rupret007/story-corner-shelf/development/simplified_shelf_concepts/artist_renderings/16b_structural_arch_peg_rails_prompt.md

# Prompt set for selected direction 16B

Generated with the built-in OpenAI image-generation tool. The user's attached concept-16 image was the edit target. A second targeted edit corrected accessory placement.

## Structural and accessory refinement

```text
Use case: precise-object-edit
Asset type: refined photorealistic interior-design concept, option 16B
Input images: Image 1 is the edit target and chosen design.
Primary request: Preserve the exact closet, camera, lighting, exactly two L-shaped shelf levels, shelf positions, thickness, matte-black PETG material, and simple uncluttered character. Change only the support geometry and cable accessories. Make every support one compact structural arched corbel: a broad vertical PETG wall spine plus a thick curved gusset connected continuously into the shelf cassette's deep underside rib. Keep each curve entirely inside its own bracket footprint; never span an arch between adjacent supports.
Cable organization: mold a slim vertical accessory rail into selected ordinary downward spines. Each rail has three keyed rectangular sockets and flush blank caps. Install only a few removable black-PETG accessories: one short rounded single-cable peg, one three-prong cable-comb peg, and one broad rounded J-hook carrying one small neat coil of black cable. Leave most sockets capped. No pegs at the inside corner or directly beside either doorway.
Style/medium: premium photorealistic architectural visualization, simple, strong-looking, practical.
Materials/textures: all visible shelf cassettes, ribs, arches, wall spines, sockets, caps and peg accessories are matte black 3D-printed PETG with subtle fine layer texture.
Constraints: visible shelf system is 100 percent PETG; arch gussets are thick connected structural ribs, not ornamental outlines; pegs are cable-management accessories only; preserve open wall space.
Avoid: wood, wood grain, plywood, steel, metal brackets, brass, visible metal fasteners, floating shelves, full arcade spans, ornate columns, extra shelves, floor supports, clothes, bins, tools, clutter, tangled cables, oversized hooks, corner pegs, text, labels, logos, watermark.
```

## Targeted placement correction

```text
Use case: precise-object-edit
Asset type: corrected photorealistic interior concept, option 16B
Input images: Image 1 is the edit target.
Primary request: Change only the cable-accessory placement. Preserve the entire room, camera, lighting, two shelves, all shelf dimensions, all structural arched corbels, black PETG material, and all other geometry exactly.
Remove the cable coil, peg, comb, accessory sockets, and accessory rails from the support immediately beside the left doorway and the support immediately beside the right doorway. Keep both doorway-adjacent supports completely smooth and empty. Keep the two supports nearest the inside L-corner completely smooth and empty as well.
Relocate the accessories to safe interior supports on the long wall: place one small neat coiled black cable on a broad rounded PETG J-hook on the second interior support from the left, place one three-prong cable-comb peg on the next interior support, and place one short single-cable peg on a middle interior support. Give only these safe interior supports three keyed sockets with unused sockets closed by flush caps. Most supports remain clean.
Constraints: change only accessory placement; no pegs, sockets, rails, or cables beside either doorway or at the inside corner; all shelf/support/accessory components remain matte black PETG; exactly one neat cable coil; no other objects.
Avoid: altering shelf structure, changing arches, adding full arcade spans, extra shelves, wood, metal, clutter, tangled cables, text, labels, logos, watermark.
```
