rupret007/story-corner-shelf/development/simplified_shelf_concepts/artist_renderings/20b_structural_arch_cable_rails_prompt.md

# Prompt for selected direction 20B

Generated with the built-in OpenAI image-generation tool. `20_black_balanced_arch_petg.png` was the edit target.

```text
Use case: precise-object-edit
Asset type: refined photorealistic interior design concept, concept 20B
Input images: Image 1 is the edit target.
Primary request: Refine only the black PETG shelving in Image 1. Preserve the closet, camera, lighting, exactly two L-shaped shelf levels, black material, shelf positions, and overall clean architectural character. Turn every shallow arch below the shelves into a clearly structural PETG arch-rib corbel: a thick curved compression rib connected continuously to a deep underside box rib, a substantial rear wall spine, and the shelf cassette above, so the load path looks integrated rather than like snap-on decoration.
Cable organization: redesign each safe non-corner downward wall spine as a slim vertical modular accessory rail molded into the PETG support. Give the rail three evenly spaced keyed sockets. Populate selected rails with removable all-PETG accessories: a short single-cable peg, a wider three-cable comb peg with three rounded separated hooks, and a broad J-hook for one neatly coiled cable bundle. Leave several sockets fitted with flush blank caps so it remains clean. Show only two small neat dark cable coils as usage examples; keep most pegs empty. All hooks have rounded tips and short upturned retainers. Do not put pegs at the inside corner or beside either doorway.
Style/medium: premium photorealistic architectural visualization; restrained, simple, genuinely useful.
Materials/textures: every shelf cassette, box rib, arch-rib corbel, wall spine, rail, socket, blank cap, and cable peg is matte black 3D-printed PETG with subtle fine layer texture.
Constraints: visible shelf system is 100 percent PETG; no wood or metal; arches must be connected structural ribs, not thin ornamental outlines; pegs are explicitly cable-management accessories, not shelf-load supports; preserve generous clear wall area and an uncluttered appearance.
Avoid: changing the room or camera, extra shelf levels, floor-to-ceiling columns, dense ornament, decorative medallions, metal fasteners, wood grain, steel brackets, unsupported floating shelves, clothes, bins, storage clutter, labels, text, logos, watermark, pegs at corner service zones, tangled cables, oversized hooks, tool storage.
```
