rupret007/story-corner-shelf/development/simplified_shelf_concepts/artist_renderings/prompts_01_05.md

# All-PETG artist-rendering prompts: options 01–05

Generated with the built-in image-generation tool. The local R6 rendering below was supplied as a **composition and room-layout reference only**, never as an edit target:

`PETG_Closet_Shelf/development/r6/assets/artist_rendering_all_petg_two_level_exact_6_plus_3.png`

These are visual concept images, not dimensioned construction drawings. The prompts request a six-bay long run and a three-bay return; final counts, part seams, wall attachment, spans, and capacity must be established by CAD and physical testing.

## 01 — Black minimalist ribbed PETG

```text
Use case: photorealistic-natural
Asset type: homeowner design-choice artist rendering, all-PETG option 01
Primary request: Generate a completely new photorealistic architectural rendering of a simple, strong-looking, tasteful closet shelf system made entirely from visibly 3D-printed PETG. Image 1 is only a reference for the small closet geometry, doorway viewpoint, corner perspective, and two-level L-shaped layout; do not copy its ornate style.
Scene/backdrop: the same kind of small empty white closet, viewed from the doorway toward the inside corner, with plain white walls and ceiling, pale neutral floor, and cropped doorway edges at both sides.
Subject: Exactly two shelf elevations and no others. Each elevation is one continuous L-shaped PETG shelf: a longer run along the back/left wall divided visually into exactly six structural bays and a shorter right-wall return divided into exactly three bays. Build each shelf as a deep matte-black PETG ribbed box-beam cassette with a smooth flat usable top, thick front fascia, and subtle horizontal print-layer texture. Under the cassette, use simple stout triangular PETG corbels at bay divisions, integrated with short vertical PETG mounting blocks against the wall. The mounting blocks visibly meet both wall and shelf and conceal the actual stud fasteners inside them, so the shelf never appears to float. Keep the system minimalist and repeatable, with broad load paths and generous radii rather than delicate detail. Add three small upward-curved cable pegs total on selected lower-level vertical mounting blocks only; the pegs are clearly secondary and unobtrusive.
Style/medium: high-end photorealistic interior product visualization, honest FDM-printed PETG construction, practical rather than sci-fi.
Composition/framing: wide landscape, eye-level architectural camera, straight verticals, closely matching Image 1's corner composition; show both complete L-shaped levels and the long/short runs clearly.
Lighting/mood: soft neutral ceiling light, realistic shadows under every corbel, calm and clean.
Color palette: white room and monochrome matte-black PETG.
Materials/textures: satin-matte black PETG, fine visible layer lines at close inspection, molded-looking but unmistakably 3D printed, consistent plastic sheen; no material substitutions.
Constraints: ALL shelf boards, cassettes, ribs, fascia, corbels, mounting blocks, vertical supports, and cable pegs are PETG; exactly two L-shaped shelf levels; six bays on the long run and three on the short return when visible; physically connected support paths; empty shelves; no floor posts; no visible fasteners or metal.
Avoid: any wood, wood grain, plywood, lumber, steel, metal, brass, chrome, aluminum, metal brackets, stone, glass, impossible floating structure, arches, columns reaching the floor, excessive ornament, extra shelf levels, cabinets, bins, baskets, wire shelving, clothes rods, rails, stored items, people, text, labels, logos, and watermarks.
```

## 02 — Black Art Deco PETG

```text
Use case: photorealistic-natural
Asset type: homeowner design-choice artist rendering, all-PETG option 02
Primary request: Generate a completely new photorealistic architectural rendering of a buildable closet shelf system made entirely from visibly 3D-printed black PETG, using restrained Art Deco geometry. Image 1 is only a reference for the small closet, doorway camera, corner composition, and two-level L-shaped plan; do not copy its ornate architecture.
Scene/backdrop: a small empty white closet viewed from the doorway toward the inside corner, plain white walls and ceiling, pale neutral floor, cropped door jambs at both sides.
Subject: Exactly two shelf elevations. Each elevation is one continuous L-shaped all-PETG shelf: a long back/left-wall run organized into exactly six equal structural bays and a shorter right-wall return organized into exactly three bays. Use deep black PETG torsion-box shelf cassettes with flat usable tops and a modest three-step front fascia. Support them with repeated stout triangular PETG corbels integrated into vertically fluted wall-mounting blocks; each block has only three shallow vertical flutes and a simple stepped foot, giving a clean 1930s Art Deco rhythm without filigree. Concealed fasteners sit inside the printed mounting blocks, with no visible hardware. Make the PETG supports broad, thick, and clearly connected to shelf underside and wall. No cable pegs in this option.
Style/medium: photorealistic high-end residential interior product rendering, restrained geometric Art Deco, honest FDM-plastic construction.
Composition/framing: wide landscape architectural view, eye-level, straight verticals, closely matching Image 1's useful corner framing; both complete shelf levels and both returns visible.
Lighting/mood: soft neutral ceiling light with controlled shadows that reveal the step and flute geometry, polished but believable.
Color palette: bright white closet and satin black PETG only.
Materials/textures: consistent satin-black PETG with fine horizontal layer lines, subtle plastic sheen, printed seams at repeatable module joints, no imitation of wood or metal.
Constraints: every shelf board/cassette, fascia, rib, corbel, wall block, vertical support, and decorative detail is PETG; exactly two L-shaped levels; six long-run bays and three return bays when visible; strong-looking connected load paths; empty room; no floor posts; no exposed fasteners.
Avoid: wood, wood grain, plywood, lumber, steel, metal, brass, gold, chrome, aluminum, metal brackets, stone, glass, floating shelves, pointed Gothic arches, ornate columns, excessive ornament, fan/sunburst motifs, extra shelf levels, cabinets, bins, baskets, rails, rods, hooks, pegs, wires, stored items, people, text, labels, logos, and watermarks.
```

## 03 — Black restrained neo-Gothic PETG

```text
Use case: photorealistic-natural
Asset type: homeowner design-choice artist rendering, all-PETG option 03
Primary request: Generate a completely new photorealistic architectural rendering of a simple, strong-looking closet shelf system made entirely from visibly 3D-printed black PETG, with a restrained neo-Gothic structural motif. Image 1 is only a reference for the small closet geometry, doorway viewpoint, corner perspective, and two L-shaped shelf elevations; radically simplify its ornament.
Scene/backdrop: a small empty white closet viewed from its doorway toward the inside corner, plain white walls and ceiling, pale floor, narrow doorway edges visible on both sides.
Subject: Exactly two shelf elevations, no more. Each is one continuous L-shaped PETG shelf with a long back/left-wall run organized into exactly six equal structural bays and a short right-wall return organized into exactly three bays. Use thick black PETG hollow box-cassette shelves with smooth flat usable tops and a plain narrow fascia. Below each shelf, repeated stout PETG wall trusses define a single shallow pointed arch per bay: two broad diagonal ribs rise from compact vertical wall-mount blocks to the shelf underside and meet in a restrained pointed apex. Keep ribs chunky and engineering-led, with generous radii and no tiny decoration. Concealed stud fasteners are fully hidden inside the PETG wall blocks, leaving no visible metal. Make every support visibly contact wall and underside, with a credible uninterrupted load path. No cable pegs in this option.
Style/medium: high-end photorealistic residential interior product visualization; modern neo-Gothic restraint, not fantasy architecture; honest FDM-printed plastic.
Composition/framing: wide landscape architectural view, eye-level camera, straight verticals, closely matching Image 1's corner composition; show both complete L-shaped levels and both runs.
Lighting/mood: soft neutral ceiling light; gentle realistic shadows clarify the pointed trusses; calm and uncluttered.
Color palette: white closet and monochrome satin-black PETG.
Materials/textures: consistent PETG plastic sheen, visible fine layer texture and modular print seams, no imitation wood or metal.
Constraints: all shelf cassettes, fascia, ribs, trusses, corbels, wall blocks, and vertical supports are PETG; exactly two L-shaped levels; six long-run bays plus three return bays when visible; empty room; connected and strong-looking; no floor posts; no exposed hardware.
Avoid: wood, wood grain, plywood, lumber, steel, metal, brass, gold, chrome, aluminum, metal brackets, stone, glass, floating shelves, elaborate arches, tracery, finials, columns, capitals, dentils, ornamental overload, extra shelf levels, cabinets, bins, baskets, rails, clothes rods, hooks, cable pegs, cables, stored items, people, text, labels, logos, and watermarks.
```

## 04 — Warm-ivory mid-century PETG

```text
Use case: photorealistic-natural
Asset type: homeowner design-choice artist rendering, all-PETG option 04
Primary request: Generate a completely new photorealistic architectural rendering of a simple, strong-looking closet shelf system made entirely from visibly 3D-printed warm-ivory PETG, with restrained mid-century rounded geometry. Image 1 is only a reference for the small closet, doorway camera, inside-corner composition, and two L-shaped shelf elevations; do not copy its ornate black architecture.
Scene/backdrop: a small empty white closet viewed from the doorway toward the inside corner, plain white walls and ceiling, pale neutral floor, door jambs cropped at both sides.
Subject: Exactly two shelf elevations. Each elevation is one continuous L-shaped all-PETG shelf: a long run on the back/left wall arranged into exactly six equal structural bays and a shorter right-wall return arranged into exactly three bays. Construct each from modular warm-ivory PETG hollow shelf cassettes with smooth flat usable tops, a softly rounded bullnose-like PETG front fascia, and internal printed ribs. Below, use broad rounded triangular PETG web corbels integrated with capsule-ended vertical PETG wall-mount blocks, all at realistic bay divisions. Keep the forms thick, simple, repeatable, and friendly—subtle 1950s product-design softness, not decorative furniture. Concealed fasteners are fully hidden inside the printed wall blocks; no hardware is visible. Add exactly three modest molded PETG cable pegs on selected lower-level wall blocks, each a short rounded upward hook; keep all other supports peg-free.
Style/medium: high-end photorealistic residential interior product visualization, soft mid-century modern geometry, honest FDM PETG construction.
Composition/framing: wide landscape architectural view at eye level with straight verticals, closely matching Image 1's corner framing; show both complete L-shaped levels, long run, and short return.
Lighting/mood: warm-neutral ceiling illumination with gentle shadows, bright and welcoming, realistic rather than stylized.
Color palette: clean white room, solid warm ivory PETG with a slight cream tone.
Materials/textures: uniform satin PETG plastic, fine print-layer texture and clean module seams; the shelf surface is plastic, never timber.
Constraints: all shelf cassettes, fascia, ribs, corbels, wall blocks, vertical supports, and pegs are PETG; exactly two L-shaped levels; six long-run bays and three return bays when visible; empty shelves; visible connected load paths; no floor posts; no exposed hardware.
Avoid: any wood or wood grain, plywood, lumber, steel, metal, brass, chrome, aluminum, metal brackets, stone, glass, ceramic, floating spans, skinny delicate brackets, ornate arches, columns, excessive ornament, extra shelf levels, cabinets, bins, baskets, wire shelving, clothes rods, rails, dangling cables, stored objects, people, text, labels, logos, and watermarks.
```

## 05 — Graphite industrial hex-rib PETG

```text
Use case: photorealistic-natural
Asset type: homeowner design-choice artist rendering, all-PETG option 05
Primary request: Generate a completely new photorealistic architectural rendering of a simple, strong-looking closet shelf system made entirely from visibly 3D-printed graphite PETG, using a clean industrial box-beam and hex-rib language. Image 1 is only a reference for the small closet dimensions, doorway viewpoint, corner composition, and two L-shaped shelf elevations; do not copy its ornate styling.
Scene/backdrop: small empty white closet viewed from the doorway toward the inside corner, plain white walls and ceiling, pale neutral floor, cropped doorway edges on both sides.
Subject: Exactly two shelf elevations. Each elevation is one continuous L-shaped all-PETG shelf with a long back/left-wall run organized into exactly six equal structural bays and a short right-wall return organized into exactly three bays. Construct each shelf as a deep graphite PETG hollow box-beam cassette with a flat usable top and thick squared front fascia. Expose a restrained band of large hexagonal PETG rib cells only along the underside edge of each cassette, showing efficient printed structure without making the shelf transparent. At each bay division, use broad trapezoidal triangular PETG wall corbels with one large hexagonal relief recess, integrated into compact vertical PETG mounting blocks. Concealed wall fasteners are fully enclosed inside those printed blocks; no hardware is visible. Use thick walls, generous radii, modular seams, and unmistakable wall-to-shelf support paths. No cable pegs in this option.
Style/medium: high-end photorealistic residential interior product visualization, practical modern industrial design, clean and non-sci-fi, honest FDM-printed PETG.
Composition/framing: wide landscape architectural view at eye level, straight verticals, closely matching Image 1's useful corner perspective; show both complete L-shaped levels and their returns.
Lighting/mood: soft neutral ceiling illumination, slightly crisp shadows revealing the box beams and ribs, realistic and uncluttered.
Color palette: white room with dark graphite-gray PETG, slightly lighter than pure black.
Materials/textures: uniform satin graphite PETG, fine layer lines, clean printed module seams, subtle plastic highlights; no imitation wood or metal.
Constraints: every shelf cassette, fascia, rib, corbel, wall block, vertical support, and detail is PETG; exactly two L-shaped shelf levels; six bays on the long run and three on the return when visible; empty room; clearly connected, strong-looking supports; no floor posts; no exposed fasteners.
Avoid: wood, wood grain, plywood, lumber, steel, metal, brass, chrome, aluminum, metal brackets, stone, glass, floating shelves, delicate lattice, too many tiny honeycomb cells, sci-fi styling, ornate arches or columns, excessive decoration, extra shelf levels, cabinets, bins, baskets, wire shelves, clothes rods, rails, hooks, cable pegs, cables, stored objects, people, text, labels, logos, and watermarks.
```

## Output integrity

All five outputs are 1402 × 1122 RGB PNG files.

| Option | SHA-256 |
|---|---|
| 01 | `de3290150ccf452ccfb7a92a355a951145b68a479858203dd4aff9b2434f6baa` |
| 02 | `096d438ebaca7fce1ca392134fc2b79f3b26f1ee5fe743c686d0c37734d52820` |
| 03 | `af0a7cd655bbc1c4f5e5372070d07635cc91f2d2ef08f0457324ce3e53284ea7` |
| 04 | `49f438642b49dfc43f2479005391840f2a148941027841da71490a4509df7230` |
| 05 | `f2b01746c13d5d59c1ebb1ebba1d18e984cb3cb254cd7d053d04ff8c1e557896` |

## Visual QA

- All five show exactly two shelf elevations in the same small corner-closet composition.
- Every visible shelf cassette, fascia, rib, corbel, truss, mounting block, and peg reads as one consistent PETG material family; no wood grain or visible metal hardware appears.
- All shelves are empty, with no people, storage props, text, logos, or watermarks.
- Supports visibly connect the wall-mounting blocks to the shelf undersides; none rely on an unexplained floating span.
- Options 01 and 04 include a few unobtrusive cable pegs; options 02, 03, and 05 intentionally omit them.
- These renderings communicate visual direction. Apparent module spacing/count can drift in generative imagery, so exact six-plus-three topology must be enforced in CAD rather than inferred from pixels.
