rupret007/story-corner-shelf/development/simplified_shelf_concepts/artist_renderings/prompts_06_10.md

# Image-generation prompts: concepts 06–10

Generation method: built-in ImageGen, one generation call per final asset.

The previously viewed R6 rendering was used only as a room/composition reference. It was not edited or supplied as an edit target.

## 06 — Bone-white organic PETG

Output: `06_bone_white_organic_petg.png`

```text
Use case: photorealistic-natural
Asset type: homeowner closet shelving concept rendering, option 06
Primary request: Create a highly photorealistic artist rendering of an elegant, strong-looking, entirely 3D-printed PETG closet shelving system. Use the same compact white closet and corner-camera composition as the previously viewed reference: doorway edges at left and right, a long back-wall run turning onto a shorter right-wall return.
Subject/layout: exactly TWO L-shaped horizontal shelf levels total, one upper and one lower. At each level, the long back-wall run is organized into exactly SIX equal structural bays and the short right-wall return into exactly THREE structural bays. Each shelf surface is a believable modular PETG cassette with underside ribs; repeated vertical PETG mounting blocks and deep PETG corbels clearly carry the load into concealed wall fasteners. The shelves must not look like unsupported floating slabs.
Design theme: monochrome warm bone-white PETG with simple organic softened arches beneath each cassette, gently radiused edges and calm proportions. Reduce ornament: one clean arch opening per bay, a continuous modest fascia, sturdy broad corbel roots. Everything visible—shelf cassettes, ribs, fascia, arches, corbels, rails, covers and vertical supports—is printed PETG.
Style/medium: photorealistic architectural product visualization that resembles a real finished FDM print installation, not concept sketch or fantasy architecture.
Composition/framing: wide corner view showing both L-shaped levels and enough of the right return to understand the 6-bay plus 3-bay rhythm; shelves empty.
Lighting/mood: bright soft ceiling illumination, refined and uncluttered.
Color/material: satin bone-white PETG throughout, subtle realistic FDM layer lines on close edges, consistent plastic sheen, clean seams between printable modules.
Constraints: exactly two shelf levels; all structural and decorative visible components must unmistakably read as 3D-printed PETG; credible repeated supports and load path; clean empty closet.
Avoid: wood, wood grain, plywood, timber, steel, brass, aluminum, any metal-looking bracket, stone shelves, unsupported floating shelves, people, clothes, boxes, bins, stored items, rods, drawers, cabinets, extra shelf levels, extra rails, columns reaching to floor, gothic ornament, heavy clutter, text, labels, logos, watermark.
```

## 07 — Charcoal Japanese-minimal PETG

Output: `07_charcoal_japanese_minimal_petg.png`

```text
Use case: photorealistic-natural
Asset type: homeowner closet shelving concept rendering, option 07 replacement
Primary request: Create a highly photorealistic artist rendering of a refined, strong-looking, entirely 3D-printed PETG storage-shelf system in a compact white closet. Use a wide corner camera with doorway edges at both sides, a long back wall, and a shorter right-wall return.
Subject/layout: exactly TWO L-shaped horizontal shelf levels total, one upper and one lower. Each level must have a broad, continuous, solid-depth horizontal PETG storage deck about 12 inches deep—clearly usable for boxes and ordinary storage, although the shelves remain empty. Build each deck from six visibly joined PETG cassette modules along the long back-wall run and three PETG cassette modules along the short right-wall return. Show clean cassette seams on the front fascia and subtle structural ribs only on the underside. Support each shelf from below with repeated deep, simple rectangular or gently haunched charcoal-PETG corbels and matching printed wall mounting blocks at every cassette boundary. Concealed wall fasteners may be inside these printed blocks. The load path must be obvious.
Design theme: Japanese-minimal monochrome charcoal PETG—quiet rectilinear forms, restrained bevels, softly eased corners, disciplined spacing, and no applied ornament. Add only two or three small simple upward cable pegs integrated into selected lower corbel mounting blocks, made from the same charcoal PETG.
Critical geometry: the upper shelf and lower shelf are completely separate. No vertical frame, post, ladder, rail, or panel may bridge the open wall space between the two shelf levels. All supports terminate below the shelf they support. No rail runs across the front or below either shelf.
Style/medium: photorealistic architectural product rendering of a practical real FDM-print installation, not concept sketch or fantasy structure.
Composition/framing: eye-level wide corner view showing two clearly horizontal, solid storage surfaces, the long run, and the three-cassette right return; shelves and floor empty.
Lighting/mood: soft neutral ceiling light, calm and uncluttered.
Color/material: satin charcoal-gray PETG only, subtle FDM layer lines, clean modular seams, consistent nonmetallic plastic highlights.
Constraints: every visible deck cassette, underside rib, fascia, corbel, wall block, peg, connector and cover is 3D-printed PETG; exactly two usable shelf levels; credible repeated support; no other visible material.
Avoid: open ladder frames, vertical posts connecting the two levels, extra horizontal rails, shallow ledges, wood, wood grain, plywood, steel, brass, aluminum, metal brackets, metallic sheen, stone, unsupported floating slabs, people, clothes, boxes, bins, stored items, rods, cabinets, drawers, extra shelf levels, floor-standing columns, arches, fussy ornament, clutter, text, logos, labels, watermark.
```

## 08 — Black/ivory modular-grid PETG

Output: `08_black_ivory_modular_grid_petg.png`

```text
Use case: photorealistic-natural
Asset type: homeowner closet shelving concept rendering, option 08
Primary request: Create a highly photorealistic artist rendering of a strong, modular, entirely 3D-printed PETG closet shelving system in a compact white closet. Keep the established corner-camera room composition: long back wall and shorter right-wall return, doorway trim at the frame edges.
Subject/layout: exactly TWO L-shaped horizontal shelf levels total, one upper and one lower. On EACH level, clearly organize the long back-wall shelf into exactly SIX equal cassette bays and the short right-wall return into exactly THREE equal cassette bays. Each bay is a printable rectangular shelf cassette with a visible square-cell underside rib grid, joined edge-to-edge. Repeated deep rectangular PETG corbels and PETG wall mounting blocks below every cassette boundary make the load path visually credible; concealed fasteners may be inside those printed blocks. The shelves must not float.
Design theme: crisp two-tone modular system. Ivory PETG forms the shelf deck cassettes and narrow front fascia; matte black PETG forms the square-grid underside ribs, wall mounting blocks, and simple rectangular corbels. Use a disciplined square geometry, even rhythm and flush printable seams, with no decorative columns or arches.
Style/medium: photorealistic architectural product visualization of a real FDM printed installation; sophisticated but practical and repeatable.
Composition/framing: wide eye-level corner view showing both L-shaped levels and their 6-plus-3 modular bay pattern; empty shelves; uncluttered floor.
Lighting/mood: bright neutral ceiling lighting, clean graphic contrast, soft realistic shadows.
Materials/textures: only satin ivory PETG and matte black PETG, subtle FDM layer lines and believable molded-plastic-like highlights, no metallic reflections.
Constraints: every visible shelf cassette, square rib, fascia, corbel, wall block, connector and cover is 3D-printed PETG; exactly two horizontal shelf levels; credible dense support; no unsupported spans.
Avoid: wood, wood grain, plywood, timber, steel, brass, aluminum, metal brackets, metallic sheen, stone, unsupported floating shelves, people, stored items, boxes, bins, clothes, plants, hanging rods, cabinets, drawers, extra shelf levels, extra horizontal rails, floor-standing columns, arches, ornate details, clutter, text, labels, logos, watermark.
```

## 09 — Black retro-futurist PETG

Output: `09_black_retro_futurist_petg.png`

```text
Use case: photorealistic-natural
Asset type: homeowner closet shelving concept rendering, option 09
Primary request: Create a highly photorealistic artist rendering of a strong-looking, entirely 3D-printed PETG closet shelving system with restrained retro-futurist character. Use the same compact white closet and wide corner-camera composition: long back-wall shelf run turning onto a shorter right-wall return, door trim near both frame edges.
Subject/layout: exactly TWO L-shaped horizontal shelf levels total, one upper and one lower. On EACH level, the long back-wall run has exactly SIX repeated structural bays and the short right-wall return has exactly THREE repeated bays. Modular ribbed PETG shelf cassettes sit on broad wall-mounted PETG corbels at every bay boundary. The corbels are deep, thick, and clearly anchored through rounded PETG mounting pods that conceal the wall fasteners, making the support strategy obvious rather than floating.
Design theme: monochrome black PETG with late-1960s/retro-futurist rounded geometry—smooth capsule-ended fascia modules, broad soft triangular corbels with oval lightening openings, matte ribbed undersides, and glossy outer edge caps. Keep the silhouette clean and practical, not spaceship scenery. Integrate a few small rounded cable pegs into selected support pods, printed in matching black PETG.
Style/medium: photorealistic architectural product visualization of a real premium FDM printed installation, believable printable module seams and proportions.
Composition/framing: wide eye-level corner view showing both L-shaped shelf levels, the full 6-bay long rhythm, and 3-bay right return; shelves and floor empty.
Lighting/mood: bright soft ceiling light with controlled highlights that distinguish satin, matte, and glossy black PETG surfaces.
Color/material: black PETG only, alternating satin fascia, matte ribs, and a few gloss edge caps; subtle FDM layer texture; absolutely no metallic reflection.
Constraints: every visible cassette, rib, fascia, corbel, mounting pod, connector, peg and cover is 3D-printed PETG; exactly two levels; credible repeated load supports.
Avoid: wood, wood grain, plywood, steel, brass, aluminum, metal brackets, chrome, metallic sheen, stone, unsupported floating shelves, people, stored items, boxes, bins, clothes, rods, cabinets, drawers, extra shelf levels, extra rails, floor-standing columns, ornate gothic details, clutter, text, labels, logos, watermark.
```

## 10 — Forest-green parametric PETG

Output: `10_forest_green_parametric_petg.png`

```text
Use case: photorealistic-natural
Asset type: homeowner closet shelving concept rendering, option 10
Primary request: Create a highly photorealistic artist rendering of an elegant, strong-looking, entirely 3D-printed PETG closet shelving system with a restrained parametric structural design. Use the established compact white closet and wide corner view: long back wall turning onto a shorter right-wall return, doorway trim at the outer edges.
Subject/layout: exactly TWO L-shaped horizontal shelf levels total, one upper and one lower. On EACH level, the long back-wall shelf has exactly SIX equal structural bays and the short right-wall return has exactly THREE equal structural bays. Modular PETG shelf cassettes have thick faceted underside ribs. At every bay boundary a broad branching PETG corbel grows from a deep faceted PETG wall mounting block into two support arms under adjacent cassettes; concealed wall fasteners sit inside those printed blocks. The repeated load path must look sturdy and explicit, never like floating shelves.
Design theme: monochrome deep forest-green PETG with controlled parametric faceting—low-poly branching Y-ribs, chamfered cassette fronts, geometric triangular webs, and clean repeatable module seams. Strong architectural rhythm without ornate historic decoration. Add two or three discreet upward cable pegs molded into selected lower wall blocks, matching the same green PETG.
Style/medium: photorealistic architectural product visualization of a real FDM printed installation, realistic scale and manufacturable surfaces.
Composition/framing: wide eye-level corner perspective showing both L-shaped levels and as much of the exact six-bay plus three-bay arrangement as possible; empty shelves and floor.
Lighting/mood: soft bright ceiling light with subtle directional highlights revealing the facets, refined and uncluttered.
Color/material: satin deep forest-green PETG only, subtle FDM layer lines, crisp printed chamfers, no metallic or wood-like reflections.
Constraints: every visible cassette, rib, web, fascia, corbel, mounting block, connector, peg and cover is 3D-printed PETG; exactly two levels; credible dense repeated support.
Avoid: wood, wood grain, plywood, timber, steel, brass, aluminum, any metal bracket or metallic sheen, stone, unsupported floating shelves, people, stored items, boxes, bins, clothes, rods, drawers, cabinets, extra shelf levels, extra rails, floor-standing columns, gothic arches, excessive organic sculpture, clutter, text, labels, logos, watermark.
```

## Visual QA

- All five images show exactly two L-shaped shelf levels in an empty white closet.
- No wood, wood grain, brass, steel, aluminum, or other visibly non-PETG structural material remains in these five assets.
- Every concept shows repeated wall-mounted printed supports instead of unsupported floating slabs.
- Concepts 07, 09, and 10 include small integrated printed cable pegs.
- Bay counts are encoded explicitly in every prompt. Perspective and edge cropping make a few end bays partially visible; these images remain artist renderings rather than dimensional placement drawings.
