rupret007/story-corner-shelf/development/simplified_shelf_concepts/artist_renderings/prompts_11_15.md

# All-PETG artist rendering prompts — options 11–15

Generation mode: built-in ImageGen, one call per asset.

Reference image for room, camera, and two-level L-shaped topology:

`PETG_Closet_Shelf/development/r6/assets/artist_rendering_all_petg_two_level_exact_6_plus_3.png`

These are visual design studies, not engineering drawings or load certifications. Every option intentionally depicts an all-PETG visible shelf system; hidden attachment methods are represented only conceptually.

## 11 — Black restrained classical arcade PETG

```text
Use case: precise-object-edit
Asset type: photorealistic residential closet shelving concept, option 11
Input image: Image 1 is the edit target and geometry reference.
Primary request: simplify and redesign only the shelving system as a restrained classical arcade made entirely from black PETG. Preserve the compact white closet, exact camera position, ceiling, doors, walls, floor, lighting, inside corner, and exactly two L-shaped shelf levels from Image 1.
Exact layout invariant: exactly TWO shelf levels total. On EACH level, preserve one continuous L-shaped run with exactly SIX evenly spaced structural bays across the long left/back wall and exactly THREE bays on the shorter right-wall return. Make the nine-bay rhythm countable and identical on both levels. Shelves stay completely empty.
All-PETG construction: every visible shelf cassette, top skin, deep underside rib, wall block, corbel, pier/column, fascia, connector cover, cable peg, and trim piece is FDM-printed black PETG. Absolutely no wood, wood grain, plywood, steel, aluminum, brass, metal brackets, or exposed hardware. Use convincing satin black PETG with subtle layer lines and molded-looking edges. Hidden anchors may exist only concealed inside thick printed wall blocks.
Design: strong-looking modular shelf cassettes with a shallow restrained arcade under the fascia. Use square simplified piers, broad triangular printed PETG corbels, thick wall blocks, and clearly connected underside ribs so the load path from shelf to wall reads as credible rather than floating. Classical proportion without ornate carving. Add only two or three small integrated cable pegs at natural outer pier positions; keep them secondary and empty.
Style/medium: high-end photorealistic architectural product visualization, physically plausible FDM PETG, clean installation.
Composition/lighting: retain the reference wide corner perspective and realistic neutral ceiling lighting; both long run and return fully visible; straight verticals, realistic contact shadows.
Constraints: only two shelf levels; 6+3 bays on each level; 100% black PETG visible construction; empty shelves; practical, sturdy, restrained.
Avoid: people, stored objects, bins, rods, hanging rails, wires, labels, text, logos, watermark, extra shelf levels, mixed materials, wood texture, any metal, exposed screws, implausible cantilevers, excessive ornament, and freestanding floor supports.
```

## 12 — Cream contemporary scalloped PETG

```text
Use case: precise-object-edit
Asset type: photorealistic residential closet shelving concept, option 12
Input image: Image 1 is the edit target and geometry reference.
Primary request: redesign only the shelving system as a clean contemporary radius-corner system made entirely from warm cream PETG. Preserve Image 1's compact white closet, camera position, ceiling, doors, walls, floor, lighting, inside corner, and exactly two L-shaped shelf levels.
Exact layout invariant: exactly TWO shelf levels total. On EACH level, preserve one continuous L-shaped run with exactly SIX clearly countable structural bays across the long left/back wall and exactly THREE bays on the shorter right-wall return. Repeat the same 6+3 rhythm on upper and lower levels. Shelves completely empty.
All-PETG construction: every visible shelf cassette, top skin, rounded fascia, underside rib, wall block, radius corbel, short pier, connector cover, cable peg, and trim part is FDM-printed warm ivory/cream PETG. Absolutely no wood or wood grain, no steel, aluminum, brass, or other metal, and no exposed hardware. Hidden attachments exist only inside substantial printed wall blocks.
Design: contemporary, friendly and uncluttered. Use thick modular cream shelf cassettes with generous rounded front corners, softly scalloped fascia segments aligned to each bay, broad printed PETG radius corbels with crescent-shaped negative space, and short rectangular wall piers. Expose enough ribs and wall blocks that the system looks genuinely supported, not floating. Subtle FDM layer texture, matte-satin cream finish. Include at most two small integrated cable pegs at useful end-pier locations; empty and visually secondary.
Style/medium: premium photorealistic architectural product rendering, credible FDM PETG construction.
Composition/lighting: same wide inside-corner view as Image 1, neutral warm ceiling illumination, realistic contact shadows and straight verticals, both runs plainly visible.
Constraints: exactly two shelf levels; exactly 6+3 bays per level; 100% cream PETG visible system; strong-looking and practical; empty shelves.
Avoid: people, objects, bins, rods, rails, dangling wires, text, labels, logos, watermark, extra levels, floating shelves, mixed colors or materials, wood texture, any metal, exposed screws, thin implausible cantilevers, classical ornament, columns extending far below, and over-decoration.
```

## 13 — Graphite brutalist PETG

```text
Use case: precise-object-edit
Asset type: photorealistic residential closet shelving concept, option 13
Input image: Image 1 is the edit target and geometry reference.
Primary request: redesign only the shelving system as a bold but simple brutalist modular system made entirely from graphite-gray PETG. Preserve Image 1's compact white closet, exact camera angle, ceiling, doors, walls, floor, lighting, inside corner, and two L-shaped shelf levels.
Exact layout invariant: exactly TWO shelf levels total. On EACH level, retain one continuous L-shaped shelf with exactly SIX clearly countable bays along the long left/back wall and exactly THREE bays on the shorter right return. The bay rhythm repeats between levels. Shelves completely empty.
All-PETG construction: every visible shelf cassette, box beam, underside grid rib, wall block, rectangular corbel, fascia, connector cover, peg, and trim cap is FDM-printed graphite PETG. Absolutely no wood, wood grain, steel, aluminum, brass, metal brackets, or exposed hardware. Anchors are concealed inside deep printed wall mounting blocks.
Design: strong, chunky, geometric brutalism without decoration. Build each run from thick hollow box-rib shelf cassettes with broad flat graphite fascia. Under each bay show one deep rectangular wall block joined to a short trapezoidal box corbel and a visible cross-rib under the shelf, so the load path looks robust and credible. Large chamfers on exposed edges, disciplined repeating modules, matte graphite with subtle PETG layer bands. Keep vertical supports short and functional rather than ornamental. Add one or two very small empty integrated cable pegs only at outer side blocks.
Style/medium: photorealistic architectural product visualization, realistic FDM texture, physically convincing joints and contact shadows.
Composition/lighting: preserve the same wide corner view, neutral ceiling light, straight verticals, both long and return runs plainly visible.
Constraints: exactly two levels; exactly 6+3 bays on each; 100% graphite PETG visible structure; empty shelves; visibly supported and strong.
Avoid: people, stored objects, bins, rods, rails, wires, labels, text, logos, watermark, third shelf, mixed materials or colors, wood texture, any metal, exposed screws, floating shelf appearance, thin cantilevers, arches, classical columns, ornate trim, and floor supports.
```

## 14 — White aerofoil truss PETG

```text
Use case: precise-object-edit
Asset type: photorealistic residential closet shelving concept, option 14
Input image: Image 1 is the edit target and geometry reference.
Primary request: redesign only the shelving system as a lightweight-looking but credible aerofoil-and-rib truss system made entirely from white PETG. Preserve Image 1's compact white closet, camera position, ceiling, doorways, walls, floor, lighting, inside corner, and exactly two L-shaped shelf levels.
Exact layout invariant: exactly TWO shelf levels total. On EACH level, preserve one continuous L-shaped run with exactly SIX countable structural bays along the long left/back wall and exactly THREE bays along the shorter right-wall return, the same on upper and lower levels. Both shelves empty.
All-PETG construction: every visible shelf cassette, top skin, aerodynamic fascia shell, underside rib, diagonal truss, wall mounting block, corbel, connector cover, small peg, and trim cap is FDM-printed matte white PETG. Absolutely no wood, wood grain, steel, aluminum, brass, metal brackets, cables, or exposed hardware. Conceal anchors inside printed white wall blocks.
Design: clean engineered lightweight aesthetic inspired by an aircraft wing. Use slim but substantial hollow shelf cassettes with a gently rounded aerofoil front fascia. Beneath each bay show a repeatable white PETG triangular truss: a short wall block, one graceful diagonal strut, and two or three closely spaced transverse ribs under the shelf. Use small radiused lightening openings only within thick ribs, never long unsupported spans. The repeated trusses must make the load path obvious and structurally credible rather than floating. Subtle FDM layer lines and seam joints. Add at most two tiny integrated cable pegs to outer wall blocks, empty.
Style/medium: photorealistic architectural product visualization; crisp, minimal, technically elegant.
Composition/lighting: same wide inside-corner framing, soft neutral light and realistic contact shadows that distinguish white PETG from white wall; both runs visible; straight verticals.
Constraints: exactly two L shelf levels; exactly 6+3 structural bays each; 100% white PETG visible system; empty; sturdy-looking despite lighter visual weight.
Avoid: people, stored items, bins, rods, rails, wires, labels, text, logos, watermark, extra shelf surfaces, mixed materials, wood texture, any metal, exposed screws, floating shelf illusion, implausible thin members, ornate arches or columns, and floor supports.
```

## 15 — Black practical snap-trim PETG

```text
Use case: precise-object-edit
Asset type: photorealistic residential closet shelving concept, option 15 and the most practical option in the set
Input image: Image 1 is the edit target and geometry reference.
Primary request: redesign only the shelving system as simple straight modular shelves made entirely from black PETG, with small repeatable snap-on arch/corbel covers for a little character. Preserve Image 1's compact white closet, exact camera position, ceiling, doors, walls, floor, lighting, inside corner, and exactly two L-shaped shelf levels.
Exact layout invariant: exactly TWO shelf levels total. On EACH level, preserve one continuous L-shaped run with exactly SIX clearly countable support bays along the long left/back wall and exactly THREE bays on the shorter right return. Repeat the same 6+3 module layout on both levels. Shelves entirely empty.
All-PETG construction: every visible straight shelf cassette, top skin, internal/underside rib, compact wall block, triangular corbel, snap-on cover, fascia, connector cover, cable peg, and trim cap is FDM-printed satin black PETG. Absolutely no wood, wood grain, steel, aluminum, brass, metal bracket, or exposed hardware. Wall attachments are concealed inside thick printed mounting blocks.
Design: practical, strong, easy-to-print modular kit. Use simple square-edged black shelf cassettes with a plain thin fascia. At every bay, show a short rectangular printed wall block and one broad triangular ribbed PETG corbel directly under the shelf so there are no implausible unsupported spans. Each identical corbel has a small removable snap-on face cover featuring one shallow arch cutout; the arch is only a modest cosmetic accent, not a tall column or load-bearing fantasy. Repeat the exact same compact module. Use visible cassette seams at rational bay boundaries and subtle FDM layer texture. Include two or three small empty integrated cable pegs on selected outer wall blocks, not at the inside corner.
Style/medium: highly photorealistic architectural product visualization, understated, clean, credible and attainable.
Composition/lighting: same wide inside-corner perspective, neutral ceiling lighting, realistic PETG sheen and contact shadows, both runs fully visible.
Constraints: exactly two shelf levels; exactly 6+3 support bays per level; 100% black PETG visible system; empty shelves; every span visibly supported; least ornate and most practical of the five.
Avoid: people, stored objects, bins, rods, rails, dangling wires, labels, text, logos, watermark, extra shelf levels, mixed materials, wood texture, any metal, exposed screws, floating shelf illusion, long thin cantilevers, tall decorative columns, ornate classical trim, excessive arches, and floor supports.
```
