rupret007/story-corner-shelf/development/simplified_shelf_concepts/artist_renderings/prompts_16_20.md

# Artist-rendering prompts 16–20

All five images were generated with the built-in OpenAI image-generation tool. The existing exact two-level R6 closet rendering was supplied only as a room, camera, and composition reference. These are artistic concepts, not validated CAD or load evidence.

## 16 — Black radiused corbels

```text
Use case: photorealistic-natural
Asset type: interior design concept rendering, option 16 of 20
Input image: Image 1 is a room and camera-composition reference only; redesign the shelving.
Primary request: Reimagine the same compact corner closet with a much simpler, genuinely all-polymer two-level L-shaped shelving system. Every visible and structural shelf component is 3D-printed matte black PETG: flat cassette decks, deep underside ribs, broad radiused triangular corbels, compact wall mounting blocks, fascia, and vertical pier covers. There is no wood and no metal anywhere in the shelving. Add a few simple rounded cable pegs molded into the non-corner vertical pier covers, clearly usable but visually quiet.
Scene/backdrop: preserve the small clean white closet, gray tile floor, two door openings, ceiling light, corner viewpoint, long wall and short return.
Style/medium: high-end photorealistic architectural interior visualization, realistic large-format printed PETG texture, credible assembled construction.
Composition/framing: exactly two horizontal L-shaped shelf levels, six bays on the long run and three bays on the short return where perspective permits; generous visible wall between and below; repeated printed corbels make the load path obvious.
Lighting/mood: warm neutral ceiling light, realistic soft shadows, simple and handsome.
Materials/textures: uniform matte black PETG with subtle layer texture and lightly textured top surfaces; white drywall and gray tile only.
Constraints: shelf system is 100 percent PETG; all structure must look printed and mechanically supported, never floating; simplified design with no elaborate ornament; cable pegs only on safe non-corner supports.
Avoid: wood, wood grain, plywood, lumber, steel, brass, bronze, metal brackets, mixed materials, people, stored objects, clothes, bins, baskets, labels, text, logos, watermark, extra shelf levels, hanging rails, unsupported floating shelves, fantasy joinery, excessive arches or columns.
```

## 17 — Smoke honeycomb

```text
Use case: photorealistic-natural
Asset type: interior design concept rendering, option 17 of 20
Input image: Image 1 is a room and camera-composition reference only; redesign all shelving.
Primary request: Create an elegant fully 3D-printed PETG shelving concept for the same closet. Use two L-shaped shelf levels made from deep smoke-gray translucent PETG cassette decks with clearly visible internal honeycomb and cellular ribs, supported by opaque graphite PETG wall piers and forked Y-shaped printed corbels. All structural and decorative pieces are PETG; there is no wood or metal. The translucent fascia reveals the structural lattice in a controlled, high-end way.
Scene/backdrop: same small white closet, corner, gray tile floor, left and right door openings, ceiling light, long wall and short return.
Style/medium: photorealistic architectural product visualization, clean futuristic utility, realistic translucent polymer and additive-manufactured surfaces.
Composition/framing: exactly two horizontal L-shaped shelf levels, long run and short return; open wall below; repeat the same compact support module rhythm.
Lighting/mood: soft warm-white ceiling light shining subtly through smoked PETG edges, calm and refined.
Materials/textures: smoke-transparent PETG shelf shells, graphite matte PETG piers and corbels, white drywall.
Constraints: 100 percent PETG shelf system; credible ribbed load paths and positive wall supports; restrained and easy to understand; a couple of small printed cable pegs on interior piers only.
Avoid: any wood, wood grain, plywood, steel, aluminum, brass, screws shown as metal, mixed-material shelves, floating slabs, people, objects, bins, clothes, rails, text, labels, logos, watermark, extra levels, ornate historical decoration, sci-fi spaceship clutter.
```

## 18 — Greige soft modern

```text
Use case: photorealistic-natural
Asset type: interior design concept rendering, option 18 of 20
Input image: Image 1 is a room and camera-composition reference only.
Primary request: Design a calm, soft-modern shelving system for the same closet, fabricated entirely from warm light-greige PETG. Exactly two L-shaped shelf levels use modular hollow box cassettes with softly radiused front edges, broad shallow printed ribs underneath, and simple fluted PETG pier supports that visibly carry each module to concealed wall mounting blocks. Include discreet rounded cable pegs on selected middle piers.
Scene/backdrop: preserve the compact white closet, gray tile, two door openings, ceiling light, corner viewpoint, long run and short return.
Style/medium: photorealistic Scandinavian-influenced architectural visualization, clean and domestic rather than industrial.
Composition/framing: exactly two shelf levels, clear L shape on both walls, evenly repeated support rhythm, open uncluttered walls.
Lighting/mood: bright soft warm-neutral light, gentle shadows, welcoming and understated.
Materials/textures: one consistent light-greige PETG material, satin matte with very subtle print layer lines; white drywall and gray tile.
Constraints: the complete shelf system is 100 percent PETG, including decks, cassettes, ribs, fascia, corbels, supports, and pegs; structure must look credible and supported rather than floating; simple enough to live with.
Avoid: wood or wood grain, plywood, metal of any kind, metallic colors, mixed materials, exposed steel brackets, people, belongings, bins, rails, labels, text, logos, watermark, extra shelf levels, excessive arches, carved ornament, implausible thin slabs.
```

## 19 — Black-and-white modular

```text
Use case: photorealistic-natural
Asset type: interior design concept rendering, option 19 of 20
Input image: Image 1 is a room and camera-composition reference only.
Primary request: Reimagine the closet with an all-PETG two-color modular shelf system that feels graphic, modern, and easy to print. Exactly two L-shaped levels have smooth white PETG top cassette shells and matte black PETG exposed X-braced underside frames, black vertical mounting spines, and black diagonal printed corbels. White snap-on fascia caps create a clean horizontal line. All parts, both colors, are PETG—no wood or metal. Small black cable pegs are integrated into selected vertical spines.
Scene/backdrop: same compact clean white closet, gray tile, two door openings, ceiling light, corner perspective, long wall and short return.
Style/medium: high-end photorealistic architectural visualization, modern modular product design, honest 3D-print construction.
Composition/framing: exactly two shelf levels; strong repeated bay rhythm; the X-bracing is visible under each shelf but not visually busy.
Lighting/mood: bright neutral soft light, crisp shadows, clean and useful.
Materials/textures: satin white PETG and matte black PETG with subtle layer texture, white drywall, gray tile.
Constraints: 100 percent PETG shelf system; the printed black support skeleton clearly carries the white cassette shells; practical and structurally credible; no hidden mixed-material boards or brackets.
Avoid: wood, plywood, wood grain, metal, steel, brass, chrome, exposed metal fasteners, floating shelves, people, belongings, storage bins, clothes, rails, text, labels, logos, watermark, extra levels, ornate arches, columns that touch the floor, toy-like colors.
```

## 20 — Black balanced arch

```text
Use case: photorealistic-natural
Asset type: interior design concept rendering, option 20 of 20, strongest balanced concept
Input image: Image 1 is a room and camera-composition reference only.
Primary request: Create the best balanced all-PETG redesign: simple enough to build and clean enough to live with, but with a little architectural character. Exactly two black PETG L-shaped shelf levels use smooth thick cassette decks, deep hidden box ribs, and broad structural printed corbels. Each corbel gets one shallow snap-on PETG arch cover with a large calm radius—no full arcade and no ornate carving. Short vertical PETG mounting piers visually anchor the supports; selected non-corner piers have one sturdy rounded cable peg.
Scene/backdrop: preserve the same small white closet, gray tile, two door openings, ceiling light, corner viewpoint, long wall and short return.
Style/medium: premium photorealistic architectural visualization, restrained contemporary architecture, honest additive-manufactured construction.
Composition/framing: exactly two L-shaped shelf levels; clear six-bay long-run rhythm and three-bay return rhythm as perspective allows; broad open wall areas; repeatable modular parts.
Lighting/mood: warm neutral ceiling light, subtle highlights on matte black surfaces, strong but not gloomy.
Materials/textures: entirely matte/satin black PETG with subtle fine layer texture; white drywall and gray tile.
Constraints: shelving and every support, rib, corbel, cover, pier, fascia, and peg are 100 percent PETG; no mixed-material core; load path appears substantial and credible; character comes from restrained arch covers only.
Avoid: wood, plywood, wood grain, steel, brass, bronze, metal brackets, exposed metallic fasteners, people, belongings, clothes, bins, rails, labels, text, logo, watermark, extra shelf levels, floor-to-ceiling columns, cathedral ornament, thin floating shelves, visual clutter.
```
