rupret007/story-corner-shelf/development/r7/assets/artist_rendering_all_petg_two_level_cable_pegs_concept_v2.prompt.md

# R7 removable cable-peg proof-of-concept rendering, v2

This image is the geometry-direction proof of concept for the removable R7
cable-hook collar. It is an architectural visualization, not a construction
drawing, working-load claim, or physical qualification result.

Selected asset:
`artist_rendering_all_petg_two_level_cable_pegs_concept_v2.png`

SHA-256:
`2ef8c1e3a72be730a0583b27b52adf0952ef2b0f3ac80e44bc198c905b2b14cb`

Canvas:
`1402 x 1122 px`

## Final targeted edit

> Starting from the first cable-peg concept, remove the peg from each of the
> two columns immediately adjacent to the inside 90-degree corner on both
> shelf levels: the last long-wall column and the first return-wall column.
> Those four corner-adjacent column faces remain clear. On every remaining
> pegged column, show a subtle narrow black PETG collar band around the
> lower-middle trunk so the peg reads as a removable clip-on accessory rather
> than part of the structural corbel. Keep exactly four representative neatly
> coiled cables on non-corner pegs. Preserve all other geometry, framing,
> lighting, materials, shelf levels, 6 + 3 bay composition, doors, and room
> details. Add no shelves, rails, bins, people, labels, logos, outlets, tools,
> or load claims.

The two corner/run-start positions are intentionally excluded from the
straight-out hook layout because their cross-arm service-swept plan reserve is
only 4.2325 mm. The current R7 concept therefore supports nine normal-facing
collar-hooks per shelf level. A future handed tangential corner hook would need
its own exact Boolean/service qualification.
