rupret007/story-corner-shelf/development/simplified_shelf_concepts/artist_renderings/21_black_compact_bookend_columns_prompt.md

# Option 21 — compact bookend columns

Generated with the built-in image-generation edit workflow from
`16b_structural_arch_peg_rails_petg.png`.

## Prompt

```text
Use case: precise-object-edit
Asset type: photorealistic interior shelf design concept
Input image: edit target. Preserve the exact closet room, camera viewpoint,
white walls, doorway openings, lighting, two black L-shaped shelf levels,
shelf depth, fascia proportions, and black PETG material.

Primary request: make the shelf look like a clean, practical normal modern
shelf instead of an arcade of long hanging columns.

For each shelf level:
- Keep exactly two shortened feature/bookend columns total: one at the extreme
  far-left end of the long wall and one at the extreme far-right end of the
  short return wall near the doorway.
- Each outer feature column drops only about 4.75 to 5 inches below the shelf
  underside, noticeably shorter than the existing long columns, with a softly
  tapered or rounded lower end.
- Put a small integrated two-position cable-peg rail on each of those two outer
  bookend columns only. Keep pegs compact and pointing safely inward.
- Replace all other visible long columns with conventional compact radiused
  shelf corbels tucked close under the shelf, approximately 2.5 to 3.5 inches
  of visible drop.
- At the inside L corner where the two shelf runs meet, show a clean
  uninterrupted junction with no paired long columns, vertical downlegs,
  cable pegs, or bulky visible corner bracket. Any corner support is concealed
  behind the shelf.
- Keep intermediate compact corbels evenly spaced and vertically aligned
  between the two shelf levels, with a quiet normal-shelf rhythm.
- Keep both shelf surfaces empty so the support layout is easy to judge.

Materials and appearance: 100% black standard PETG visible shelf parts,
realistic satin/semi-gloss printed polymer with very subtle layer texture; no
wood, metal shelf components, or decorative gothic arcade.

Constraints: exactly two L-shaped shelf levels; exactly two shortened outer
feature columns per level; no visible corner column pair; no extra shelves,
rails, posts, legs, text, logos, or watermark. Keep the room geometry,
perspective, framing, and lighting unchanged.
```

## Output

- File: `21_black_compact_bookend_columns_petg.png`
- SHA-256: `4a5380e623273ff1aa3345c320e35ecf6b765da399d3ecb2e3ac8db9caa7cee0`
- Size: 1402 x 1122 pixels

This is visual intent only. Hidden corner support, compact-corbels, fastener
layout, PETG creep behavior, and capacity remain CAD and physical-test gates.
