rupret007/story-corner-shelf/development/r11_physical/PHYSICAL_RECORD.md

# R11 physical observation record

> **Append-only evidence record. Current rating: 0 kg / 0 lb.** A source hash
> identifies a repository file; it does not by itself prove the identity,
> dimensions, fit, or capacity of a physical article.

## Evidence boundary

This record distinguishes repository facts from user-reported physical
observations. It records no wall installation, no test load, no stored load,
and no nonzero rating. No drilling or hardware use is authorized.

R11 v1 remains non-printing and non-installing. The frozen R11 Gate A-left v2
overlay applies only to its exact left article and is not changed by this
record. A later right-half job was initiated outside that left-only overlay;
that event does not retroactively authorize the right article, another print,
wall work, or load.

## 2026-08-12 — bay 0 left terminal half-deck

### Repository identity

- Article ID: `r11_bay0_left_terminal_integrated_half_deck`
- Neutral model-only 3MF:
  `development/r11/generated/first_outer_actual_bay_qualification_v1/individual_model_only_3mf/MODEL_ONLY_r11_bay0_left_terminal_integrated_half_deck.3mf`
- Neutral 3MF SHA-256:
  `ff6793255147413b9845dbc771a5b2e5581c1dcbbdcfe5e39b2a7cdb8e6bcbfc`
- Canonical geometry SHA-256:
  `5fe65ebfda9f1d3df77f3db99485983b6313e829a202b536b89b15d2eaea12d1`
- Generated saved-mesh extents:
  `162.175003 × 152.399994 × 32.000000 mm`

These values come from the checked-in R11 manifest and release evidence. The
extents describe the generated saved mesh, not a new measurement of the
physical print.

### User-reported observations

- Print reported finished.
- Article reported cooled and removed from the plate.
- Article reported to lie flat without rocking.
- No visible flex was reported at the fingers during the gentle hand check.
- No sanding was performed.
- Source photo set IDs: `925CA0D3-6200-496B-A109-CA4D2610463B`, images 1–8.
- Additional flat-table photo set ID:
  `83787EA1-DE26-4497-BB8C-7FC25D665434`, image 1.

### Not established

No physical dimensions were recorded. No right mate was present in this
observation. Three-lap engagement, shoulder seating, assembly force, reverse
motion, 1/5/10-cycle behavior, wear, support capture, keystone fit, structural
load, wall connection, and complete Gate pass are **not established**.

Disposition: **LEFT ARTICLE OBSERVED; ONE-BAY FIT PENDING.**

## 2026-08-12 — bay 0 right terminal half-deck

### Repository identity

- Article ID: `r11_bay0_right_terminal_integrated_half_deck`
- Neutral model-only 3MF:
  `development/r11/generated/first_outer_actual_bay_qualification_v1/individual_model_only_3mf/MODEL_ONLY_r11_bay0_right_terminal_integrated_half_deck.3mf`
- Neutral 3MF SHA-256:
  `354dfb1e3ef4ca88aff30333d3154f7f3de1618f90f3e00a37d1aa5c49b30598`
- Canonical geometry SHA-256:
  `b714da3ad19d553b74389d9ffb1abbc9903a34662f3fba3f2b79397d13e6ceea`
- Generated saved-mesh extents:
  `162.175003 × 152.399994 × 32.000000 mm`

These values identify the checked-in neutral source model. They do not verify
the later sliced job or its physical result.

### Latest known physical status

- **PRINT IN PROGRESS / OUTCOME NOT RECORDED.**
- Completion, cooling, removal, flatness, visual condition, and fit have not
  been reported in this record.
- The job occurred outside the frozen left-only R11 v2 control overlay. It
  creates no retroactive authorization and changes none of the v1/v2 flags.

Disposition: **WAIT FOR COMPLETION, COOLING, REMOVAL, AND INSPECTION.**

## One-bay qualification state

- Left/right dry fit: not recorded.
- Cycle 1: not recorded.
- Cycle 5: not recorded.
- Cycle 10: not recorded.
- Supports: not part of the current physical check.
- Keystone: not part of the current physical check.
- Wall or hardware: not part of the current physical check.
- Load: none; **0 kg / 0 lb rating remains controlling**.

Follow the beginner sequence in [README.md](README.md) only after the right
article has completed, cooled, been removed, and passed its visual check.
