rupret007/story-corner-shelf/development/r9/physical_records/STAGE0_2026-08-10.md

# Stage 0 physical record — 2026-08-10

This is an append-only observation record for the fail-fast R9 workflow. It
does not change the immutable `qualification_v5` package and does not authorize
wall work, load, or a later print.

## Controlled identities

- Package: `r9_compact_bookend_petg_qualification_v5`
- Manifest SHA-256:
  `655164cdd2cc6e64038f600d74e6f629648a7270fa20140d563010310056fdfe`
- Receiver:
  `MODEL_ONLY_r8_clearance_ladder_receiver.3mf`
- Corrected key:
  `MODEL_ONLY_r9_gate0_clearance_key_0p4_handle_down.3mf`
- Corrected-key geometry digest:
  `0df9dca3fd5090684238e8dfff4d5c29a0be84f3b4a88f0aecb06b59c8cfb4a0`
- Printer: Bambu Lab A1 mini, 0.4 mm nozzle, Textured PEI plate
- Studio: Bambu Studio 02.07.01.62
- Material preset: `SUNLU PETG @BBL A1M 0.4 nozzle`
- Process preset: `0.20mm Strength @BBL A1M`
- Physical filament: SUNLU standard black PETG, ASIN B0D1KC72YP
- Spool lot: **not yet recorded**
- Dry-cycle record: **not yet recorded**

## Receiver job

- Status: printed, cooled, removed, photographed
- Sliced estimate / trace: 44 layers, 1:04:50, 26.73 g
- Observed startup: bed leveling and dynamic-flow calibration ran
- Observed first layer: 250 C nozzle, 60 C bed, black PETG attached
- Front-face photo IDs:
  - `07B11519-95B6-470A-B405-937651BCDAC6/1-Photo-1.jpg`
  - `07B11519-95B6-470A-B405-937651BCDAC6/2-Photo-2.jpg`
- Photo-visible condition: no obvious crack, layer split, missing socket,
  burn, or major lifted edge; cosmetic top-surface ridging is visible.
- Required physical observations still pending:
  - [x] operator reports broad rear datum face looks good with no detected
        rocking on a hard flat table;
  - [x] operator reports the third socket from the left (0.4 mm/face) is clear
        through its full
        entry, neck, seat, rear lip, and depth, with no loose strand, curl,
        bead, or burr intruding into the service path;
  - [ ] spool lot recorded;
  - [ ] received-spool/dry-cycle record completed or explicitly recorded as
        not dried.
- Operator release statement: “everything looks good as far as I can tell,
  plate is clear.”
- Current receiver disposition: **RELEASED FOR THE CORRECTED 0.4 KEY TEST**

## Corrected 0.4 key job

- Status: exact v5 file prepared and sliced; **not sent to the printer**
- Saved orientation: handle/base down; imported at identity; scale 100%
- Slicer controls verified from generated G-code:
  - SUNLU PETG, 250 C first layer / 245 C later;
  - Textured PEI bed 60 C;
  - flow ratio 0.94, maximum volumetric speed 9 mm3/s;
  - 0.20 mm Strength, six walls, five top / three bottom shells,
    25% grid infill;
  - Support Off;
  - Outer brim only, 5.0 mm width, 0.1 mm object gap.
- Preview: one object, one brim, 46 layers, 17:03 total estimate, 1.70 g;
  no floating-cantilever warning shown.
- Layer 29 / Z=5.8 mm: slicer explicitly classifies the two keyed-head wings as
  overhang walls and bridges with overhang fan enabled. This is a physical
  first-article screen, not a zero-overhang claim.
- Print authorization: **GRANTED FOR THIS EXACT JOB** by the operator on
  2026-08-10.
- Send-dialog verification: one 1.70 g key; external spool mapped PETG; Bed
  Leveling On; Flow Dynamics Calibration On; Timelapse Off.
- Live execution evidence:
  - exact job accepted as `R9_corrected-pose_0.4_mm-per-face_clearance_key`;
  - vibration compensation completed;
  - auto bed leveling observed;
  - dynamic-flow calibration observed at 245 C / 60 C;
  - Layer 1 observed printing at 250 C / 60 C with no printer error;
  - Layer 2 observed continuing at 245 C / 60 C with no error, detached brim,
    or visible loose extrusion in the available camera view.
  - critical keyed-head transition passed; Layer 31/46 continued without a
    printer fault or visible loose extrusion;
  - printer reported Finished at Layer 46/46; completed part and brim appeared
    intact in the available camera view;
  - plate remained about 59 C immediately after completion, so physical
    removal and inspection are pending full room-temperature cooling.
- Cooled-key photo IDs:
  - `E5C68B2D-2756-4ACE-880D-A1A063CB6970/1-Photo-1.jpg`
  - `E5C68B2D-2756-4ACE-880D-A1A063CB6970/2-Photo-2.jpg`
  - `E5C68B2D-2756-4ACE-880D-A1A063CB6970/3-Photo-3.jpg`
  - `E5C68B2D-2756-4ACE-880D-A1A063CB6970/4-Photo-4.jpg`
- Cooled-key photo-visible condition: no loose strand, crack, whitening,
  layer separation, curled keyed-head wing, or obvious wing droop; both
  overhang undersides appear continuous and substantially level. Photos are
  slightly soft, so this is a preliminary visual pass rather than dimensional
  proof.
- Current corrected-key disposition: **RELEASED FOR ONE GENTLE INITIAL
  INSERTION/REMOVAL CYCLE; TEN-CYCLE GATE NOT YET PASSED**

## Required next decision

Perform one straight, gentle insertion/seat/release cycle in the receiver's
third socket from the left. Stop immediately on binding, force, rocking,
visible warp, crack, whitening, layer separation, permanent set, or visible
abrasion. If Cycle 1 is clean, continue only after recording its feel and
condition; inspect again after Cycles 5 and 10. Do not sand, file, lubricate, or
force either article.

## Cycle observations

- Cycle 1 seated-state photo:
  `FC4BBB0F-E1FB-45A2-AD91-19BC79D9B09B/1-Photo-1.jpg`
- Operator reports that the design appears to be fitting well.
- Photo-visible seated condition: key appears engaged in the intended third
  station (first station cropped off-frame); receiver face remains visually
  flat with no visible whitening, crack, or deformation around the slot.
- Cycle 1 operator result: fully seated, came right out by hand, no issues
  reported.
- Cycle 1 status: **PASSED — FULL SEAT AND CLEAN HAND RELEASE; NO REPORTED
  BINDING, DAMAGE, OR VISIBLE STRESS**
- Next checkpoint: complete Cycles 2–5 using the identical straight service
  motion, then inspect both parts before continuing.
- Cycle 5 operator checkpoint: fitting well and coming out well; no issue or
  worsening feel reported.
- Cycle 5 status: **PASSED — CONSISTENT SEAT/RELEASE THROUGH FIVE CYCLES**
- Final checkpoint: complete Cycles 6–10, then inspect keyed-head wings, stem,
  receiver entry/neck/seat, and surrounding face for wear or stress.
- Diagnostic observation: operator reports the corrected 0.4 key does not fit
  the receiver's far-left station. This is expected because the authored
  station order is 0.2, 0.3, 0.4, 0.5 mm per face from left to right; the
  corrected key is qualified only in the third, 0.4 station. Do not force it
  into the 0.2 or 0.3 station. Confirm no damage resulted from the diagnostic
  attempt.
- Diagnostic photo:
  `9F7E34A1-5F96-4B7A-BD64-106690955790/1-Photo-1.jpg`
- In the photo's vertical receiver orientation, station order is top-to-bottom
  0.2, 0.3, 0.4, 0.5 mm per face. The key is shown at the top 0.2 station and
  does not reach the seated position, consistent with the intended tighter
  clearance. The qualifying 0.4 station is third from the top / second from
  the bottom.
- Operator confirms no force was used during the tighter-station diagnostic.
  Diagnostic disposition: **EXPECTED REFUSAL; NO FAILURE CREDIT OR DAMAGE
  INDICATED**.

## Final Stage 0 disposition

- Operator confirms ten complete insert/seat/release cycles in the intended
  0.4-mm-per-face station with unchanged feel, clean hand release, and no
  binding, whitening, cracking, deformation, or damage.
- Stage 0 disposition: **PASSED — CORRECTED 0.4 KEY COMPLETED TEN CLEAN
  CYCLES IN THE INTENDED THIRD STATION**.

## Compact-support first-article kickoff

- Exact article: `MODEL_ONLY_r9_compact_support.3mf` from immutable
  `qualification_v5`.
- Audited slice: SUNLU PETG; A1 mini 0.4-mm nozzle; 0.20-mm Strength; six
  walls; 25% grid; five top / three bottom layers; Support Off; Outer brim
  only, 5.0-mm width, 0.1-mm object gap; 160 layers; 145.12 g; 4:53:11 total
  estimate.
- Operator granted explicit authorization for this exact first-article job.
- Initial send canceled during startup before Layer 1 with no visible HMS
  detail in Studio.
- One controlled retry was explicitly authorized. The retry reported
  `Build plate not detected` (`0300-8019 211410`) at Layer 0 and asked for a
  plate/nozzle inspection. The job subsequently resumed and reached Layer 1.
- Live first-layer evidence: PETG external-spool mapping; 250 C nozzle / 60 C
  bed; continuous attached broad-face outline and brim in the available
  camera view; no visible loose extrusion, spaghetti, or lifted edge through
  the initial broad-face paths.
- The retry cleared its large first layer and advanced to Layer 2/160 at
  245 C / 60 C with the broad face and brim still visibly attached and no
  repeat plate-detection warning.
- The plate-detection warning remains part of the physical record and must be
  investigated before any later printer job even if this first article
  completes successfully.
