rupret007/story-corner-shelf/development/r6/assets/artist_rendering_all_petg_two_level.prompt.md

# Exact 6 + 3 two-level all-PETG artist rendering

This concept image was created with the built-in image-generation tool. It is
an architectural intent rendering, not a construction drawing. Generated CAD,
field measurements, and validation reports govern every dimension and part
count.

Selected asset:
`artist_rendering_all_petg_two_level_exact_6_plus_3.png`

SHA-256:
`32ae5491751e5414db30cae0f2eb425fe8382aed29b47660c48e7dcf83c05de7`

## Final edit prompt

> Correct the two-level black PETG Roman shelf rendering while preserving the
> closet, camera, walls, lighting, black material, rich Palatine detailing,
> and two-level composition. There must be exactly two usable horizontal shelf
> decks total—one deck at the top of each Roman arcade/entablature assembly.
> The Roman arches and piers hang below their own shelf deck as wall-supported
> tied frames. Remove every continuous horizontal ledge, rail, or shelf that
> connects the bottoms of the columns. Column/pier feet terminate individually
> at wall-mounted X-braced corbel nodes; they do not rest on another shelf and
> do not connect vertically to the other level. Per level, the intended design
> has three arch bays on the short return and six on the long through arm.
> Reveal subtle broad 3:4:5 X-braced PETG corbel geometry at pier boundaries.
> Each top deck is a substantial closed coffered black PETG cassette about six
> inches deep and 30 mm thick. Keep the through-owned inside corner, modular
> shadow seams, and accessible printed key/pin details. No plywood, steel shelf
> body, conventional metal brackets, freestanding legs, inter-level structural
> ties, people, bins, text, logos, watermark, or load claims.

Two correction passes explicitly restored six visible long-run openings and
three visible return openings on both levels. The image is still visual intent
only; the generated elevation and plan drawings govern exact counts, stations,
clearances, and assembly geometry.
