rupret007/story-corner-shelf/development/r7/assets/artist_rendering_all_petg_two_level_cable_pegs_concept_v1.prompt.md

# R7 cable-peg proof-of-concept rendering

This concept image was created with the built-in image-generation tool as a
design-direction edit of the exact R6 two-level 6 + 3 rendering. It is not a
construction drawing, a load claim, or evidence that the cable-peg accessory
has passed physical qualification. Generated CAD and qualification records
govern the printable geometry.

Selected asset:
`artist_rendering_all_petg_two_level_cable_pegs_concept_v1.png`

SHA-256:
`b34e56ea5baee37e3f0dd5072b229e2e02e475b2736b0a502c33e25e321de140`

Canvas:
`1402 x 1122 px`

## Edit prompt

> Add functional wire-management pegs to the removable vertical black
> column/pier faces so the wall space can store neatly coiled cables and
> lightweight cords. Each visible column gets one compact, rounded,
> upward-retaining black PETG peg on the lower-middle portion of its front
> face. The peg should look like a deliberately printed replaceable accessory
> integrated with the ornamental column overlay, with a short horizontal stem
> and subtly raised rounded tip. Show only three or four representative neatly
> coiled lightweight black/gray cables hanging from selected pegs; leave the
> remaining pegs empty. Change only the column faces by adding these pegs and
> the example cable loops. Preserve the closet, camera, walls, lighting, two
> shelf decks, six-long-plus-three-return bay composition on both levels,
> arches, columns, corbels, joinery details, black PETG material, door
> openings, floor, and all proportions. Do not add shelves, bottom rails,
> bins, people, labels, text, logos, outlets, tools, or structural load claims.
> Cords must not touch the floor or obscure joinery. No watermark.

The printable design direction is a separate, removable R7 cable hook/collar,
not an integral change to the frozen R6 structural corbel. It must be removed
before facade or cross-key service. Until physical PETG hook/collar tests pass,
the image communicates visual and storage intent only.
