rupret007/story-corner-shelf/development/r6/assets/artist_rendering_all_petg_two_level.png

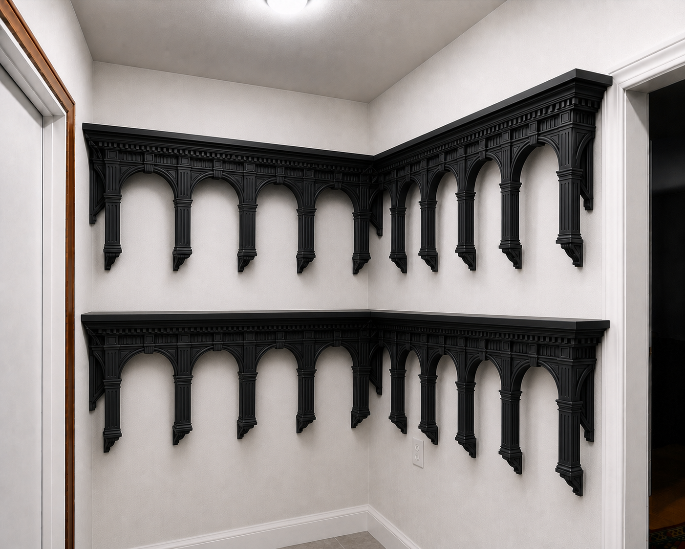
development/r6/assets/artist_rendering_all_petg_two_level.png
