rupret007/story-corner-shelf/development/simplified_shelf_concepts/artist_renderings/01_black_minimal_ribbed_petg.png

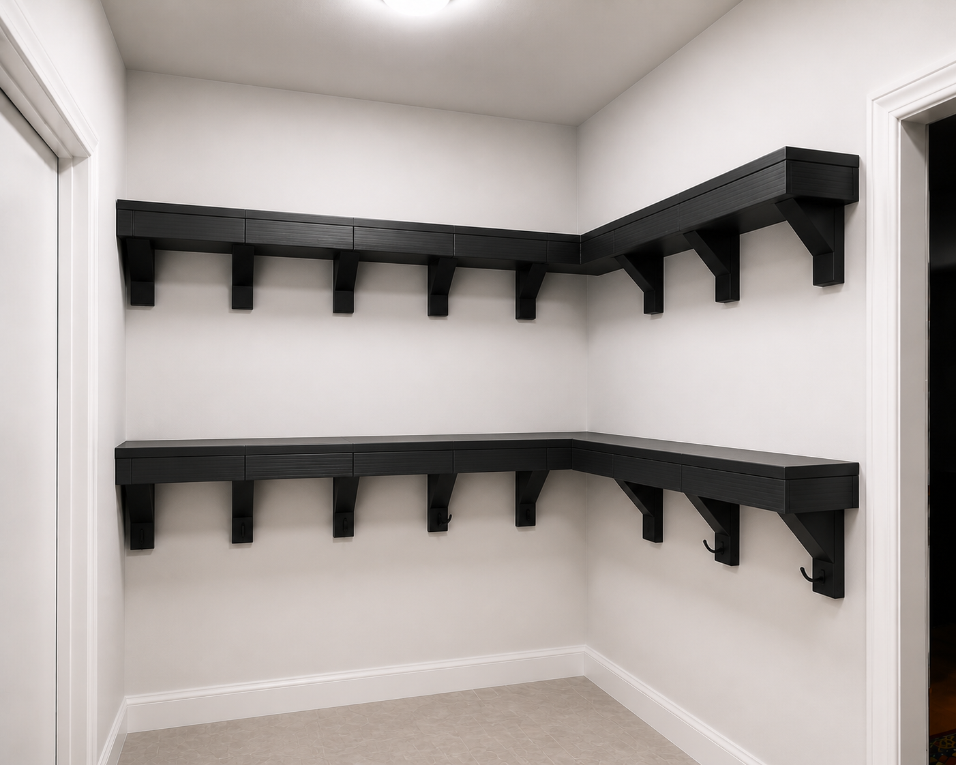
development/simplified_shelf_concepts/artist_renderings/01_black_minimal_ribbed_petg.png
