rupret007/story-corner-shelf/development/simplified_shelf_concepts/artist_renderings/04_ivory_midcentury_petg.png

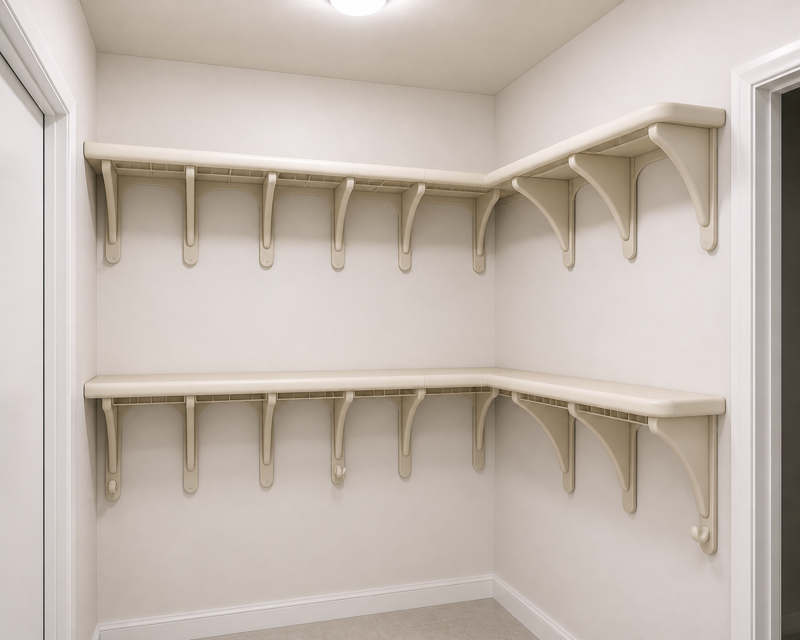
development/simplified_shelf_concepts/artist_renderings/04_ivory_midcentury_petg.png
