rupret007/story-corner-shelf/development/simplified_shelf_concepts/artist_renderings/05_graphite_hex_rib_petg.png

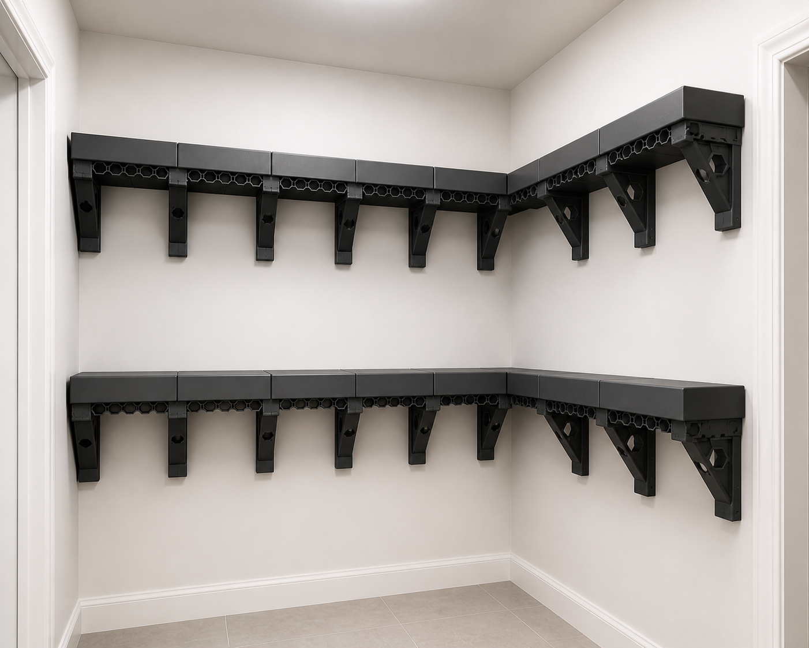
development/simplified_shelf_concepts/artist_renderings/05_graphite_hex_rib_petg.png
