rupret007/story-corner-shelf/development/simplified_shelf_concepts/artist_renderings/06_bone_white_organic_petg.png

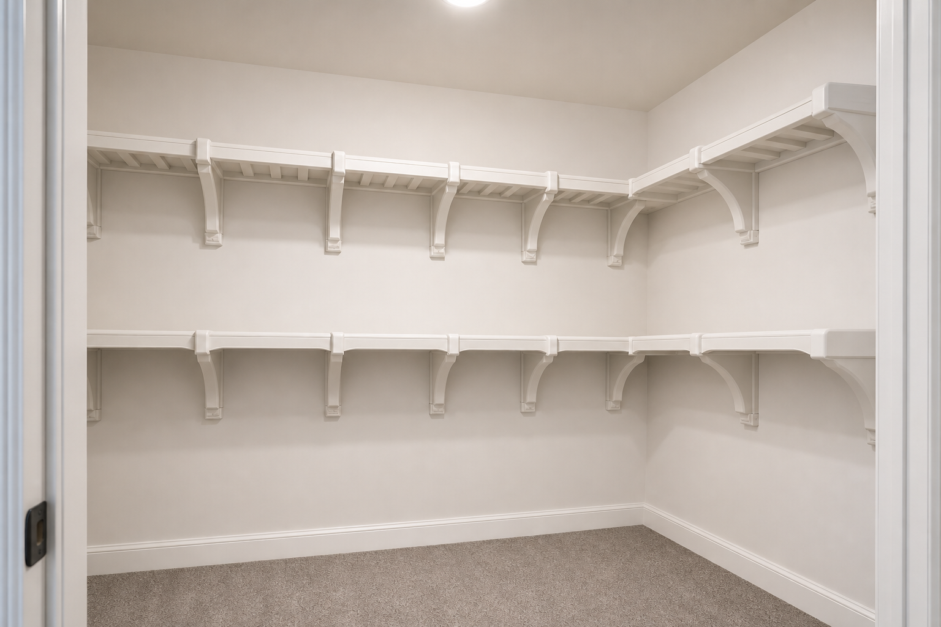
development/simplified_shelf_concepts/artist_renderings/06_bone_white_organic_petg.png
