rupret007/story-corner-shelf/development/simplified_shelf_concepts/artist_renderings/08_black_ivory_modular_grid_petg.png

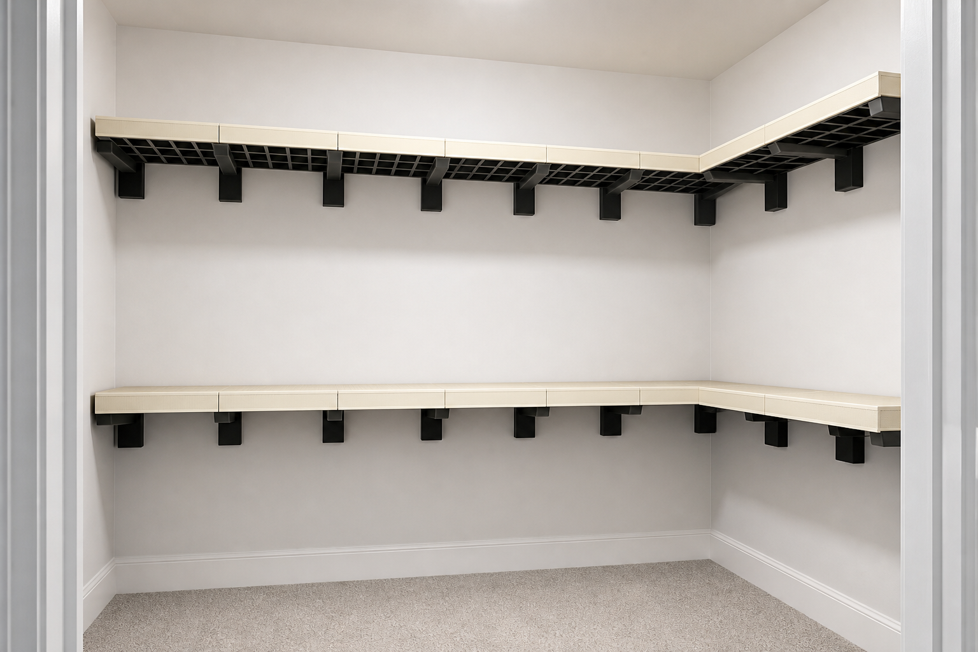
development/simplified_shelf_concepts/artist_renderings/08_black_ivory_modular_grid_petg.png
