rupret007/story-corner-shelf/development/simplified_shelf_concepts/artist_renderings/09_black_retro_futurist_petg.png

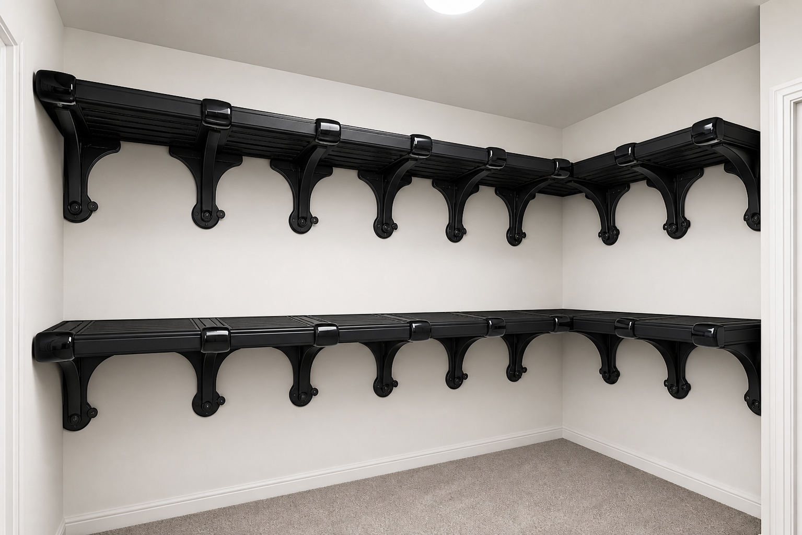
development/simplified_shelf_concepts/artist_renderings/09_black_retro_futurist_petg.png
