rupret007/story-corner-shelf/development/simplified_shelf_concepts/artist_renderings/10_forest_green_parametric_petg.png

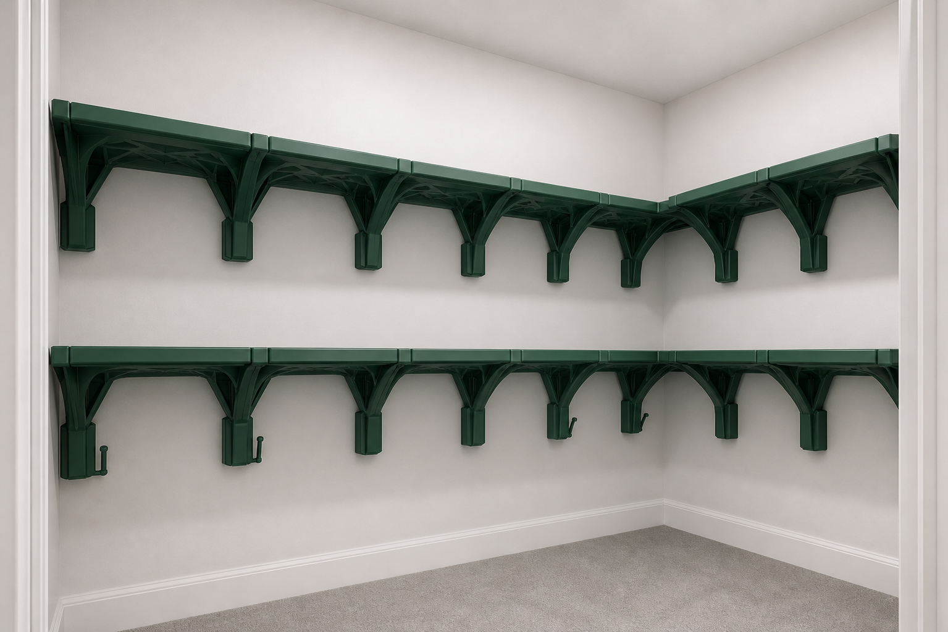
development/simplified_shelf_concepts/artist_renderings/10_forest_green_parametric_petg.png
