rupret007/story-corner-shelf/development/simplified_shelf_concepts/artist_renderings/12_cream_contemporary_scalloped_petg.png

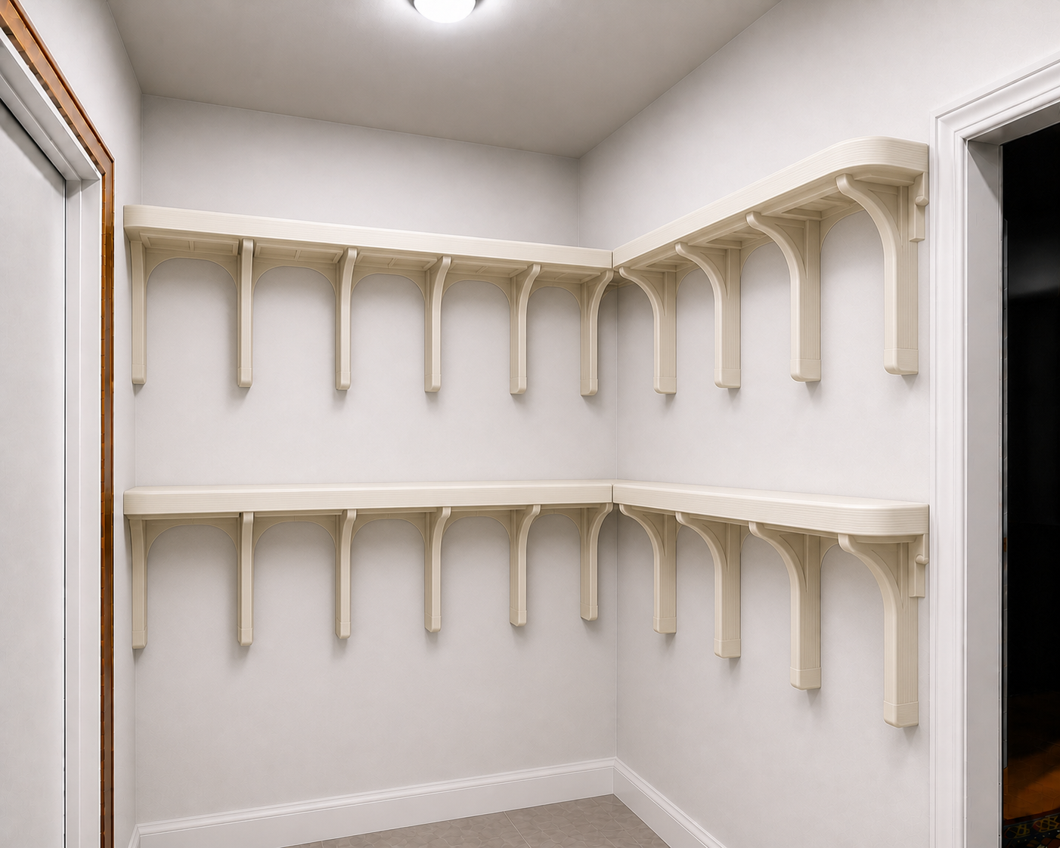
development/simplified_shelf_concepts/artist_renderings/12_cream_contemporary_scalloped_petg.png
