rupret007/story-corner-shelf/development/simplified_shelf_concepts/artist_renderings/13_graphite_brutalist_petg.png

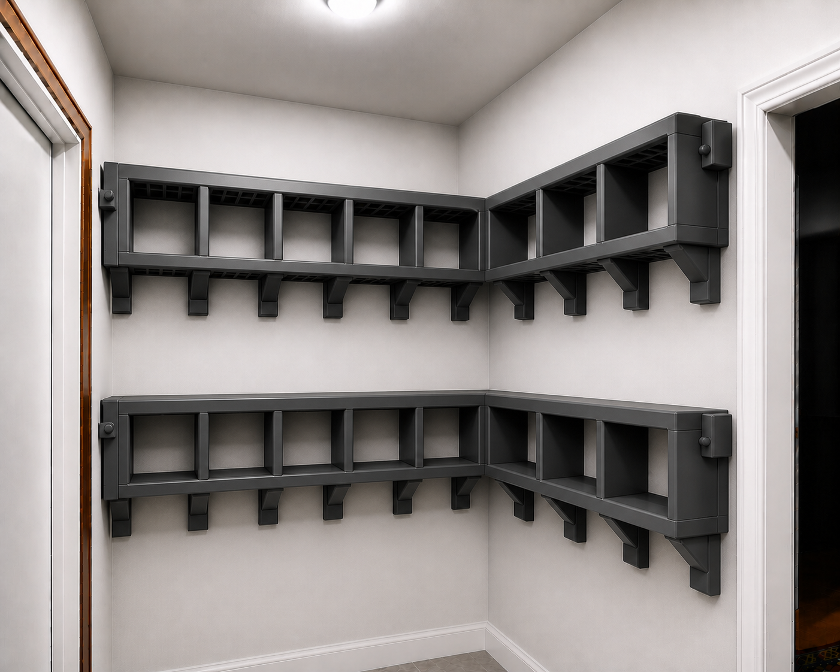
development/simplified_shelf_concepts/artist_renderings/13_graphite_brutalist_petg.png
