rupret007/story-corner-shelf/development/simplified_shelf_concepts/artist_renderings/17_smoke_honeycomb_petg.png

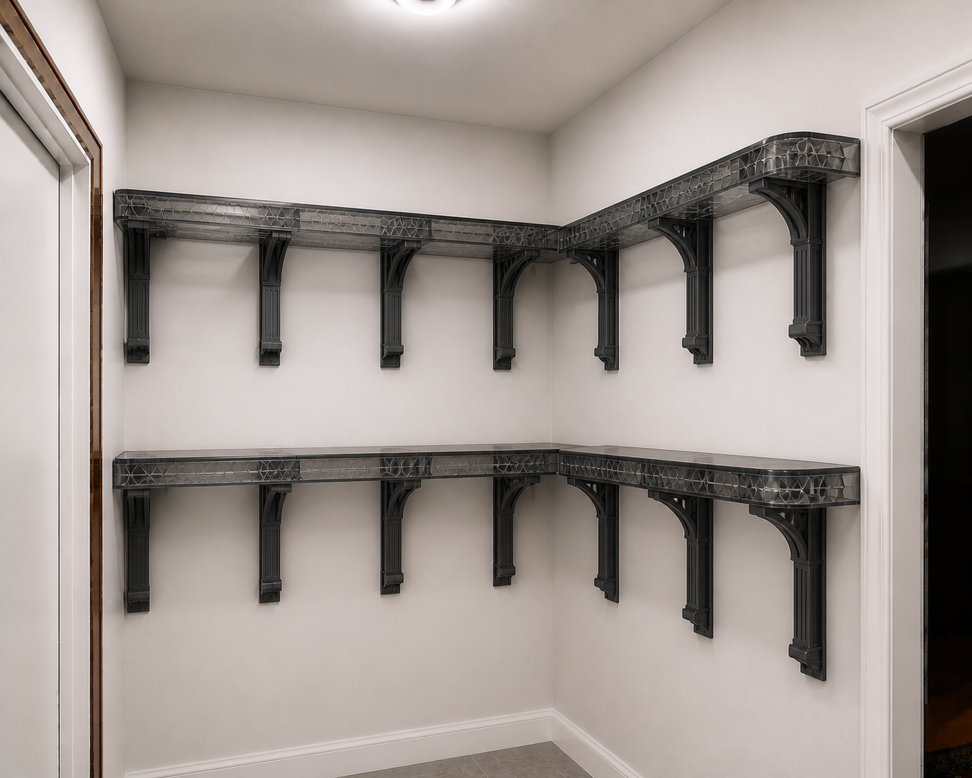
development/simplified_shelf_concepts/artist_renderings/17_smoke_honeycomb_petg.png
