rupret007/story-corner-shelf/development/simplified_shelf_concepts/artist_renderings/18_greige_soft_modern_petg.png

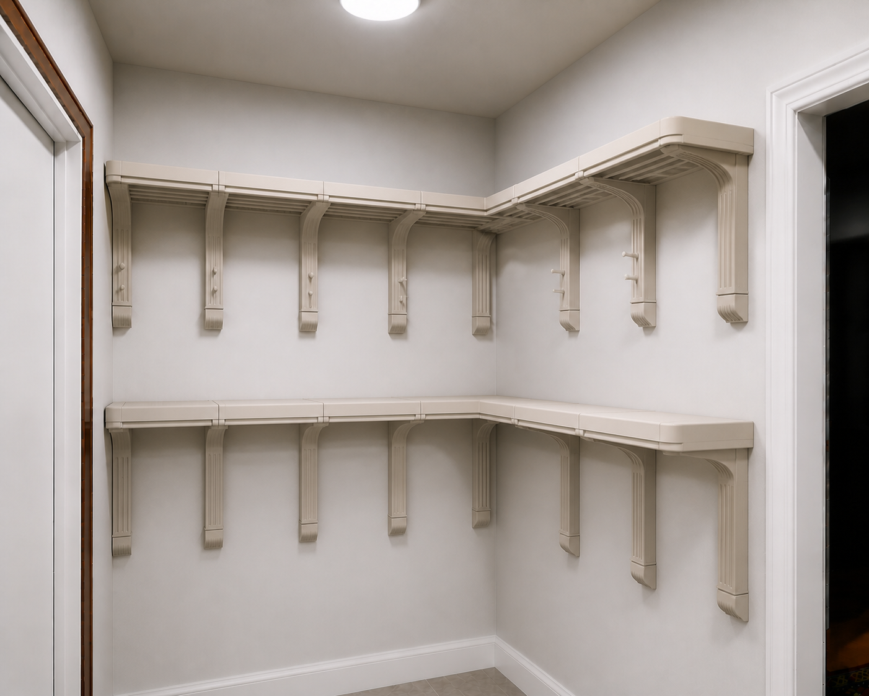
development/simplified_shelf_concepts/artist_renderings/18_greige_soft_modern_petg.png
