rupret007/story-corner-shelf/development/simplified_shelf_concepts/artist_renderings/19_black_white_modular_petg.png

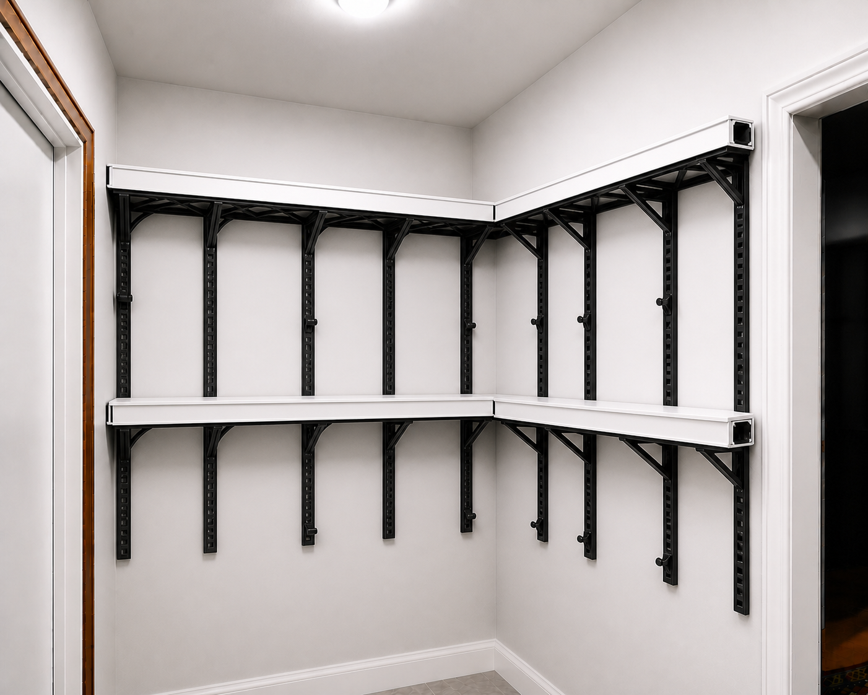
development/simplified_shelf_concepts/artist_renderings/19_black_white_modular_petg.png
