rupret007/story-corner-shelf/development/simplified_shelf_concepts/artist_renderings/20_black_balanced_arch_petg.png

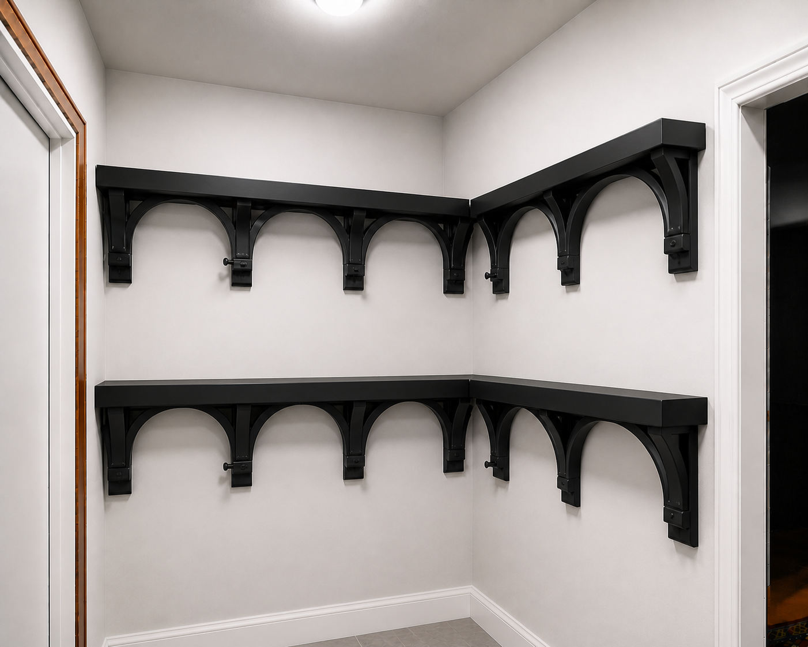
development/simplified_shelf_concepts/artist_renderings/20_black_balanced_arch_petg.png
