rupret007/story-corner-shelf/development/r8/generated/one_bay_qualification_v2/individual_model_only_3mf/MODEL_ONLY_r8_one_bay_mounted_rail.3mf

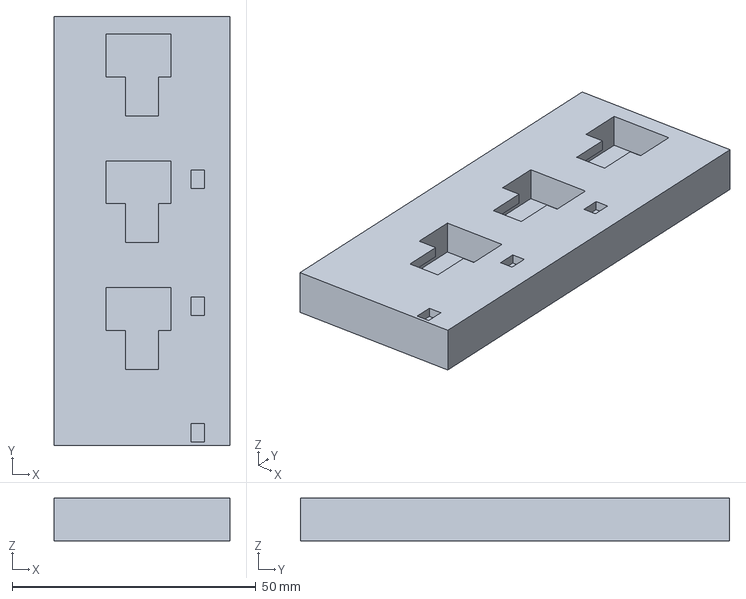
[picture p46: CAD file, 2026-08-11]
development/r8/generated/one_bay_qualification_v2/individual_model_only_3mf/MODEL_ONLY_r8_one_bay_mounted_rail.3mf
36.0 x 88.0 x 8.80 mm
