rupret007/story-corner-shelf/development/r8/generated/one_bay_qualification_v2/model_only_3mf/MODEL_ONLY_R8_ONE_BAY_QUALIFICATION_CATALOG.3mf

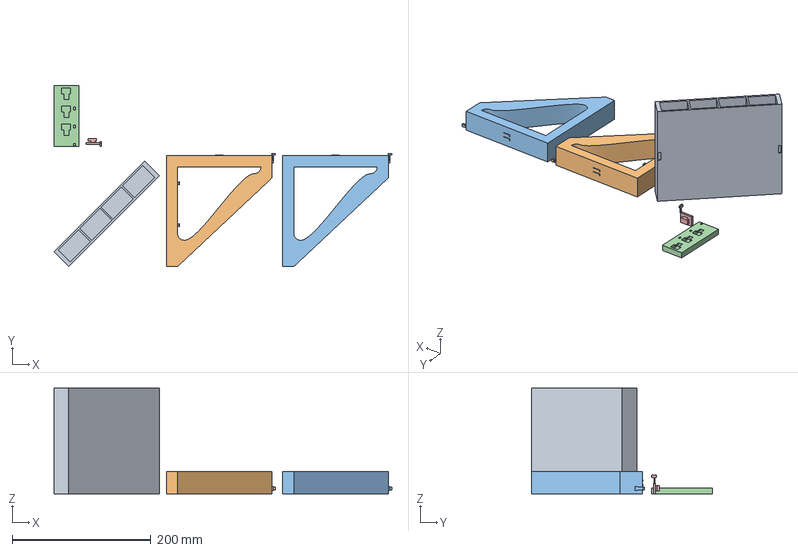
[picture p47: CAD file, 2026-08-11]
development/r8/generated/one_bay_qualification_v2/model_only_3mf/MODEL_ONLY_R8_ONE_BAY_QUALIFICATION_CATALOG.3mf
487.2 x 261.4 x 152.4 mm
r8_one_bay_registered_cassette
r8_one_bay_left_rail_ready_locator_d_frame
r8_one_bay_right_smooth_locator_seated_keeper_d_frame
r8_one_bay_mounted_rail
r8_one_bay_retained_blank
