rupret007/story-corner-shelf/development/r8/generated/one_bay_qualification_v2/stl/r8_one_bay_registered_cassette.stl

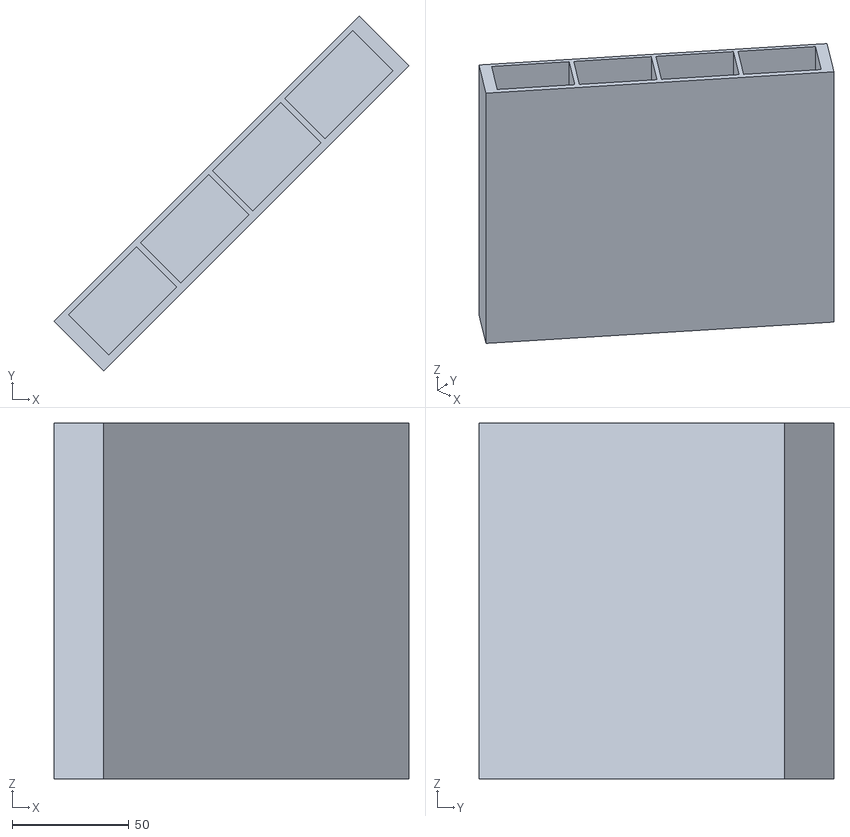
[picture p48: CAD file, 2026-08-11]
development/r8/generated/one_bay_qualification_v2/stl/r8_one_bay_registered_cassette.stl
152.0 x 152.0 x 152.4
