rupret007/story-corner-shelf/development/r8/generated/qualification_v2/individual_model_only_3mf/MODEL_ONLY_r8_clearance_key_0p2.3mf

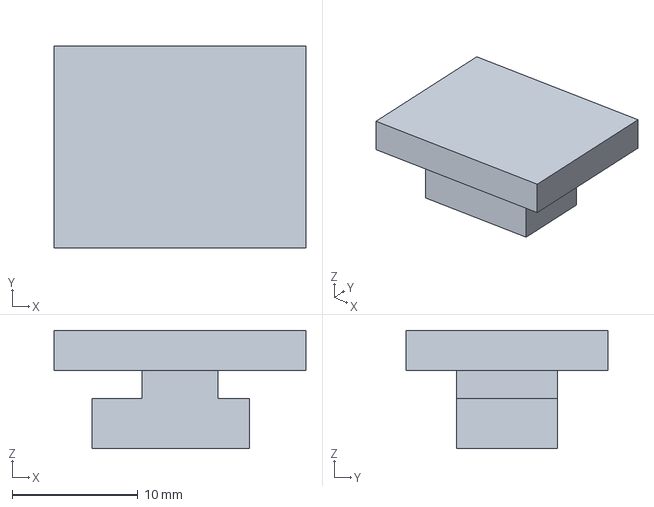
[picture p49: CAD file, 2026-08-11]
development/r8/generated/qualification_v2/individual_model_only_3mf/MODEL_ONLY_r8_clearance_key_0p2.3mf
20.0 x 16.0 x 9.40 mm
