rupret007/story-corner-shelf/development/r8/generated/qualification_v2/model_only_3mf/MODEL_ONLY_R8_QUALIFICATION_ALL_PARTS.3mf

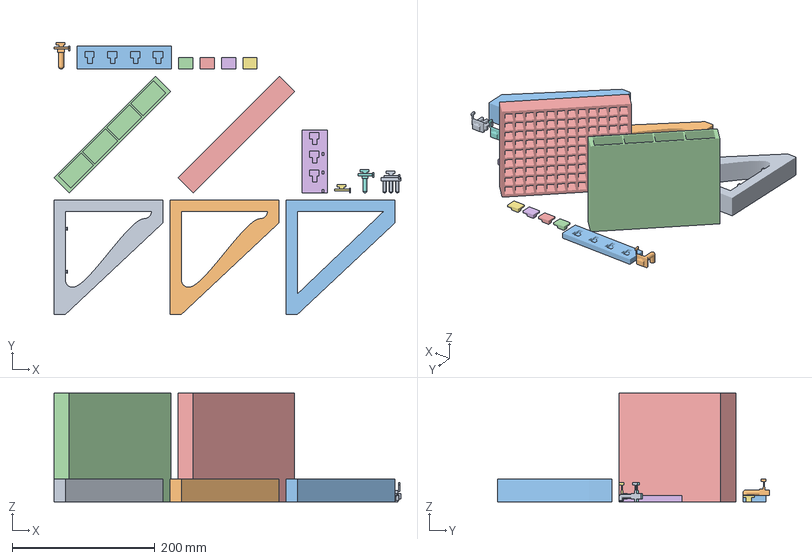
[picture p50: CAD file, 2026-08-11]
development/r8/generated/qualification_v2/model_only_3mf/MODEL_ONLY_R8_QUALIFICATION_ALL_PARTS.3mf
485.7 x 380.4 x 152.4 mm
r8_curved_eligible_d_frame_mount
r8_smooth_curved_core
r8_equal_volume_straight_control
r8_selected_front_first_u_box_cassette
r8_matched_heavy_coffer_control
r8_mounted_retention_rail
r8_retained_blank
r8_retained_single_peg
r8_retained_three_cable_comb
r8_retained_shortened_coil_j_hook
r8_clearance_ladder_receiver
r8_clearance_key_0p2
r8_clearance_key_0p3
r8_clearance_key_0p4
r8_clearance_key_0p5
