rupret007/story-corner-shelf/development/r8/generated/qualification_v2/stl/r8_selected_front_first_u_box_cassette.stl

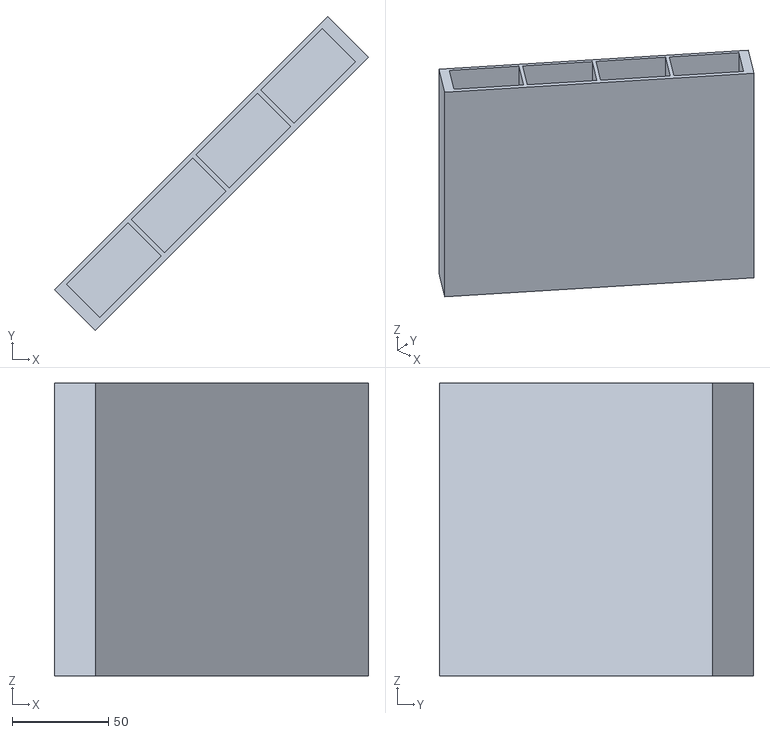
[picture p51: CAD file, 2026-08-11]
development/r8/generated/qualification_v2/stl/r8_selected_front_first_u_box_cassette.stl
163.4 x 163.4 x 152.4
