rupret007/story-corner-shelf/development/r9/generated/one_bay_prototype_v3/individual_model_only_3mf/MODEL_ONLY_r9_one_bay_rear_ledger.3mf

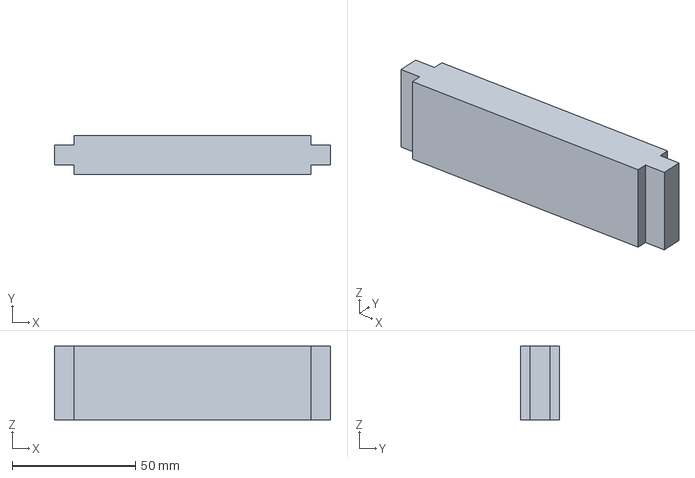
[picture p52: CAD file, 2026-08-11]
development/r9/generated/one_bay_prototype_v3/individual_model_only_3mf/MODEL_ONLY_r9_one_bay_rear_ledger.3mf
112.0 x 16.0 x 30.0 mm
