rupret007/story-corner-shelf/development/r9/generated/one_bay_prototype_v3/model_only_3mf/R9_ONE_BAY_PRINTABLE_PARTS_CATALOG_NOT_A_PLATE.3mf

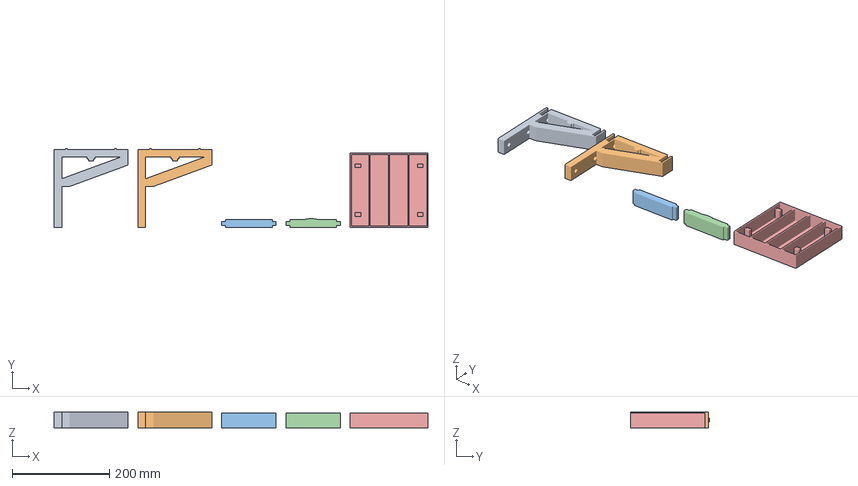
[picture p53: CAD file, 2026-08-11]
development/r9/generated/one_bay_prototype_v3/model_only_3mf/R9_ONE_BAY_PRINTABLE_PARTS_CATALOG_NOT_A_PLATE.3mf
768.8 x 161.4 x 32.0 mm
r9_one_bay_left_compact_support
r9_one_bay_right_compact_support
r9_one_bay_rear_ledger
r9_one_bay_front_beam
r9_one_bay_shelf_cassette
