rupret007/story-corner-shelf/development/r9/generated/one_bay_prototype_v3/stl/r9_one_bay_right_compact_support.stl

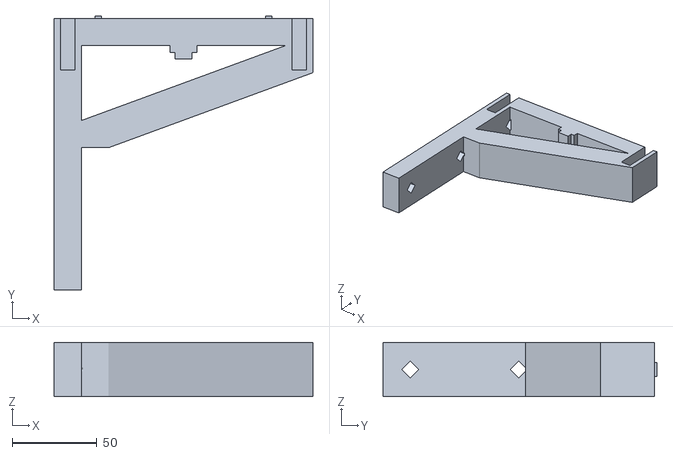
[picture p54: CAD file, 2026-08-11]
development/r9/generated/one_bay_prototype_v3/stl/r9_one_bay_right_compact_support.stl
152.4 x 161.4 x 32.0
