rupret007/story-corner-shelf/development/r9/generated/qualification_v5/individual_model_only_3mf/MODEL_ONLY_r9_rear_ledger_male_coupon.3mf

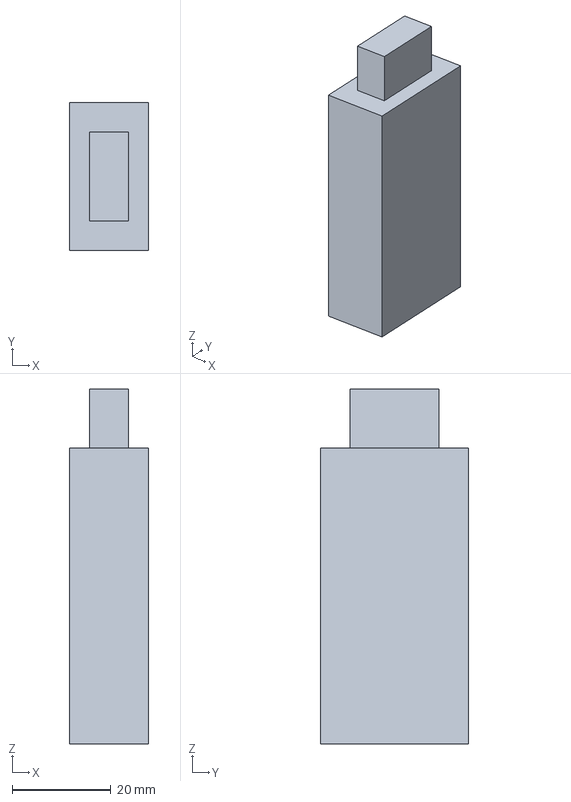
[picture p55: CAD file, 2026-08-11]
development/r9/generated/qualification_v5/individual_model_only_3mf/MODEL_ONLY_r9_rear_ledger_male_coupon.3mf
16.0 x 30.0 x 72.0 mm
