rupret007/story-corner-shelf/development/r9/generated/qualification_v5/model_only_3mf/MODEL_ONLY_R9_QUALIFICATION_CATALOG.3mf

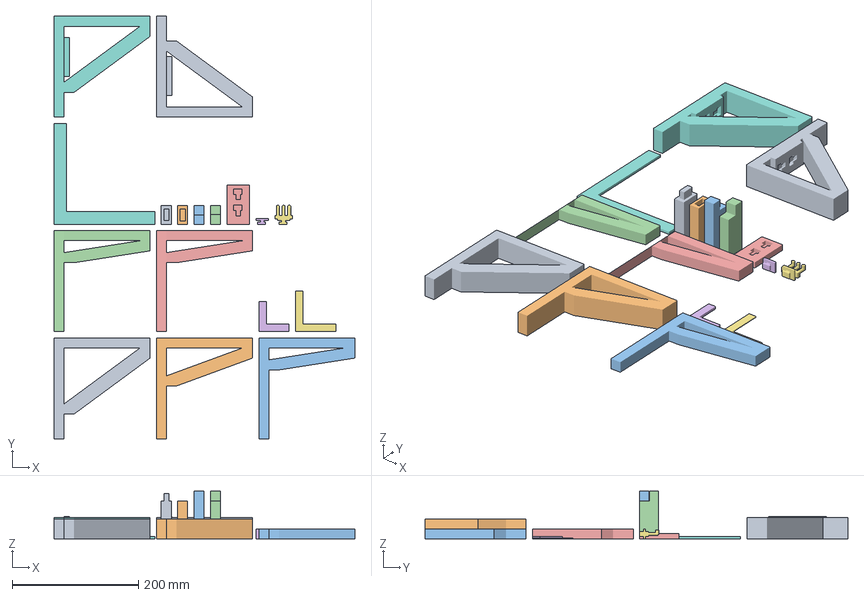
[picture p56: CAD file, 2026-08-11]
development/r9/generated/qualification_v5/model_only_3mf/MODEL_ONLY_R9_QUALIFICATION_CATALOG.3mf
477.2 x 670.0 x 76.0 mm
r9_shortened_outer_bookend_support
r9_compact_support
r9_concealed_corner_half_control
r9_through_hidden_corner_half
r9_return_hidden_corner_half
r9_under_shelf_shear_key_coupon
r9_cosmetic_corner_cover_coupon
r9_90_degree_tabletop_angle_fixture
r9_rear_ledger_male_coupon
r9_rear_ledger_female_coupon
r9_front_beam_lower_lap_coupon
r9_front_beam_upper_lap_coupon
r9_two_socket_outer_bookend_rail_fit_coupon
r9_flush_blank_cable_module
r9_multi_cable_comb_hook_module
r9_through_outer_bookend_additive_two_socket_candidate
r9_return_outer_bookend_additive_two_socket_candidate
