rupret007/story-corner-shelf/development/r9/generated/qualification_v5/stage0_individual_model_only_3mf/MODEL_ONLY_r8_clearance_ladder_receiver.3mf

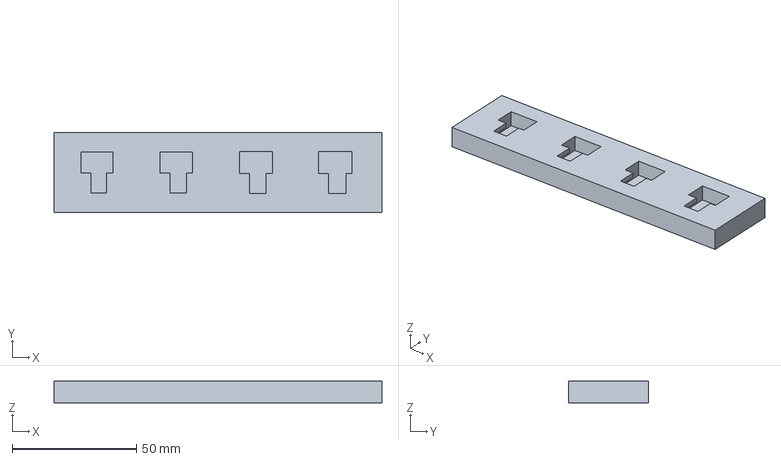
[picture p57: CAD file, 2026-08-11]
development/r9/generated/qualification_v5/stage0_individual_model_only_3mf/MODEL_ONLY_r8_clearance_ladder_receiver.3mf
132.0 x 32.0 x 8.80 mm
