rupret007/story-corner-shelf/development/r9/generated/qualification_v5/stl/r9_front_beam_lower_lap_coupon.stl

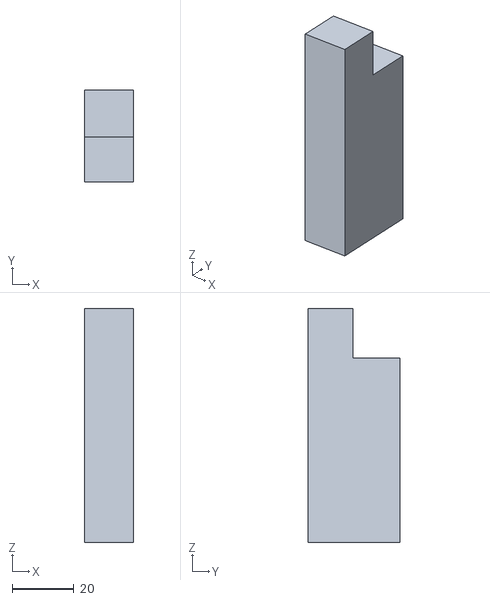
[picture p58: CAD file, 2026-08-11]
development/r9/generated/qualification_v5/stl/r9_front_beam_lower_lap_coupon.stl
16.0 x 30.0 x 76.0
