rupret007/story-corner-shelf/generated/model_only_3mf/MODEL_ONLY_PETG_Palatine_Fascia_EndCap.3mf

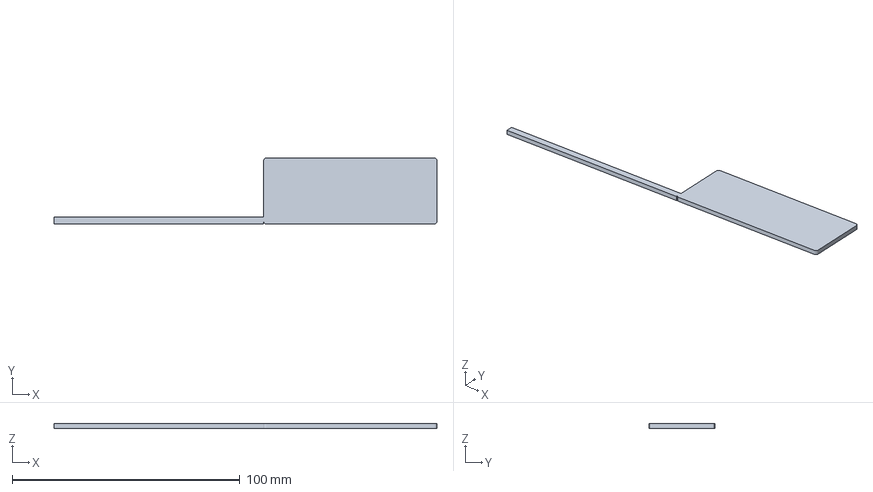
[picture p59: CAD file, 2026-08-18]
generated/model_only_3mf/MODEL_ONLY_PETG_Palatine_Fascia_EndCap.3mf
168.1 x 29.0 x 2.00 mm
