rupret007/story-corner-shelf/generated/PETG_Palatine_ReentrantCorner_Pilaster_SlipCover.stl

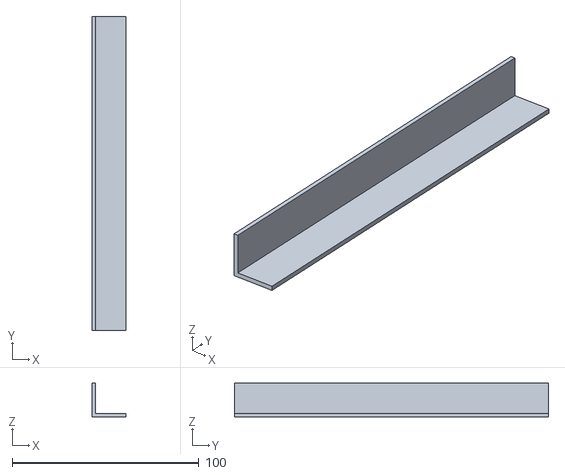
[picture p60: CAD file, 2026-08-18]
generated/PETG_Palatine_ReentrantCorner_Pilaster_SlipCover.stl
18.0 x 168.1 x 18.0
