rupret007/story-corner-shelf/development/r10/generated/one_bay_qualification_v1/individual_model_only_3mf/MODEL_ONLY_r10_first_wall_multi_cable_comb_hook.3mf

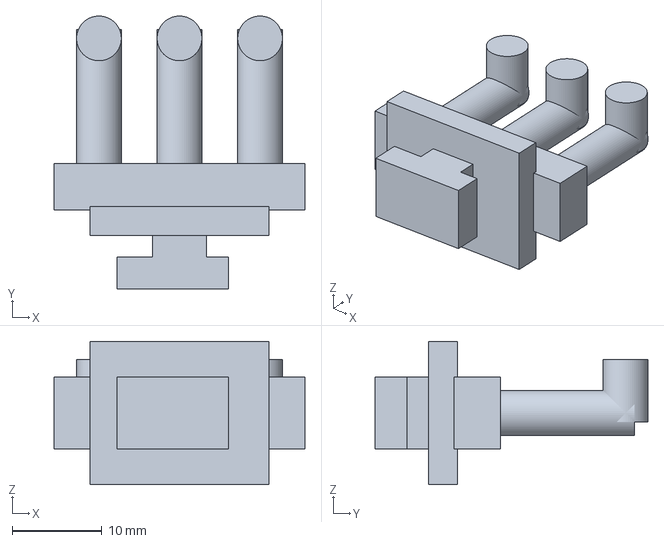
[picture p61: CAD file, 2026-08-18]
development/r10/generated/one_bay_qualification_v1/individual_model_only_3mf/MODEL_ONLY_r10_first_wall_multi_cable_comb_hook.3mf
28.0 x 30.5 x 16.0 mm
