rupret007/story-corner-shelf/development/r11/generated/first_outer_actual_bay_qualification_v1/individual_model_only_3mf/MODEL_ONLY_r11_bay0_positive_keystone.3mf

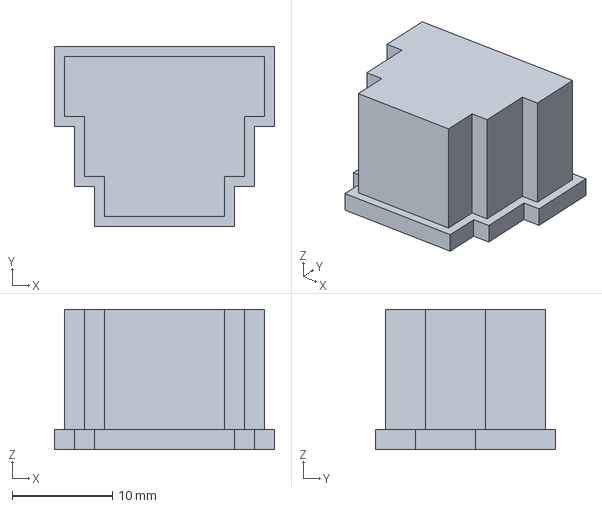
[picture p62: CAD file, 2026-08-18]
development/r11/generated/first_outer_actual_bay_qualification_v1/individual_model_only_3mf/MODEL_ONLY_r11_bay0_positive_keystone.3mf
22.0 x 18.0 x 14.0 mm
