rupret007/story-corner-shelf/development/r11/generated/first_outer_actual_bay_qualification_v1/stl/r11_first_wall_multi_cable_comb_hook.stl

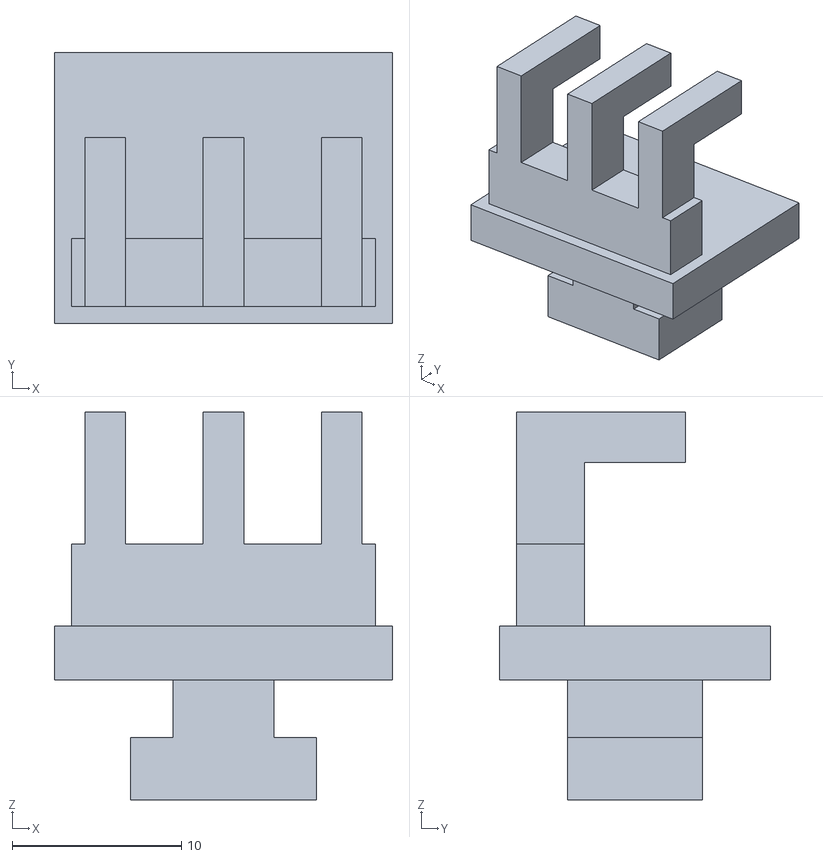
[picture p63: CAD file, 2026-08-18]
development/r11/generated/first_outer_actual_bay_qualification_v1/stl/r11_first_wall_multi_cable_comb_hook.stl
20.0 x 16.0 x 23.0
