rupret007/story-corner-shelf/development/r6/generated/individual_model_only_3mf/MODEL_ONLY_R6_DEV_FINAL_X_TOP_CAPTURE_WEDGE_UNIVERSAL.3mf

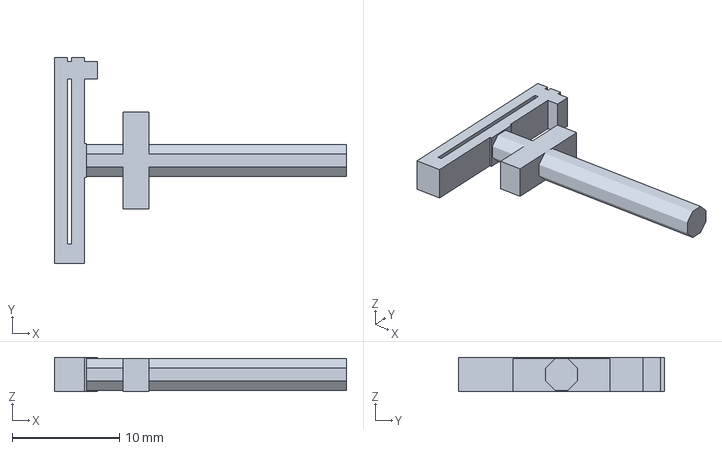
[picture p64: CAD file, 2026-08-09]
development/r6/generated/individual_model_only_3mf/MODEL_ONLY_R6_DEV_FINAL_X_TOP_CAPTURE_WEDGE_UNIVERSAL.3mf
27.2 x 19.2 x 3.20 mm
