rupret007/story-corner-shelf/development/r6/generated/stl/R6_DEV_ORNAMENT_THROUGH_CARRIER_RIGHT.stl

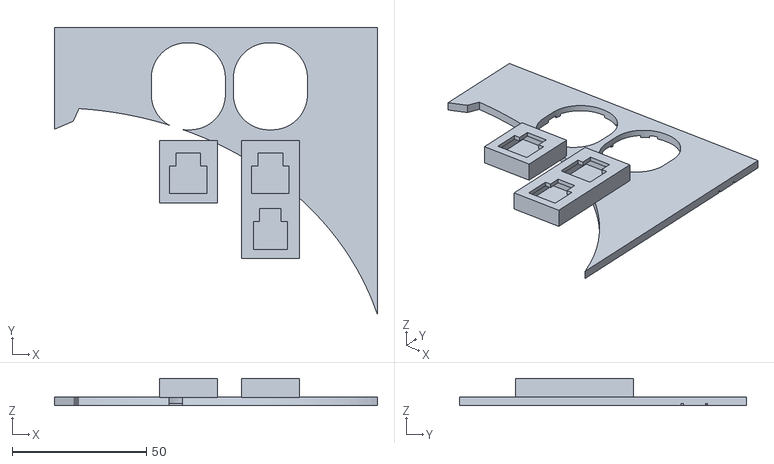
[picture p65: CAD file, 2026-08-09]
development/r6/generated/stl/R6_DEV_ORNAMENT_THROUGH_CARRIER_RIGHT.stl
120.4 x 107.1 x 10.2
