rupret007/story-corner-shelf/development/r8/generated/one_bay_qualification_v2/individual_model_only_3mf/MODEL_ONLY_r8_one_bay_right_smooth_locator_seated_keeper_d_frame.3mf

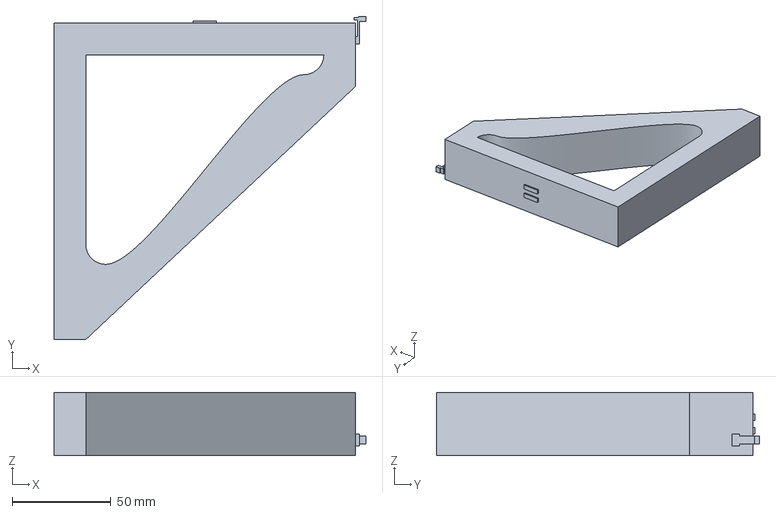
[picture p66: CAD file, 2026-08-11]
development/r8/generated/one_bay_qualification_v2/individual_model_only_3mf/MODEL_ONLY_r8_one_bay_right_smooth_locator_seated_keeper_d_frame.3mf
157.6 x 163.4 x 32.0 mm
