rupret007/story-corner-shelf/development/r8/generated/one_bay_qualification_v2/stl/r8_one_bay_retained_blank.stl

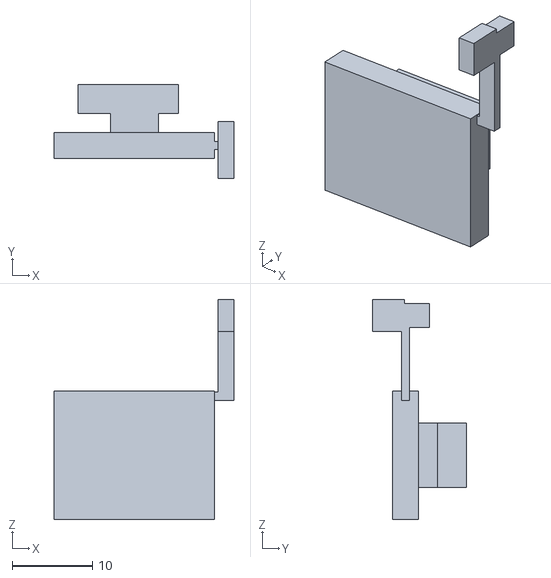
[picture p67: CAD file, 2026-08-11]
development/r8/generated/one_bay_qualification_v2/stl/r8_one_bay_retained_blank.stl
22.4 x 11.7 x 27.4
