rupret007/story-corner-shelf/development/r8/generated/qualification_v2/individual_model_only_3mf/MODEL_ONLY_r8_smooth_curved_core.3mf

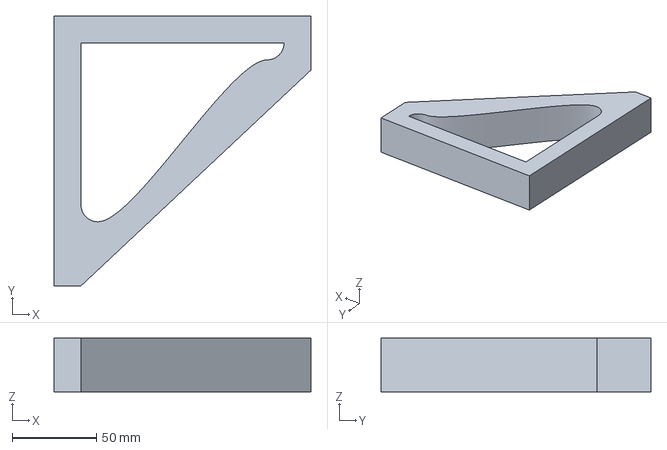
[picture p68: CAD file, 2026-08-11]
development/r8/generated/qualification_v2/individual_model_only_3mf/MODEL_ONLY_r8_smooth_curved_core.3mf
152.4 x 160.0 x 32.0 mm
