rupret007/story-corner-shelf/development/r9/generated/qualification_v5/stage0_individual_model_only_3mf/MODEL_ONLY_r9_gate0_clearance_key_0p4_handle_down.3mf

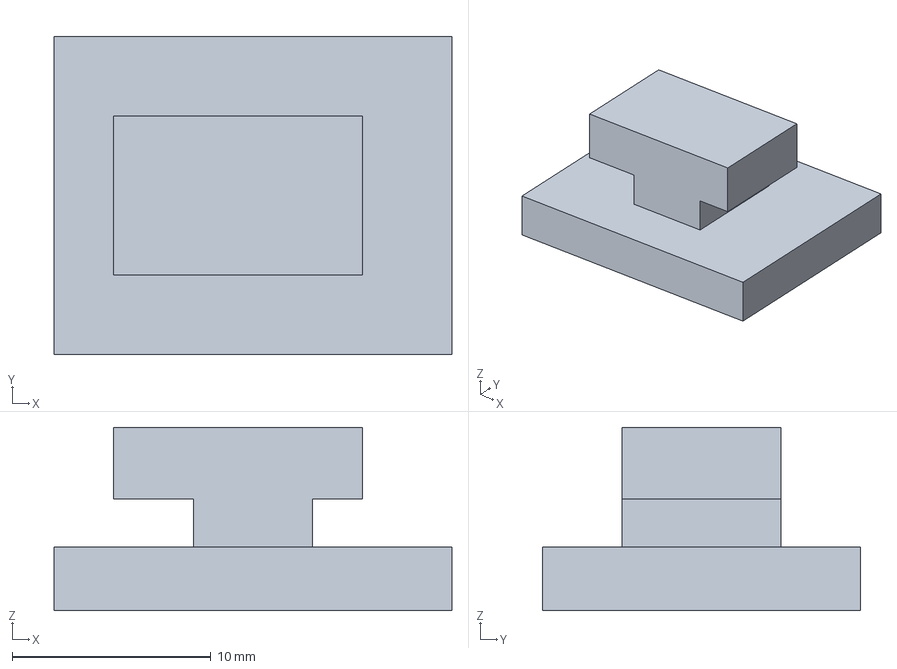
[picture p70: CAD file, 2026-08-11]
development/r9/generated/qualification_v5/stage0_individual_model_only_3mf/MODEL_ONLY_r9_gate0_clearance_key_0p4_handle_down.3mf
20.0 x 16.0 x 9.20 mm
