rupret007/story-corner-shelf/development/r9/generated/qualification_v5/stl/r9_through_hidden_corner_half.stl

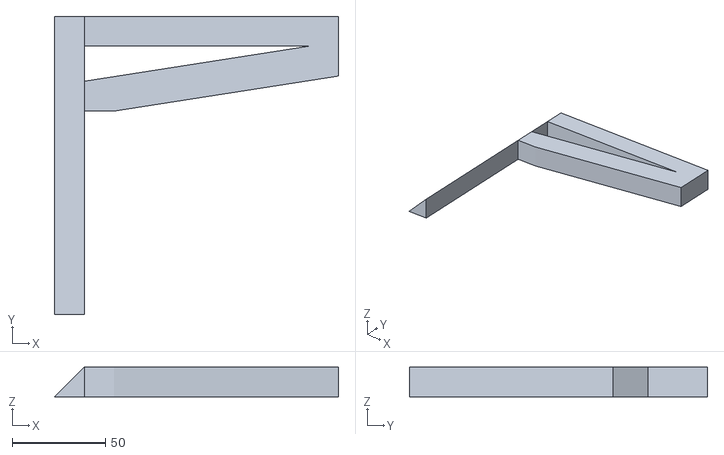
[picture p71: CAD file, 2026-08-11]
development/r9/generated/qualification_v5/stl/r9_through_hidden_corner_half.stl
152.4 x 160.0 x 16.0
