rupret007/story-corner-shelf/generated/model_only_3mf/MODEL_ONLY_PETG_TopTile_Center_6inPitch.3mf

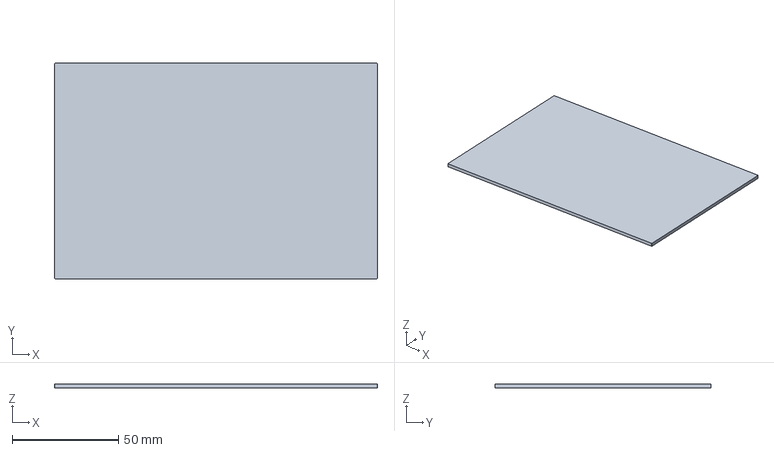
[picture p72: CAD file, 2026-08-18]
generated/model_only_3mf/MODEL_ONLY_PETG_TopTile_Center_6inPitch.3mf
151.8 x 101.3 x 2.00 mm
