rupret007/story-corner-shelf/generated/PETG_TopTile_ParametricEnd.stl

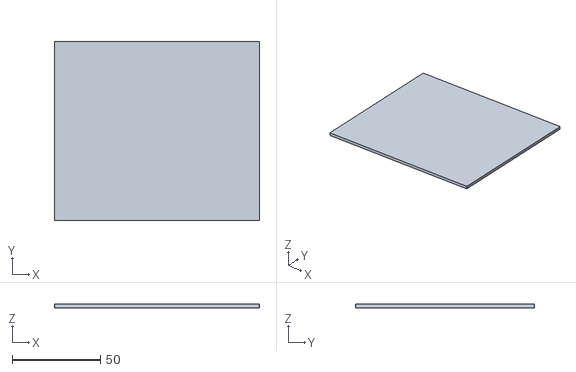
[picture p73: CAD file, 2026-08-18]
generated/PETG_TopTile_ParametricEnd.stl
116.1 x 101.3 x 2.00
