rupret007/story-corner-shelf/development/r10/generated/one_bay_qualification_v1/individual_model_only_3mf/MODEL_ONLY_r10_one_bay_center_log_retainer.3mf

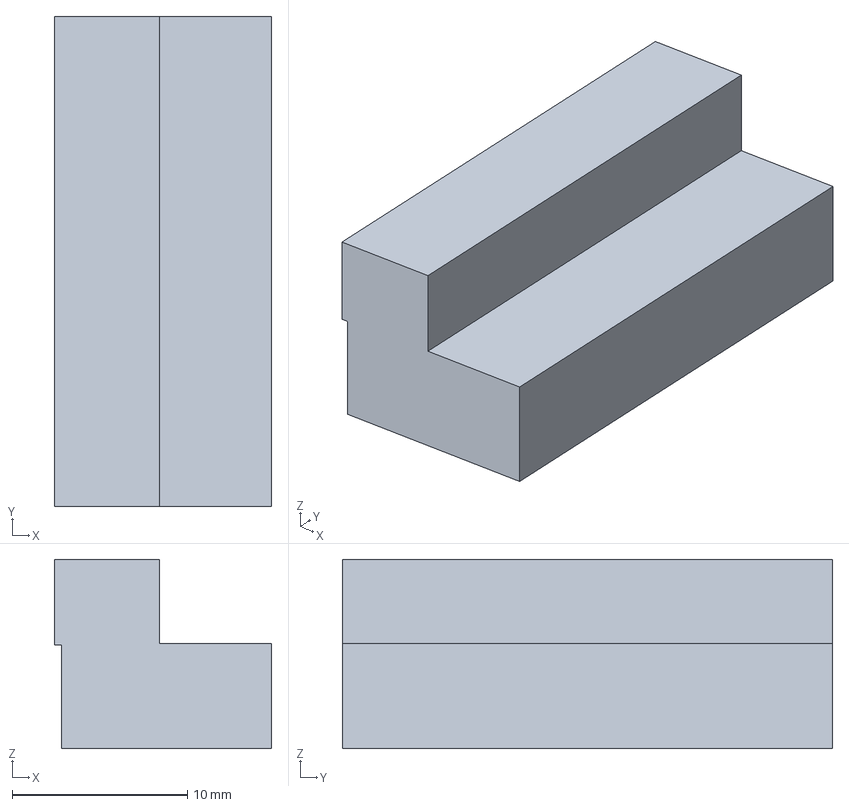
[picture p74: CAD file, 2026-08-18]
development/r10/generated/one_bay_qualification_v1/individual_model_only_3mf/MODEL_ONLY_r10_one_bay_center_log_retainer.3mf
12.4 x 28.0 x 10.8 mm
