rupret007/story-corner-shelf/development/r10/generated/one_bay_qualification_v1/stl/r10_one_bay_left_cassette_half.stl

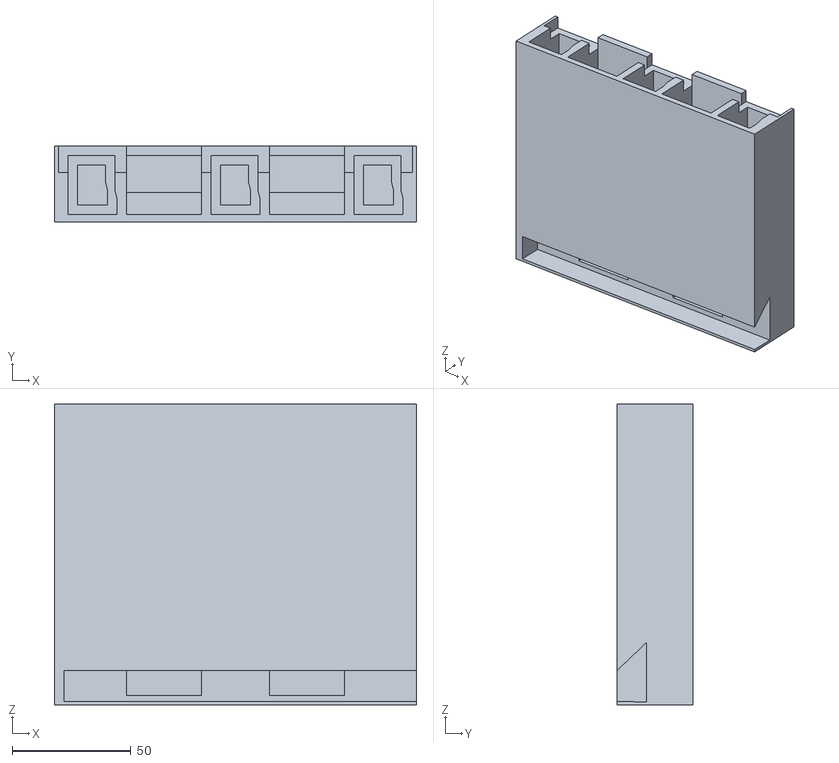
[picture p75: CAD file, 2026-08-18]
development/r10/generated/one_bay_qualification_v1/stl/r10_one_bay_left_cassette_half.stl
152.4 x 32.0 x 126.7
