rupret007/story-corner-shelf/development/r11/generated/first_outer_actual_bay_qualification_v1/individual_model_only_3mf/MODEL_ONLY_r11_bay0_right_terminal_integrated_half_deck.3mf

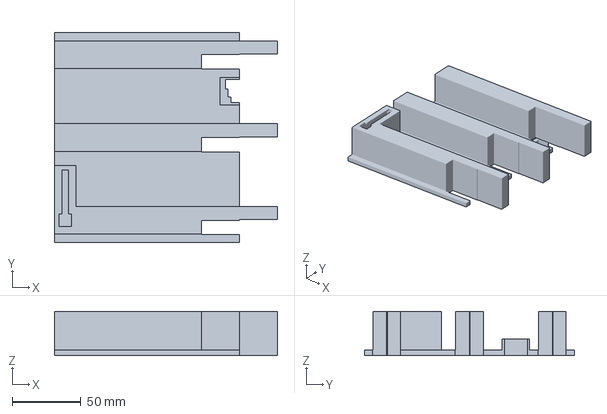
[picture p76: CAD file, 2026-08-18]
development/r11/generated/first_outer_actual_bay_qualification_v1/individual_model_only_3mf/MODEL_ONLY_r11_bay0_right_terminal_integrated_half_deck.3mf
162.2 x 152.4 x 32.0 mm
