rupret007/story-corner-shelf/development/r6/generated/model_only_3mf/MODEL_ONLY_R6_WORST_CASE_ONE_BAY_QUALIFICATION.3mf

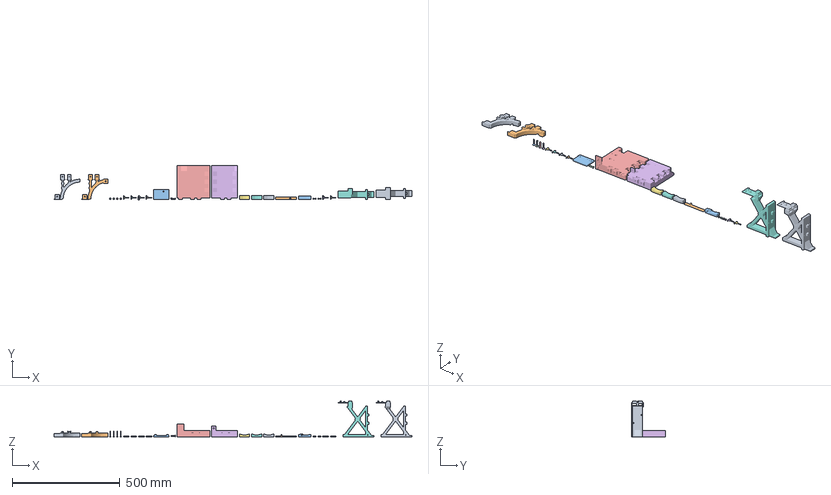
[picture p77: CAD file, 2026-08-09]
development/r6/generated/model_only_3mf/MODEL_ONLY_R6_WORST_CASE_ONE_BAY_QUALIFICATION.3mf
1662.2 x 159.6 x 165.9 mm
lower::long_wall_5ft::arcade_half::01
lower::long_wall_5ft::arcade_half::02
lower::long_wall_5ft::cassette_lock::support_01_left_slot
lower::long_wall_5ft::cassette_lock::support_01_right_slot
lower::long_wall_5ft::cassette_lock::support_02_left_slot
lower::long_wall_5ft::cassette_lock::support_02_right_slot
lower::long_wall_5ft::cassette_top_retention_wedge::half_01_wedge_1
lower::long_wall_5ft::cassette_top_retention_wedge::half_01_wedge_2
lower::long_wall_5ft::cassette_top_retention_wedge::half_02_wedge_1
lower::long_wall_5ft::cassette_top_retention_wedge::half_02_wedge_2
lower::long_wall_5ft::crown_bridge::01
lower::long_wall_5ft::crown_bridge_retention_pin::01
lower::long_wall_5ft::deck_cassette::01
lower::long_wall_5ft::deck_cassette::02
lower::long_wall_5ft::diaphragm_bowtie_key::seam_01_depth_1
lower::long_wall_5ft::diaphragm_bowtie_key::seam_01_depth_2
lower::long_wall_5ft::diaphragm_bowtie_key::seam_01_depth_3
lower::long_wall_5ft::fixed_crown_diaphragm_keeper_strip::seam_01
lower::long_wall_5ft::fixed_crown_entablature_tie_key::seam_01
lower::long_wall_5ft::indexed_vertical_quarter_turn_pin::seam_01_front_tie_reach
lower::long_wall_5ft::indexed_vertical_quarter_turn_pin::seam_01_keeper_reach
lower::long_wall_5ft::spring_retention_wedge::half_01
lower::long_wall_5ft::spring_retention_wedge::half_02
lower::long_wall_5ft::structural_pier_x_corbel::01
lower::long_wall_5ft::structural_pier_x_corbel::02
