rupret007/story-corner-shelf/development/r6/generated/stl/R6_DEV_CASSETTE_RETURN_02_OF_06.stl

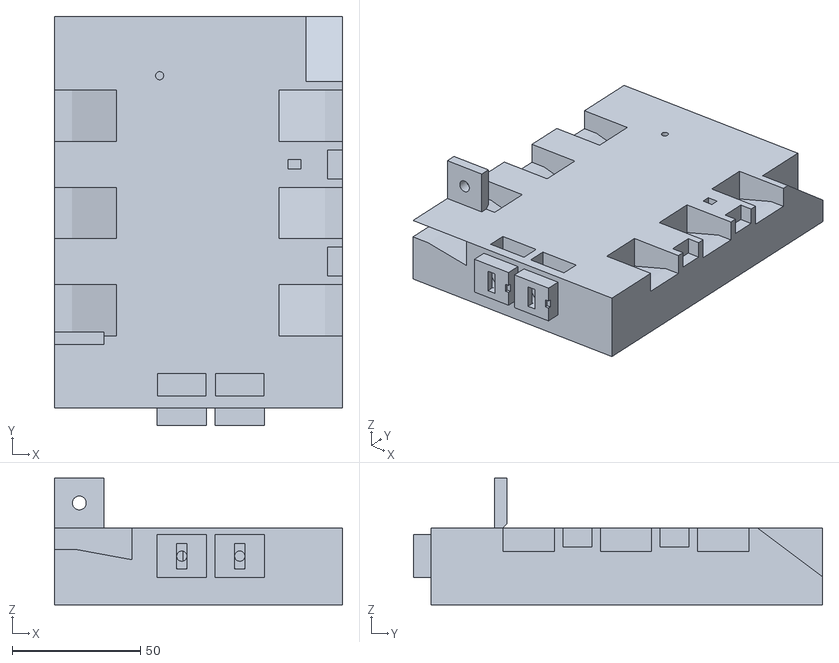
[picture p78: CAD file, 2026-08-09]
development/r6/generated/stl/R6_DEV_CASSETTE_RETURN_02_OF_06.stl
112.2 x 159.2 x 49.4
