rupret007/story-corner-shelf/development/r7/generated/cable_peg_qualification_v4/individual_model_only_3mf/MODEL_ONLY_R7_DEV_CABLE_PEG_EXACT_R6_PIER_OVERLAY_COUPON.3mf

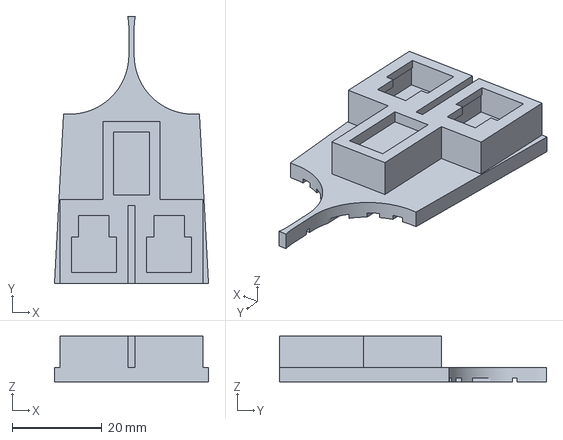
[picture p79: CAD file, 2026-08-11]
development/r7/generated/cable_peg_qualification_v4/individual_model_only_3mf/MODEL_ONLY_R7_DEV_CABLE_PEG_EXACT_R6_PIER_OVERLAY_COUPON.3mf
34.4 x 59.6 x 10.2 mm
