rupret007/story-corner-shelf/development/r8/generated/qualification_v2/stl/r8_retained_shortened_coil_j_hook.stl

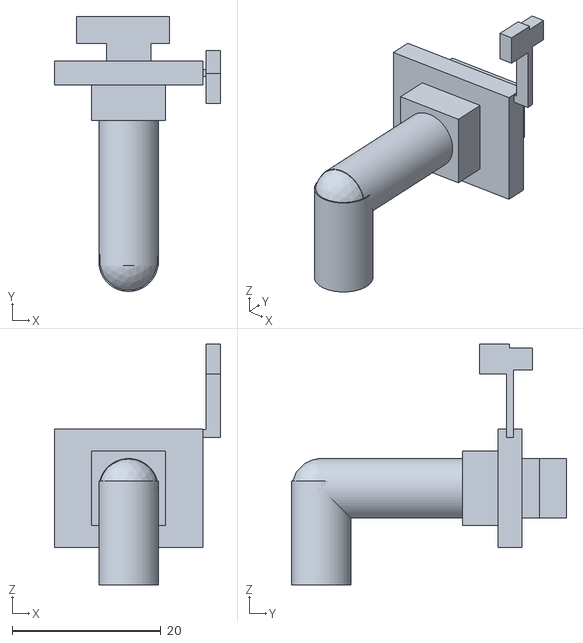
[picture p80: CAD file, 2026-08-11]
development/r8/generated/qualification_v2/stl/r8_retained_shortened_coil_j_hook.stl
22.4 x 37.0 x 32.4
