rupret007/story-corner-shelf/development/r9/generated/qualification_v5/stl/r9_return_outer_bookend_additive_two_socket_candidate.stl

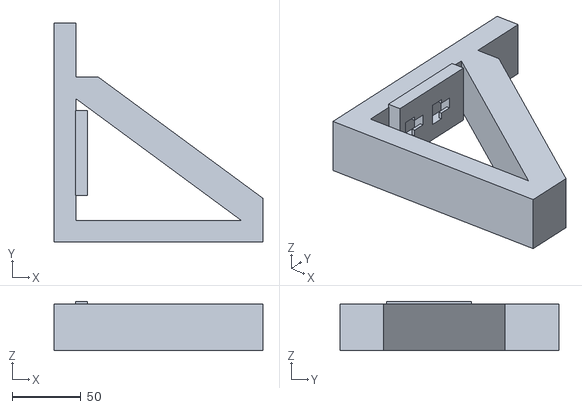
[picture p81: CAD file, 2026-08-11]
development/r9/generated/qualification_v5/stl/r9_return_outer_bookend_additive_two_socket_candidate.stl
152.4 x 160.0 x 36.0
