rupret007/story-corner-shelf/generated/model_only_3mf/MODEL_ONLY_PETG_Palatine_ArcadeFascia_Half_left_long_wall_5ft.3mf

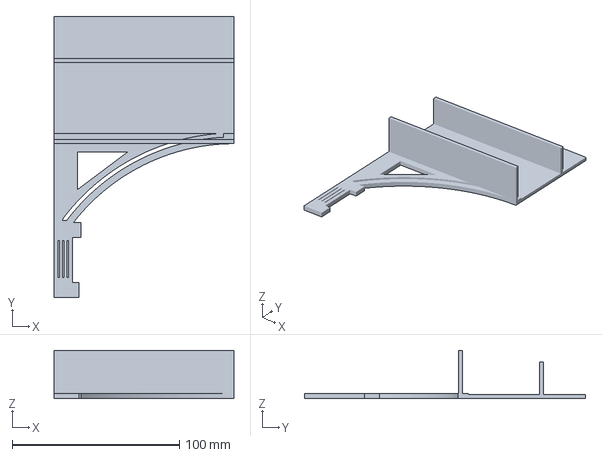
[picture p82: CAD file, 2026-08-18]
generated/model_only_3mf/MODEL_ONLY_PETG_Palatine_ArcadeFascia_Half_left_long_wall_5ft.3mf
107.6 x 168.1 x 29.0 mm
