rupret007/story-corner-shelf/development/r11/generated/first_outer_actual_bay_qualification_v1/stl/r11_first_wall_socket_0_flush_blank.stl

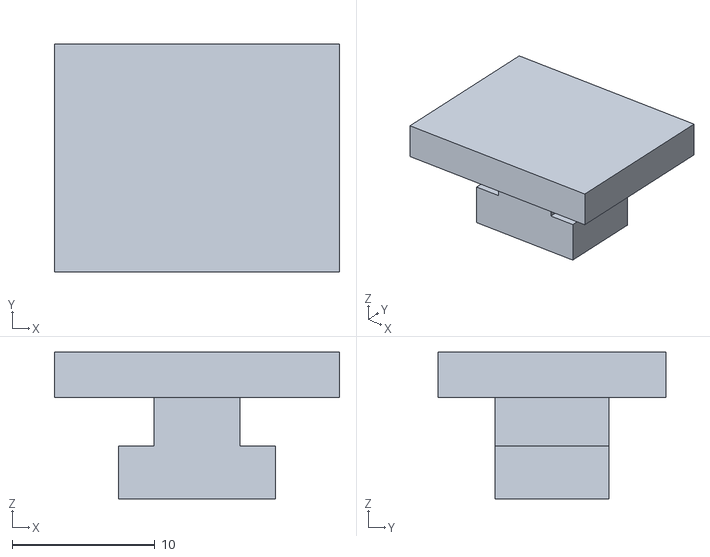
[picture p83: CAD file, 2026-08-18]
development/r11/generated/first_outer_actual_bay_qualification_v1/stl/r11_first_wall_socket_0_flush_blank.stl
20.0 x 16.0 x 10.3
