rupret007/story-corner-shelf/development/r6/generated/individual_model_only_3mf/MODEL_ONLY_R6_DEV_CASSETTE_THROUGH_07_OF_12.3mf

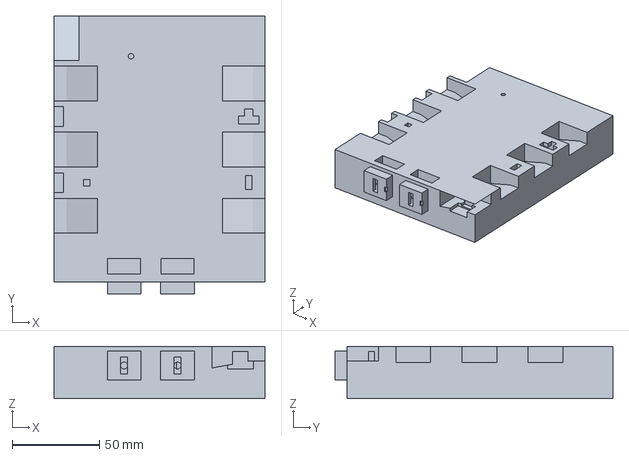
[picture p84: CAD file, 2026-08-09]
development/r6/generated/individual_model_only_3mf/MODEL_ONLY_R6_DEV_CASSETTE_THROUGH_07_OF_12.3mf
120.6 x 159.2 x 30.0 mm
