rupret007/story-corner-shelf/development/r6/generated/model_only_3mf/MODEL_ONLY_R6_PRINT_FIRST_PROTOTYPES.3mf

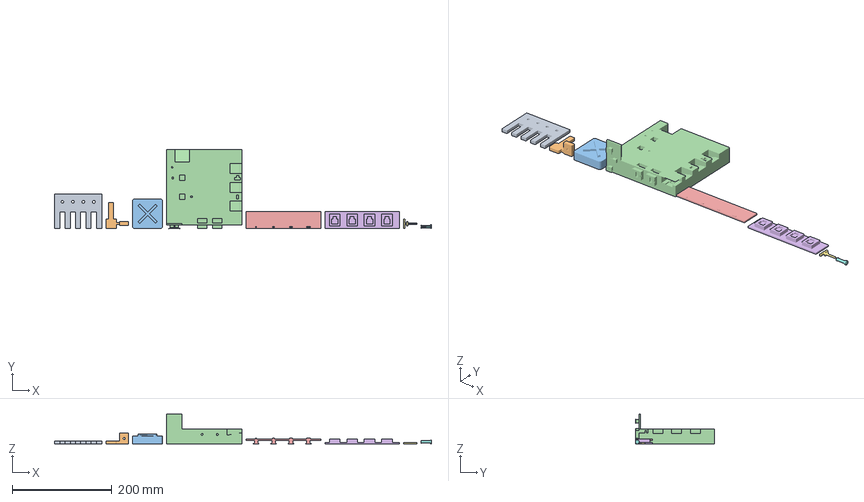
[picture p85: CAD file, 2026-08-09]
development/r6/generated/model_only_3mf/MODEL_ONLY_R6_PRINT_FIRST_PROTOTYPES.3mf
757.6 x 159.6 x 60.0 mm
print_first::01::R6_DEV_JOINERY_CLEARANCE_LADDER_RECEIVER
print_first::02::R6_DEV_JOINERY_CLEARANCE_LADDER_TONGUE
print_first::03::R6_DEV_BLOCKED_WALL_SCREW_BEARING_COUPON_SOLID_NO_HOLE
print_first::04::R6_DEV_CASSETTE_THROUGH_01_OF_12
print_first::05::R6_DEV_ORNAMENT_PRINT_FIRST_KEYHOLE_MALE_LADDER
print_first::06::R6_DEV_ORNAMENT_PRINT_FIRST_KEYHOLE_FEMALE_LADDER
print_first::07::R6_DEV_FINAL_X_TOP_CAPTURE_WEDGE_UNIVERSAL
print_first::08::R6_DEV_CROWN_BRIDGE_ANTI_DROP_PIN_RETENTION_ONLY
