rupret007/story-corner-shelf/development/r6/generated/stl/R6_DEV_INDEXED_VERTICAL_QUARTER_TURN_PIN_FRONT_TIE_REACH.stl

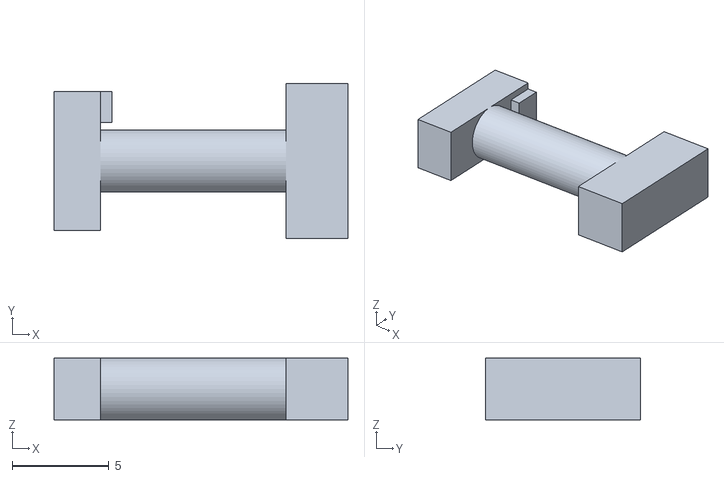
[picture p86: CAD file, 2026-08-09]
development/r6/generated/stl/R6_DEV_INDEXED_VERTICAL_QUARTER_TURN_PIN_FRONT_TIE_REACH.stl
15.2 x 8.00 x 3.20
