rupret007/story-corner-shelf/development/r9/generated/one_bay_prototype_v3/stl/r9_one_bay_shelf_cassette.stl

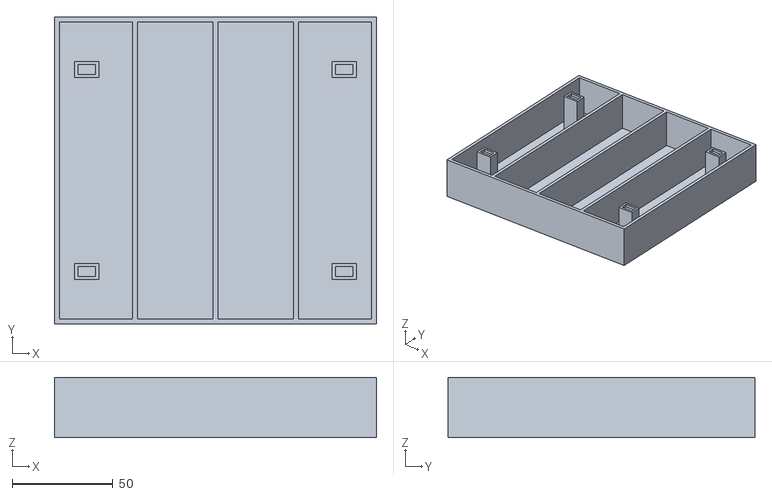
[picture p87: CAD file, 2026-08-11]
development/r9/generated/one_bay_prototype_v3/stl/r9_one_bay_shelf_cassette.stl
160.0 x 152.4 x 30.0
