rupret007/story-corner-shelf/development/r9/generated/qualification_v5/stl/r9_90_degree_tabletop_angle_fixture.stl

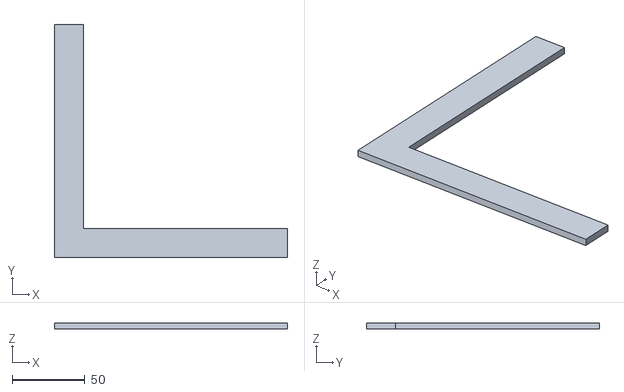
[picture p88: CAD file, 2026-08-11]
development/r9/generated/qualification_v5/stl/r9_90_degree_tabletop_angle_fixture.stl
160.0 x 160.0 x 4.00
