rupret007/story-corner-shelf/generated/model_only_3mf/MODEL_ONLY_PETG_RearCurb_ParametricEnd_long_wall_5ft.3mf

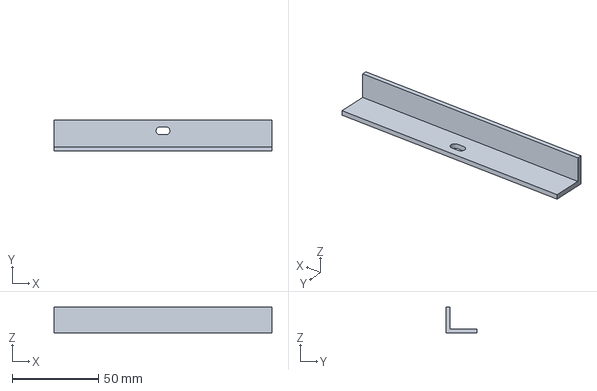
[picture p89: CAD file, 2026-08-18]
generated/model_only_3mf/MODEL_ONLY_PETG_RearCurb_ParametricEnd_long_wall_5ft.3mf
126.5 x 18.0 x 15.0 mm
