rupret007/story-corner-shelf/generated/PETG_Palatine_ArcadeFascia_Half_right_short_wall_3ft.stl

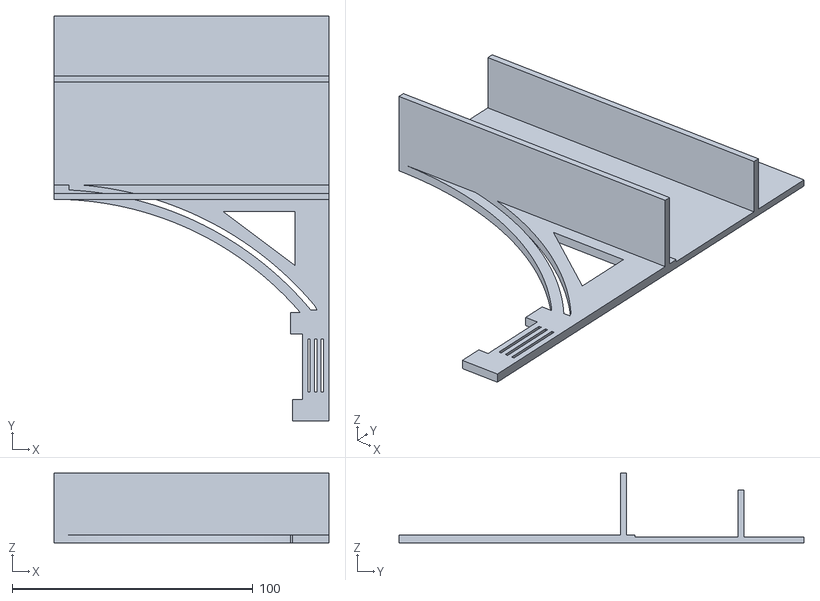
[picture p90: CAD file, 2026-08-18]
generated/PETG_Palatine_ArcadeFascia_Half_right_short_wall_3ft.stl
114.0 x 168.1 x 29.0
