rupret007/story-corner-shelf/development/r10/generated/one_bay_qualification_v1/stl/r10_one_bay_right_support_retainer.stl

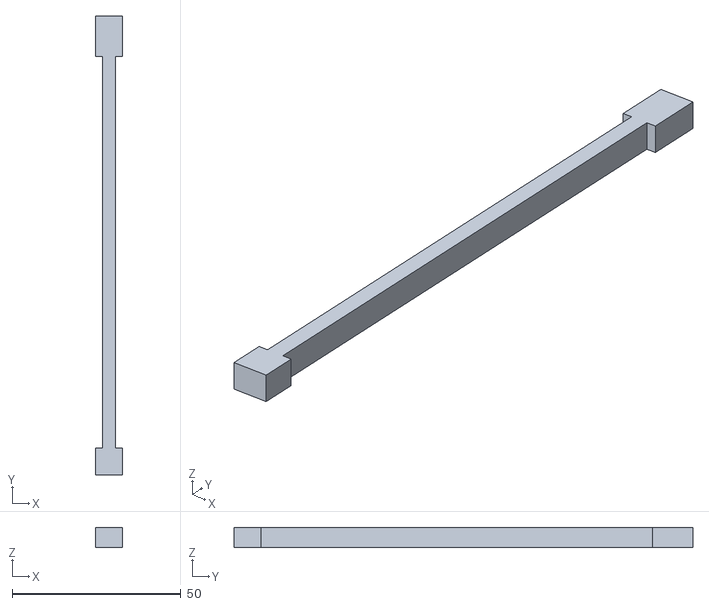
[picture p91: CAD file, 2026-08-18]
development/r10/generated/one_bay_qualification_v1/stl/r10_one_bay_right_support_retainer.stl
8.00 x 136.0 x 6.00
