rupret007/story-corner-shelf/development/r11/generated/first_outer_actual_bay_qualification_v1/individual_model_only_3mf/MODEL_ONLY_r11_first_wall_s0_fused_two_socket_support.3mf

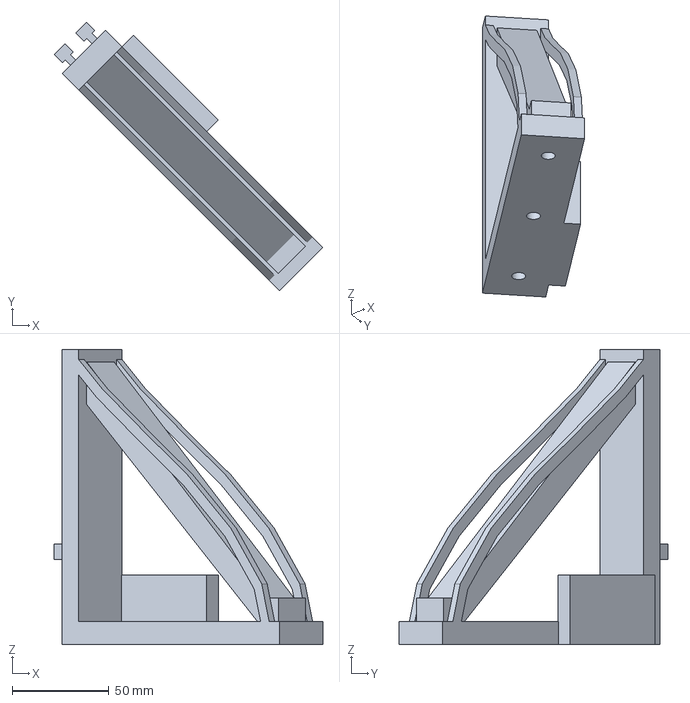
[picture p92: CAD file, 2026-08-18]
development/r11/generated/first_outer_actual_bay_qualification_v1/individual_model_only_3mf/MODEL_ONLY_r11_first_wall_s0_fused_two_socket_support.3mf
138.9 x 138.9 x 152.4 mm
