rupret007/story-corner-shelf/development/r6/generated/individual_model_only_3mf/MODEL_ONLY_R6_DEV_FINAL_X_X_CORBEL_PIER_RUN_START_TERMINAL_INTEGRATED_CAP.3mf

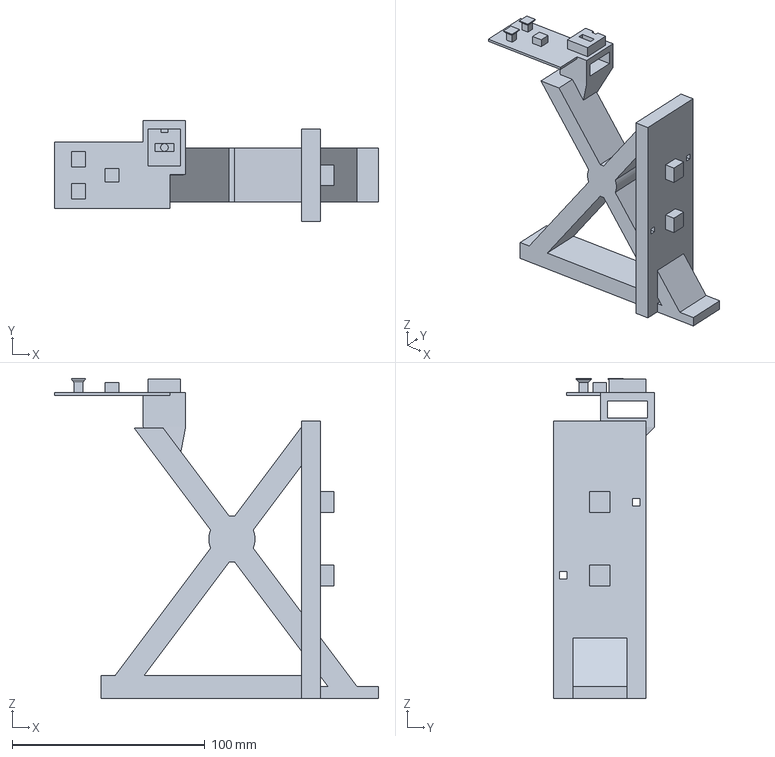
[picture p93: CAD file, 2026-08-09]
development/r6/generated/individual_model_only_3mf/MODEL_ONLY_R6_DEV_FINAL_X_X_CORBEL_PIER_RUN_START_TERMINAL_INTEGRATED_CAP.3mf
168.0 x 52.4 x 165.9 mm
