rupret007/story-corner-shelf/development/r6/generated/model_only_3mf/MODEL_ONLY_R6_ONE_LEVEL_L.3mf

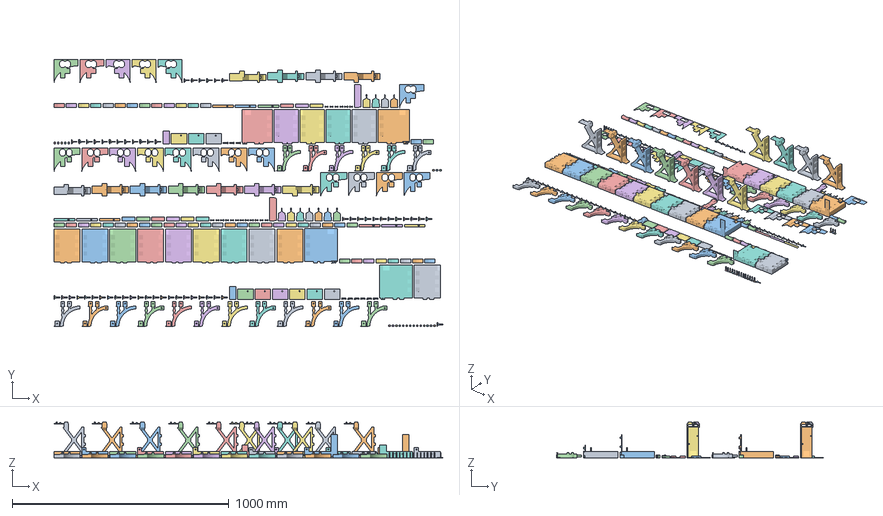
[picture p94: CAD file, 2026-08-09]
development/r6/generated/model_only_3mf/MODEL_ONLY_R6_ONE_LEVEL_L.3mf
1796.7 x 1234.4 x 165.9 mm
lower::long_wall_5ft::arcade_half::01
lower::long_wall_5ft::arcade_half::02
lower::long_wall_5ft::arcade_half::03
lower::long_wall_5ft::arcade_half::04
lower::long_wall_5ft::arcade_half::05
lower::long_wall_5ft::arcade_half::06
lower::long_wall_5ft::arcade_half::07
lower::long_wall_5ft::arcade_half::08
lower::long_wall_5ft::arcade_half::09
lower::long_wall_5ft::arcade_half::10
lower::long_wall_5ft::arcade_half::11
lower::long_wall_5ft::arcade_half::12
lower::long_wall_5ft::cassette_lock::support_01_left_slot
lower::long_wall_5ft::cassette_lock::support_01_right_slot
lower::long_wall_5ft::cassette_lock::support_02_left_slot
lower::long_wall_5ft::cassette_lock::support_02_right_slot
lower::long_wall_5ft::cassette_lock::support_03_left_slot
lower::long_wall_5ft::cassette_lock::support_03_right_slot
lower::long_wall_5ft::cassette_lock::support_04_left_slot
lower::long_wall_5ft::cassette_lock::support_04_right_slot
lower::long_wall_5ft::cassette_lock::support_05_left_slot
lower::long_wall_5ft::cassette_lock::support_05_right_slot
lower::long_wall_5ft::cassette_lock::support_06_left_slot
lower::long_wall_5ft::cassette_lock::support_06_right_slot
lower::long_wall_5ft::cassette_lock::support_07_left_slot
lower::long_wall_5ft::cassette_lock::support_07_right_slot
lower::long_wall_5ft::cassette_top_retention_wedge::half_01_wedge_1
lower::long_wall_5ft::cassette_top_retention_wedge::half_01_wedge_2
lower::long_wall_5ft::cassette_top_retention_wedge::half_02_wedge_1
lower::long_wall_5ft::cassette_top_retention_wedge::half_02_wedge_2
lower::long_wall_5ft::cassette_top_retention_wedge::half_03_wedge_1
lower::long_wall_5ft::cassette_top_retention_wedge::half_03_wedge_2
lower::long_wall_5ft::cassette_top_retention_wedge::half_04_wedge_1
lower::long_wall_5ft::cassette_top_retention_wedge::half_04_wedge_2
lower::long_wall_5ft::cassette_top_retention_wedge::half_05_wedge_1
lower::long_wall_5ft::cassette_top_retention_wedge::half_05_wedge_2
lower::long_wall_5ft::cassette_top_retention_wedge::half_06_wedge_1
lower::long_wall_5ft::cassette_top_retention_wedge::half_06_wedge_2
lower::long_wall_5ft::cassette_top_retention_wedge::half_07_wedge_1
lower::long_wall_5ft::cassette_top_retention_wedge::half_07_wedge_2
lower::long_wall_5ft::cassette_top_retention_wedge::half_08_wedge_1
lower::long_wall_5ft::cassette_top_retention_wedge::half_08_wedge_2
lower::long_wall_5ft::cassette_top_retention_wedge::half_09_wedge_1
lower::long_wall_5ft::cassette_top_retention_wedge::half_09_wedge_2
lower::long_wall_5ft::cassette_top_retention_wedge::half_10_wedge_1
lower::long_wall_5ft::cassette_top_retention_wedge::half_10_wedge_2
lower::long_wall_5ft::cassette_top_retention_wedge::half_11_wedge_1
lower::long_wall_5ft::cassette_top_retention_wedge::half_11_wedge_2
lower::long_wall_5ft::cassette_top_retention_wedge::half_12_wedge_1
lower::long_wall_5ft::cassette_top_retention_wedge::half_12_wedge_2
lower::long_wall_5ft::corner_fixed_rosette::fixed_rosette
lower::long_wall_5ft::crown_bridge::01
lower::long_wall_5ft::crown_bridge::02
lower::long_wall_5ft::crown_bridge::03
lower::long_wall_5ft::crown_bridge::04
lower::long_wall_5ft::crown_bridge::05
lower::long_wall_5ft::crown_bridge::06
lower::long_wall_5ft::crown_bridge_retention_pin::01
lower::long_wall_5ft::crown_bridge_retention_pin::02
lower::long_wall_5ft::crown_bridge_retention_pin::03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
