rupret007/story-corner-shelf/development/r6/generated/stl/R6_DEV_FINAL_X_GRAND_ARCH_HALF_THROUGH_LONG_LEFT.stl

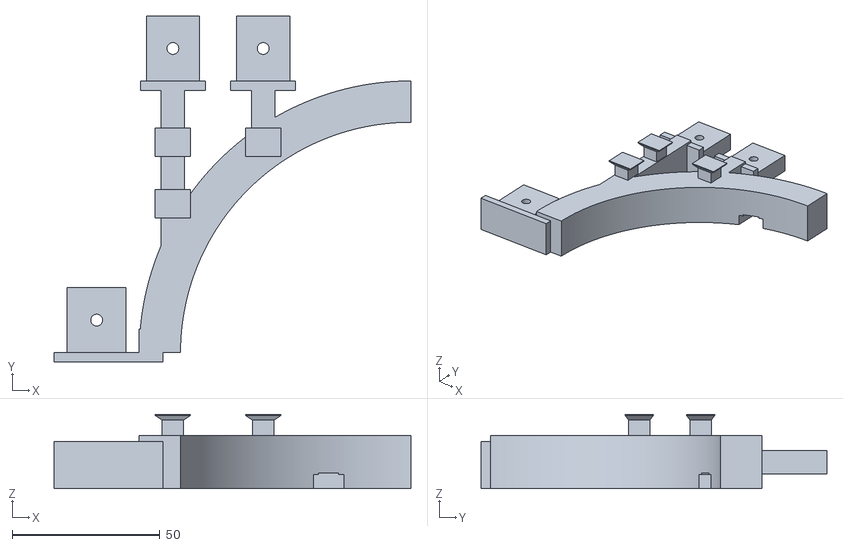
[picture p95: CAD file, 2026-08-09]
development/r6/generated/stl/R6_DEV_FINAL_X_GRAND_ARCH_HALF_THROUGH_LONG_LEFT.stl
120.8 x 117.2 x 25.2
