rupret007/story-corner-shelf/development/r8/generated/qualification_v2/individual_model_only_3mf/MODEL_ONLY_r8_retained_three_cable_comb.3mf

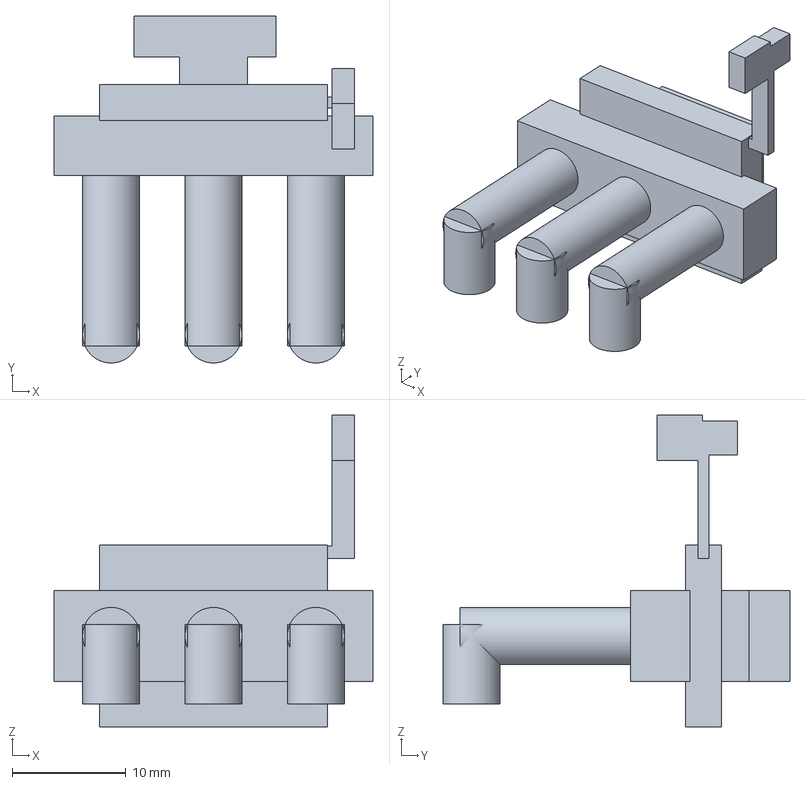
[picture p96: CAD file, 2026-08-11]
development/r8/generated/qualification_v2/individual_model_only_3mf/MODEL_ONLY_r8_retained_three_cable_comb.3mf
28.0 x 30.5 x 27.4 mm
