rupret007/story-corner-shelf/development/r8/generated/qualification_v2/stl/r8_retained_single_peg.stl

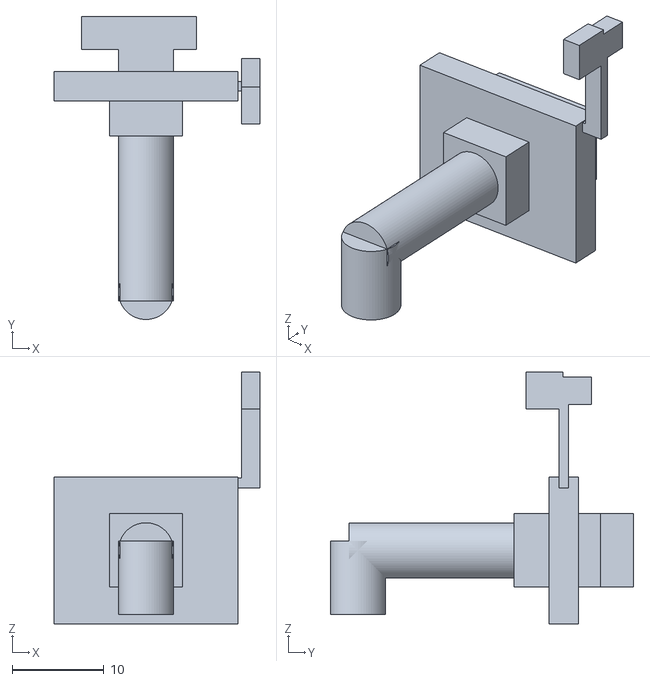
[picture p97: CAD file, 2026-08-11]
development/r8/generated/qualification_v2/stl/r8_retained_single_peg.stl
22.4 x 33.0 x 27.4
