rupret007/story-corner-shelf/development/r9/generated/qualification_v5/stl/r9_two_socket_outer_bookend_rail_fit_coupon.stl

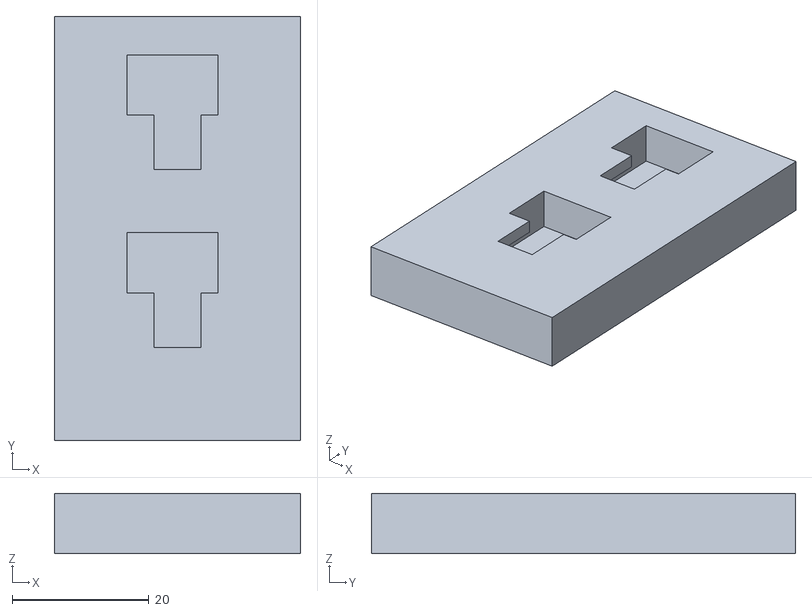
[picture p98: CAD file, 2026-08-11]
development/r9/generated/qualification_v5/stl/r9_two_socket_outer_bookend_rail_fit_coupon.stl
36.0 x 62.0 x 8.80
