rupret007/story-corner-shelf/development/r6/generated/individual_model_only_3mf/MODEL_ONLY_R6_DEV_CROWN_BRIDGE_ANTI_DROP_PIN_RETENTION_ONLY.3mf

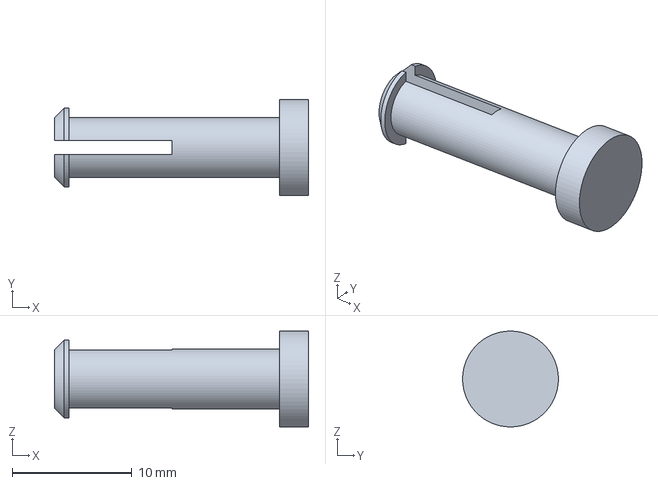
[picture p99: CAD file, 2026-08-09]
development/r6/generated/individual_model_only_3mf/MODEL_ONLY_R6_DEV_CROWN_BRIDGE_ANTI_DROP_PIN_RETENTION_ONLY.3mf
21.2 x 8.00 x 8.00 mm
