rupret007/story-corner-shelf/development/r8/generated/qualification_v2/stl/r8_clearance_key_0p5.stl

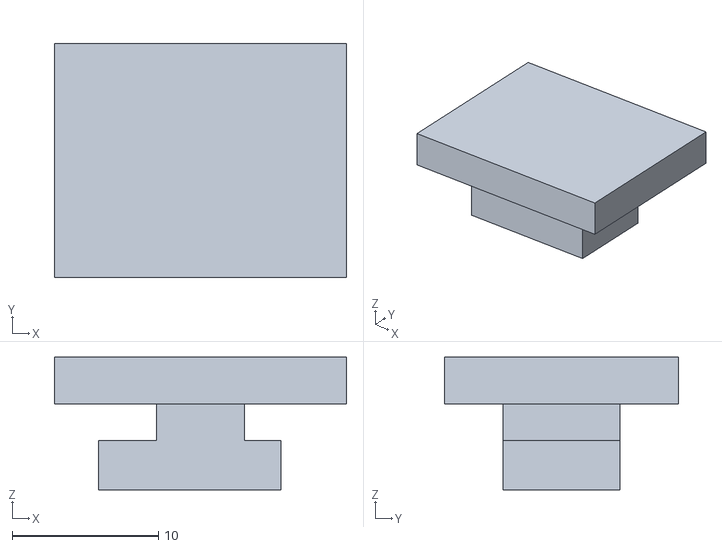
[picture p100: CAD file, 2026-08-11]
development/r8/generated/qualification_v2/stl/r8_clearance_key_0p5.stl
20.0 x 16.0 x 9.10
