rupret007/story-corner-shelf/development/r9/generated/qualification_v5/individual_model_only_3mf/MODEL_ONLY_r9_rear_ledger_female_coupon.3mf

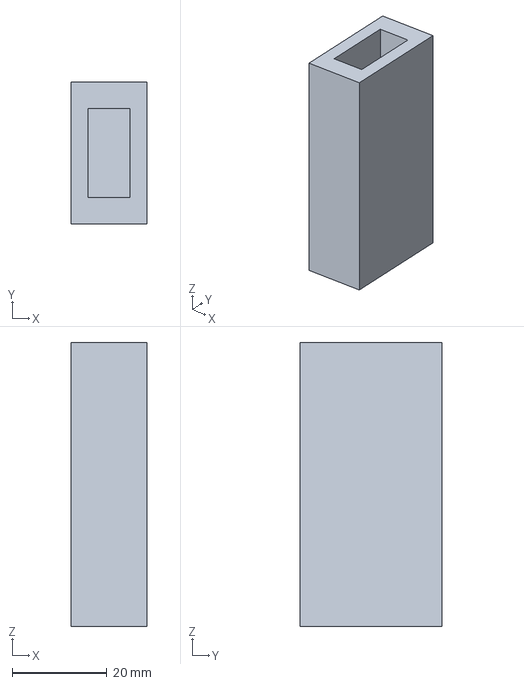
[picture p101: CAD file, 2026-08-11]
development/r9/generated/qualification_v5/individual_model_only_3mf/MODEL_ONLY_r9_rear_ledger_female_coupon.3mf
16.0 x 30.0 x 60.0 mm
