rupret007/story-corner-shelf/generated/model_only_3mf/MODEL_ONLY_PRINT_FIRST_CornerFitGauge.3mf

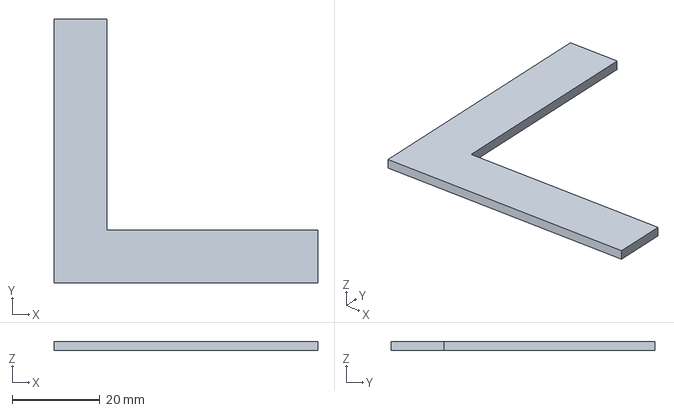
[picture p102: CAD file, 2026-08-18]
generated/model_only_3mf/MODEL_ONLY_PRINT_FIRST_CornerFitGauge.3mf
60.0 x 60.0 x 2.00 mm
