rupret007/story-corner-shelf/generated/PETG_Palatine_Keystone_SeamCover.stl

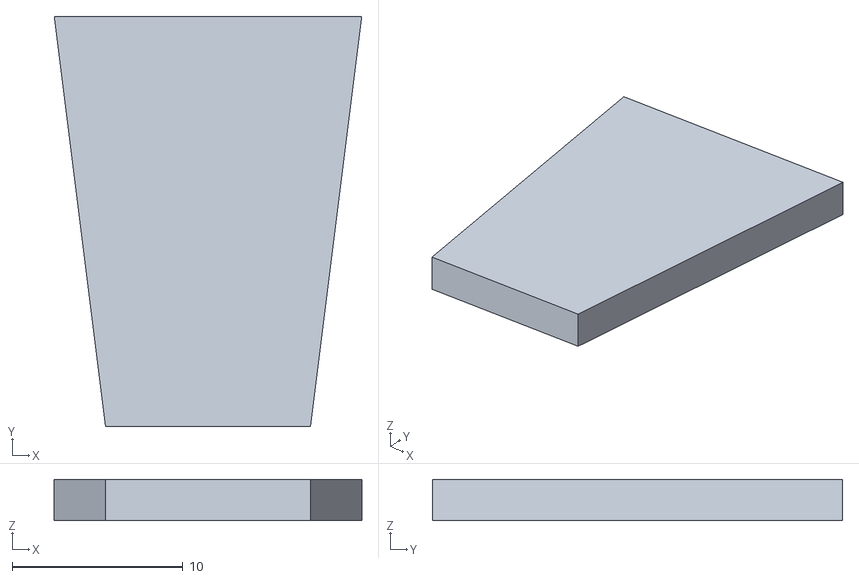
[picture p103: CAD file, 2026-08-18]
generated/PETG_Palatine_Keystone_SeamCover.stl
18.0 x 24.0 x 2.40
