rupret007/story-corner-shelf/development/r10/generated/one_bay_qualification_v1/individual_model_only_3mf/MODEL_ONLY_r10_first_wall_s0_inward_two_socket_additive_bookend_candidate.3mf

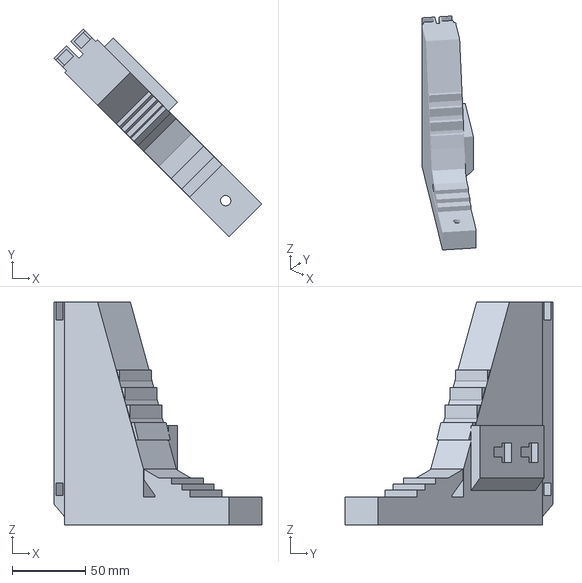
[picture p104: CAD file, 2026-08-18]
development/r10/generated/one_bay_qualification_v1/individual_model_only_3mf/MODEL_ONLY_r10_first_wall_s0_inward_two_socket_additive_bookend_candidate.3mf
141.9 x 141.9 x 152.4 mm
