rupret007/story-corner-shelf/development/r6/generated/individual_model_only_3mf/MODEL_ONLY_R6_DEV_COFFERED_CASSETTE_HALF_MAX_WIDTH_COUPON.3mf

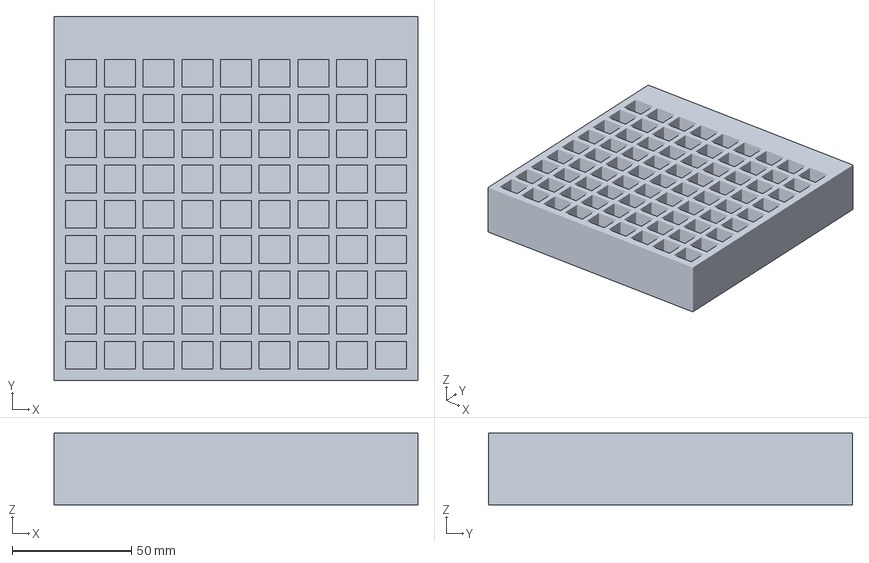
[picture p105: CAD file, 2026-08-09]
development/r6/generated/individual_model_only_3mf/MODEL_ONLY_R6_DEV_COFFERED_CASSETTE_HALF_MAX_WIDTH_COUPON.3mf
152.2 x 152.4 x 30.0 mm
