rupret007/story-corner-shelf/development/r6/generated/stl/R6_DEV_FIXED_CROWN_FRONT_INSERTED_ENTABLATURE_TIE_WITH_Q_AXIS_PIN_EYE.stl

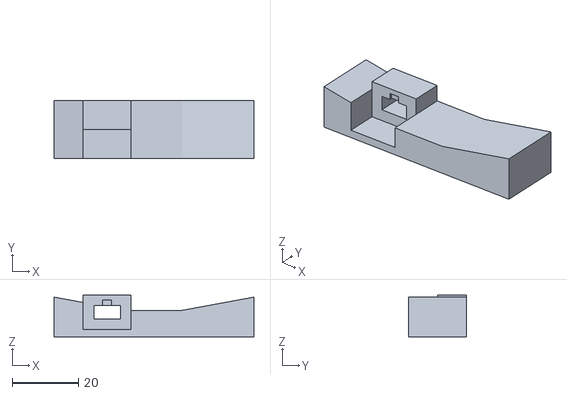
[picture p106: CAD file, 2026-08-09]
development/r6/generated/stl/R6_DEV_FIXED_CROWN_FRONT_INSERTED_ENTABLATURE_TIE_WITH_Q_AXIS_PIN_EYE.stl
60.3 x 17.6 x 12.6
