rupret007/story-corner-shelf/development/r8/generated/qualification_v2/stl/r8_matched_heavy_coffer_control.stl

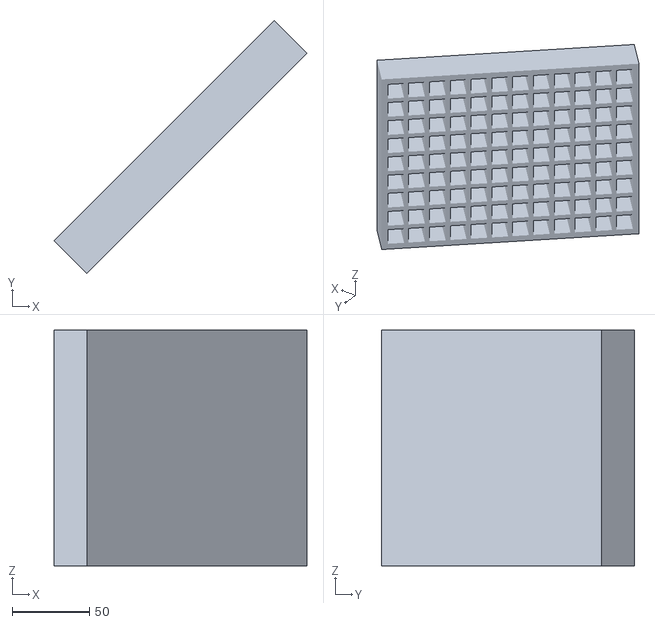
[picture p107: CAD file, 2026-08-11]
development/r8/generated/qualification_v2/stl/r8_matched_heavy_coffer_control.stl
163.4 x 163.4 x 152.4
