rupret007/story-corner-shelf/development/r9/generated/qualification_v5/individual_model_only_3mf/MODEL_ONLY_r9_under_shelf_shear_key_coupon.3mf

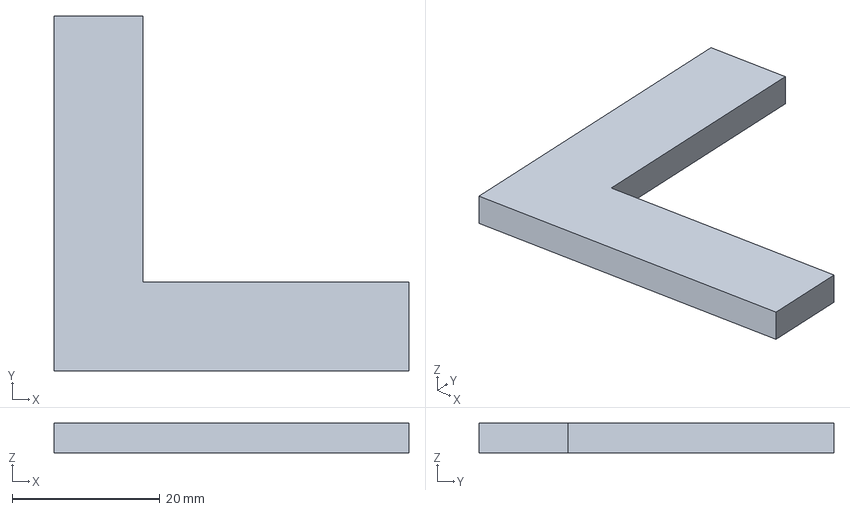
[picture p108: CAD file, 2026-08-11]
development/r9/generated/qualification_v5/individual_model_only_3mf/MODEL_ONLY_r9_under_shelf_shear_key_coupon.3mf
48.0 x 48.0 x 4.00 mm
