rupret007/story-corner-shelf/development/r9/generated/qualification_v5/stl/r9_cosmetic_corner_cover_coupon.stl

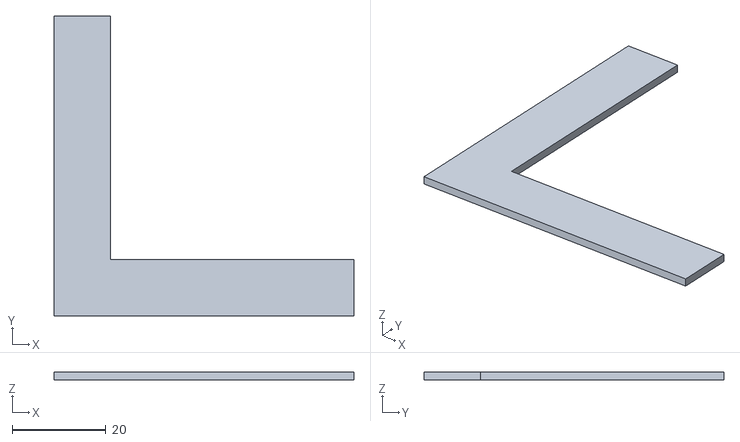
[picture p109: CAD file, 2026-08-11]
development/r9/generated/qualification_v5/stl/r9_cosmetic_corner_cover_coupon.stl
64.0 x 64.0 x 1.60
