rupret007/story-corner-shelf/generated/model_only_3mf/MODEL_ONLY_PETG_RearCurb_ParametricEnd_short_wall_3ft.3mf

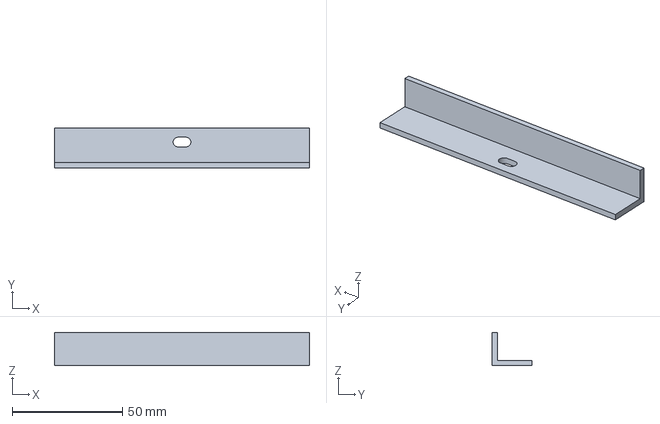
[picture p110: CAD file, 2026-08-18]
generated/model_only_3mf/MODEL_ONLY_PETG_RearCurb_ParametricEnd_short_wall_3ft.3mf
115.6 x 18.0 x 15.0 mm
