rupret007/story-corner-shelf/development/r8/generated/qualification_v2/stl/r8_clearance_key_0p3.stl

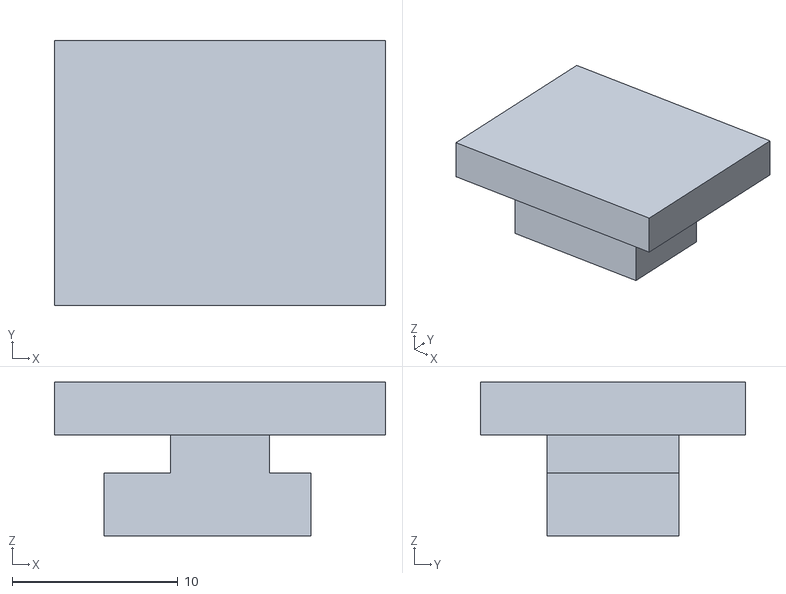
[picture p111: CAD file, 2026-08-11]
development/r8/generated/qualification_v2/stl/r8_clearance_key_0p3.stl
20.0 x 16.0 x 9.30
