rupret007/story-corner-shelf/development/r9/generated/qualification_v5/individual_model_only_3mf/MODEL_ONLY_r9_concealed_corner_half_control.3mf

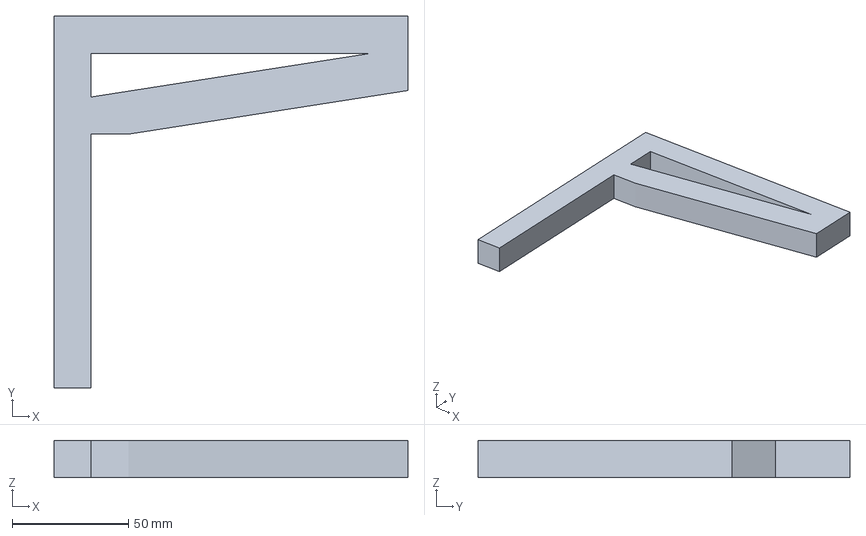
[picture p112: CAD file, 2026-08-11]
development/r9/generated/qualification_v5/individual_model_only_3mf/MODEL_ONLY_r9_concealed_corner_half_control.3mf
152.4 x 160.0 x 16.0 mm
