rupret007/story-corner-shelf/generated/PETG_Palatine_EntablatureOverlay_short_wall_3ft.stl

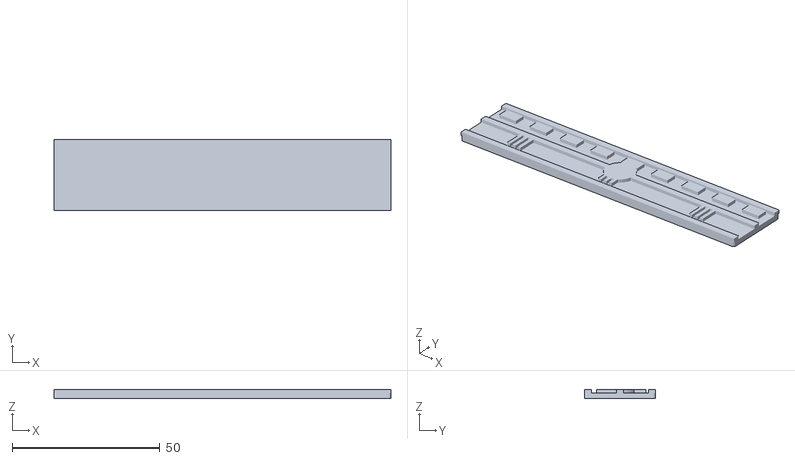
[picture p113: CAD file, 2026-08-18]
generated/PETG_Palatine_EntablatureOverlay_short_wall_3ft.stl
114.0 x 24.0 x 3.20
