rupret007/story-corner-shelf/development/r6/generated/individual_model_only_3mf/MODEL_ONLY_R6_DEV_CASSETTE_THROUGH_04_OF_12.3mf

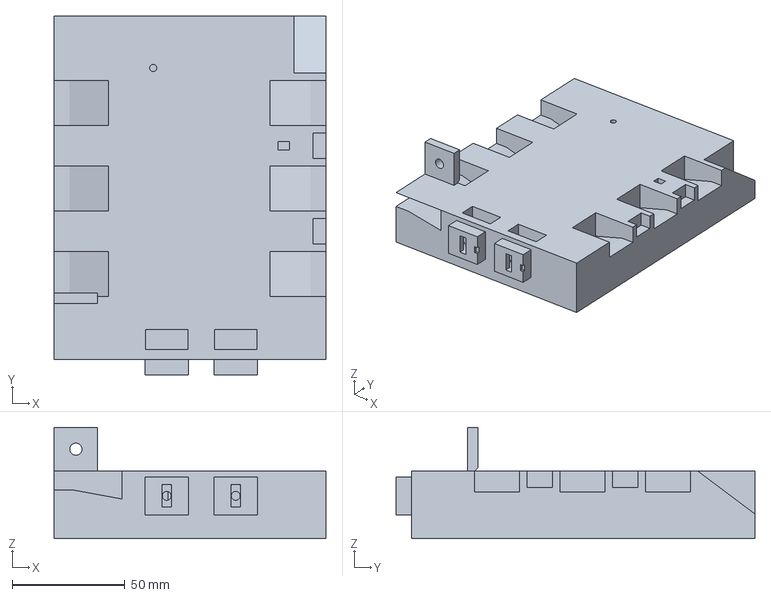
[picture p114: CAD file, 2026-08-09]
development/r6/generated/individual_model_only_3mf/MODEL_ONLY_R6_DEV_CASSETTE_THROUGH_04_OF_12.3mf
120.6 x 159.2 x 49.4 mm
