rupret007/story-corner-shelf/generated/PRINT_FIRST_FasciaFitCoupon.stl

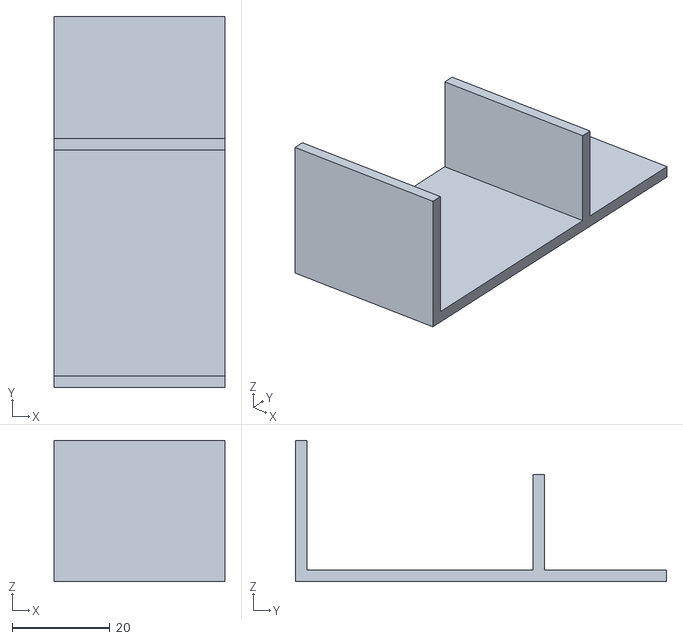
[picture p115: CAD file, 2026-08-18]
generated/PRINT_FIRST_FasciaFitCoupon.stl
35.0 x 76.1 x 29.0
