rupret007/story-corner-shelf/development/r9/generated/one_bay_prototype_v3/ASSEMBLY.md

# R9 Palatine Moderne one-bay tabletop assembly

All five parts must be fully cool, clean, and free of cracks, layer separation,
rocking, visible warp, or damaged interfaces before assembly.

Read `MATERIALS_AND_HARDWARE.md` first. Confirm that each support has three
clean, fully open diamond wall-mount bores at 16, 80, and 144 mm below the
shelf underside. A nominal 7.0 mm round gauge may pass without force; do not
drill, ream, file, or countersink a printed bore. This inspection does not
authorize wall installation.

## Identify the parts

- Left support: member sockets open on its right/inside face.
- Right support: member sockets open on its left/inside face.
- Rear ledger: installs at the wall side of the bay.
- Front beam: installs at the front edge.
- Shelf cassette: finished textured face is the top; its open webbed face is
  underneath.

## Assemble, unloaded

1. Stand the left and right supports upright on a padded flat table, with their
   socket faces pointing inward.  Keep their outer faces 160 mm apart.
2. Align both rear-ledger tongues over the rear top-open sockets.  Lower the
   member vertically until its shoulders meet both support faces.  Stop at the
   first resistance beyond light guidance.
3. Repeat with the front beam and the two front top-open sockets.  Both
   supports must remain square without twist.
4. Orient the cassette with its finished top upward.  Align the four underside
   pockets over the four support bosses and lower it vertically.  Do not rock
   or lever it into place.
5. Photograph the front, rear, both sides, underside, and top.  On the padded
   table only, gently check for rocking and visible gaps.  Do not place an
   object or hand load on the shelf.

## Disassemble

Lift the cassette vertically.  Lift the front beam and rear ledger vertically,
then separate the supports.  Inspect every tongue, socket,
boss, and pocket for whitening, abrasion, cracking, permanent deformation, or
increasing bind.  Complete ten gentle assembly/removal cycles only if every
prior cycle remains clean.

## Pass meaning

A pass authorizes CAD work on the measured full L-shaped set.  It does not
authorize wall bores, installation, stored load, a load rating, or production
quantities.
