rupret007/story-corner-shelf/development/r9/visuals/r9_compact_bookend_concept_assembly-v2.png

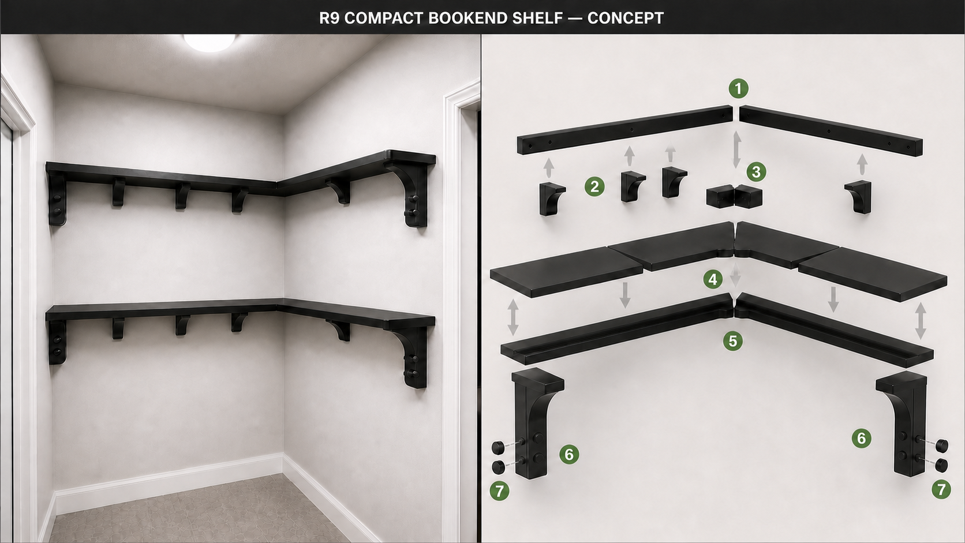
development/r9/visuals/r9_compact_bookend_concept_assembly-v2.png
